ToyotaInfoTech/RAMN/docs/firmware/img/external_clock_settings.png

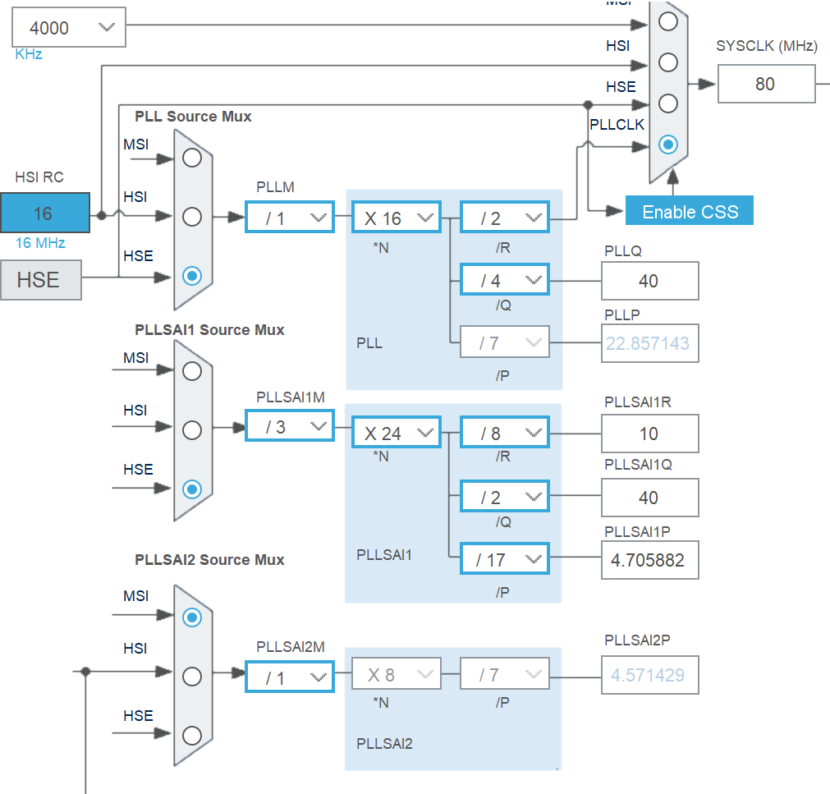
docs/firmware/img/external_clock_settings.png
