ToyotaInfoTech/RAMN/docs/firmware/img/freertos_settings.png

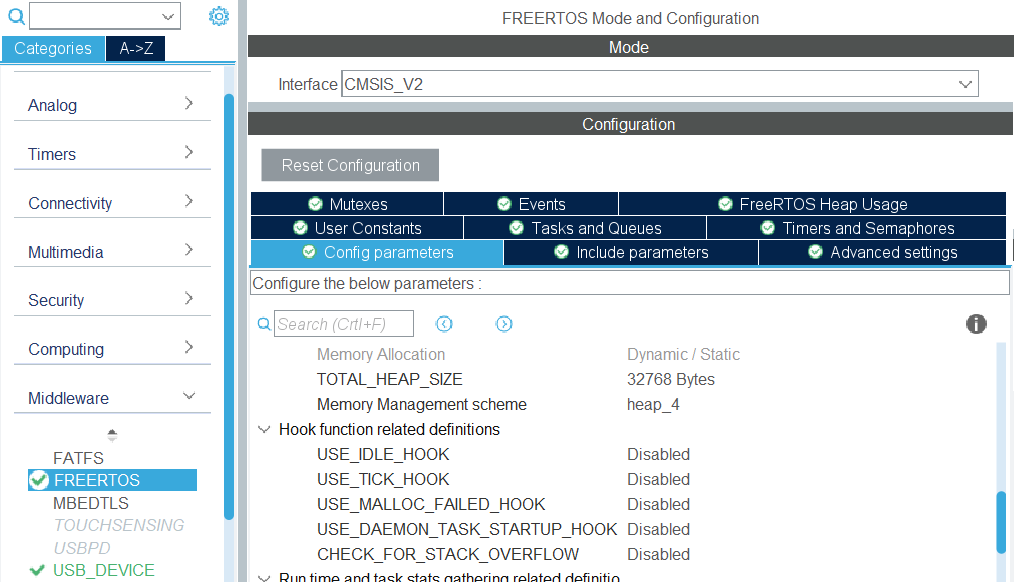
docs/firmware/img/freertos_settings.png
