ToyotaInfoTech/RAMN/docs/firmware/img/internal_clock_settings.png

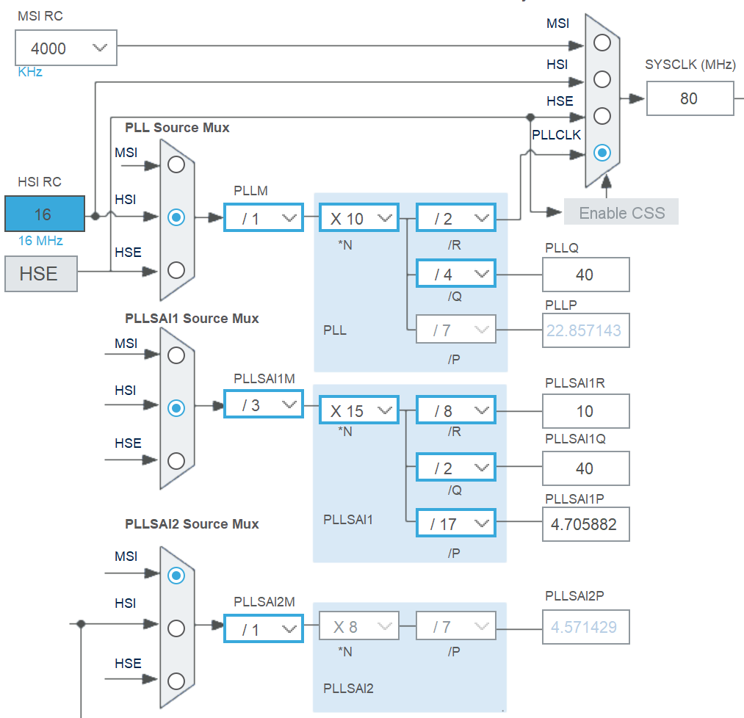
docs/firmware/img/internal_clock_settings.png
