ToyotaInfoTech/RAMN/docs/firmware/img/optionbytes_bootmode.png

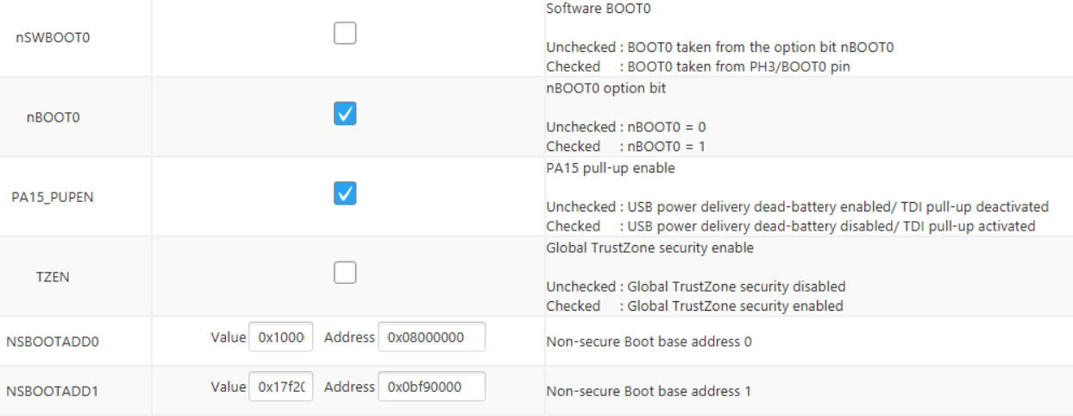
docs/firmware/img/optionbytes_bootmode.png
