ToyotaInfoTech/RAMN/docs/img/writeups/chv_ecub_4.png

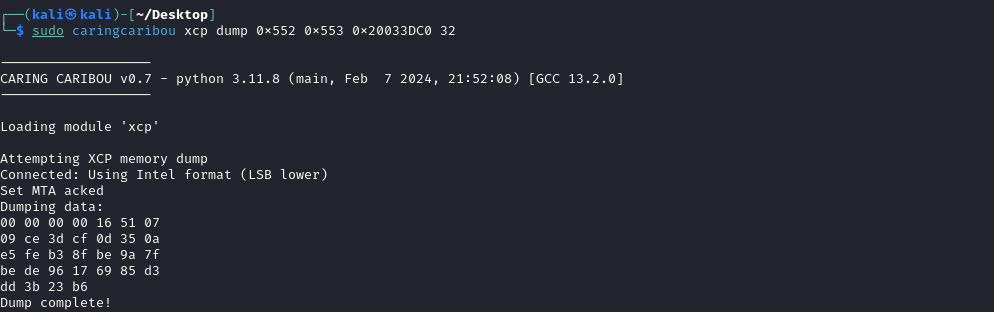
docs/img/writeups/chv_ecub_4.png
