ToyotaInfoTech/RAMN/hardware/V1_revB/0_ramn/CAD/ramn.png

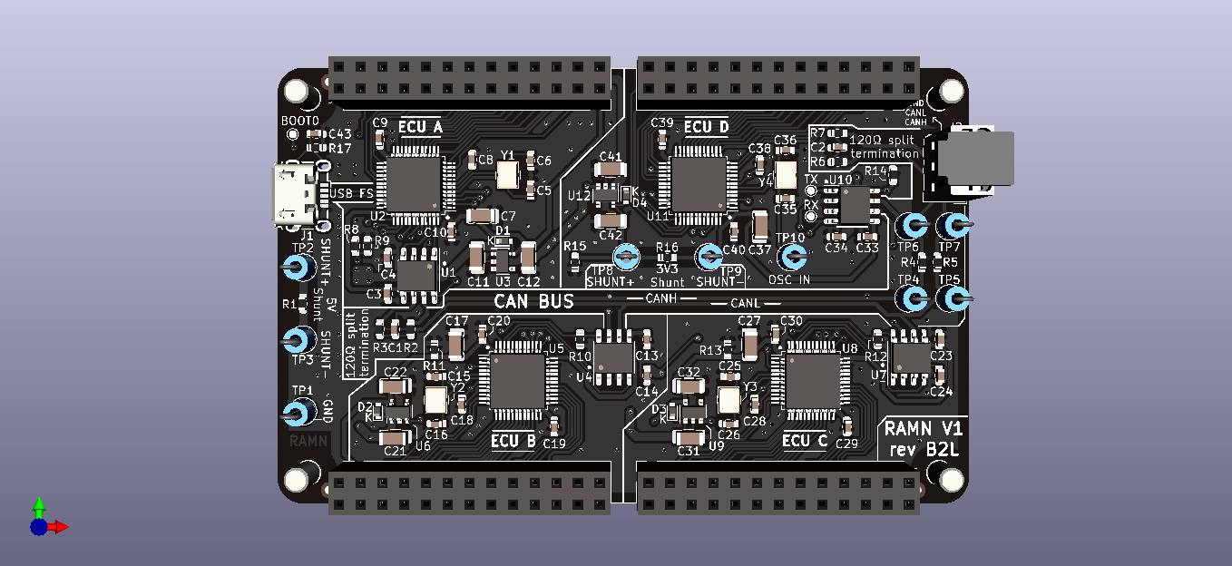
hardware/V1_revB/0_ramn/CAD/ramn.png
