ToyotaInfoTech/RAMN/hardware/V1_revB/0_ramn/CAD/ramn_back.png

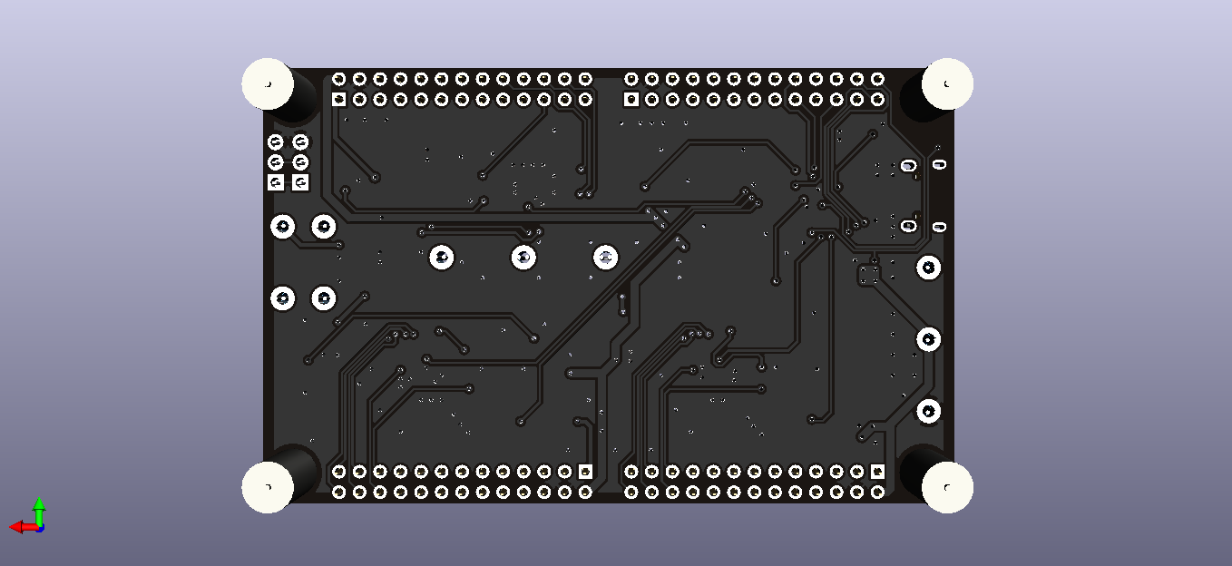
hardware/V1_revB/0_ramn/CAD/ramn_back.png
