ToyotaInfoTech/RAMN/hardware/V1_revB/0_ramn/CAD/ramn_tilt.png

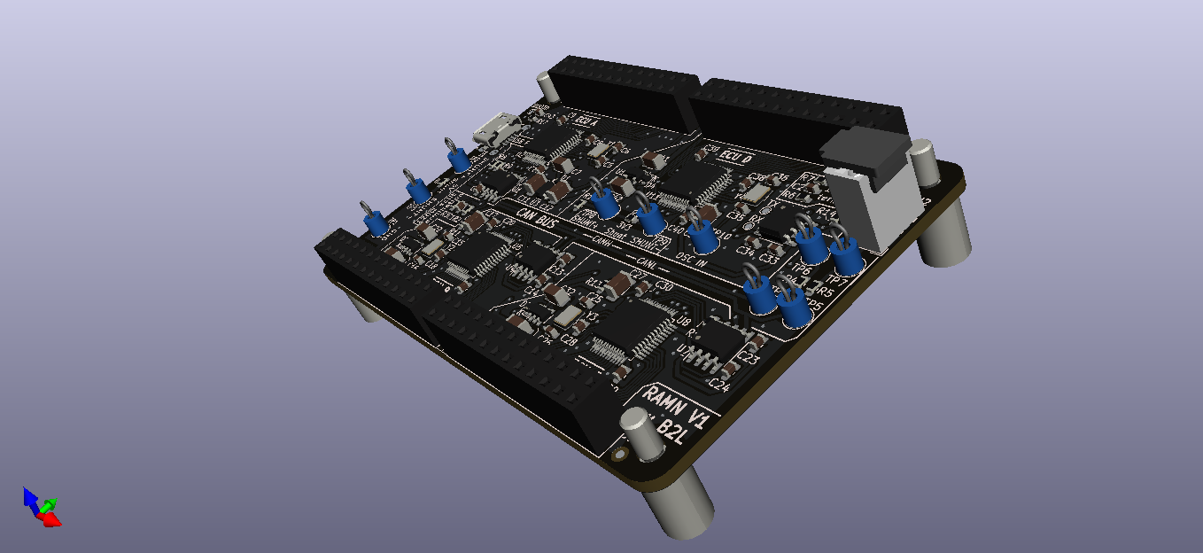
hardware/V1_revB/0_ramn/CAD/ramn_tilt.png
