ToyotaInfoTech/RAMN/scripts/diagnostics/FILES/image.png

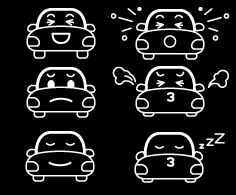
scripts/diagnostics/FILES/image.png
