ToyotaInfoTech/RAMN/docs/userguide.rst

.. _userguide:

User Guide
==========

This section contains the user guide for RAMN, explaining how to use its USB, CAN, and UDS features.
If your goal is to customize RAMN, check the :ref:`customizing_guide`.

.. toctree::
   :maxdepth: 3

   userguide/ramn_introduction
   userguide/can_tutorial
   userguide/isotp_tutorial
   userguide/diag_tutorial
   userguide/usb_tutorial
   userguide/protocol_tutorial
   userguide/going_further
