ToyotaInfoTech/RAMN/docs/hardware/fabrication.rst

.. toctree::
   :maxdepth: 2

   Fabrication/ordering.rst
   Fabrication/flashing.rst
   Fabrication/qualitycheck.rst
