ToyotaInfoTech/RAMN/hardware/V1_revB/0_ramn/ramn.pdf

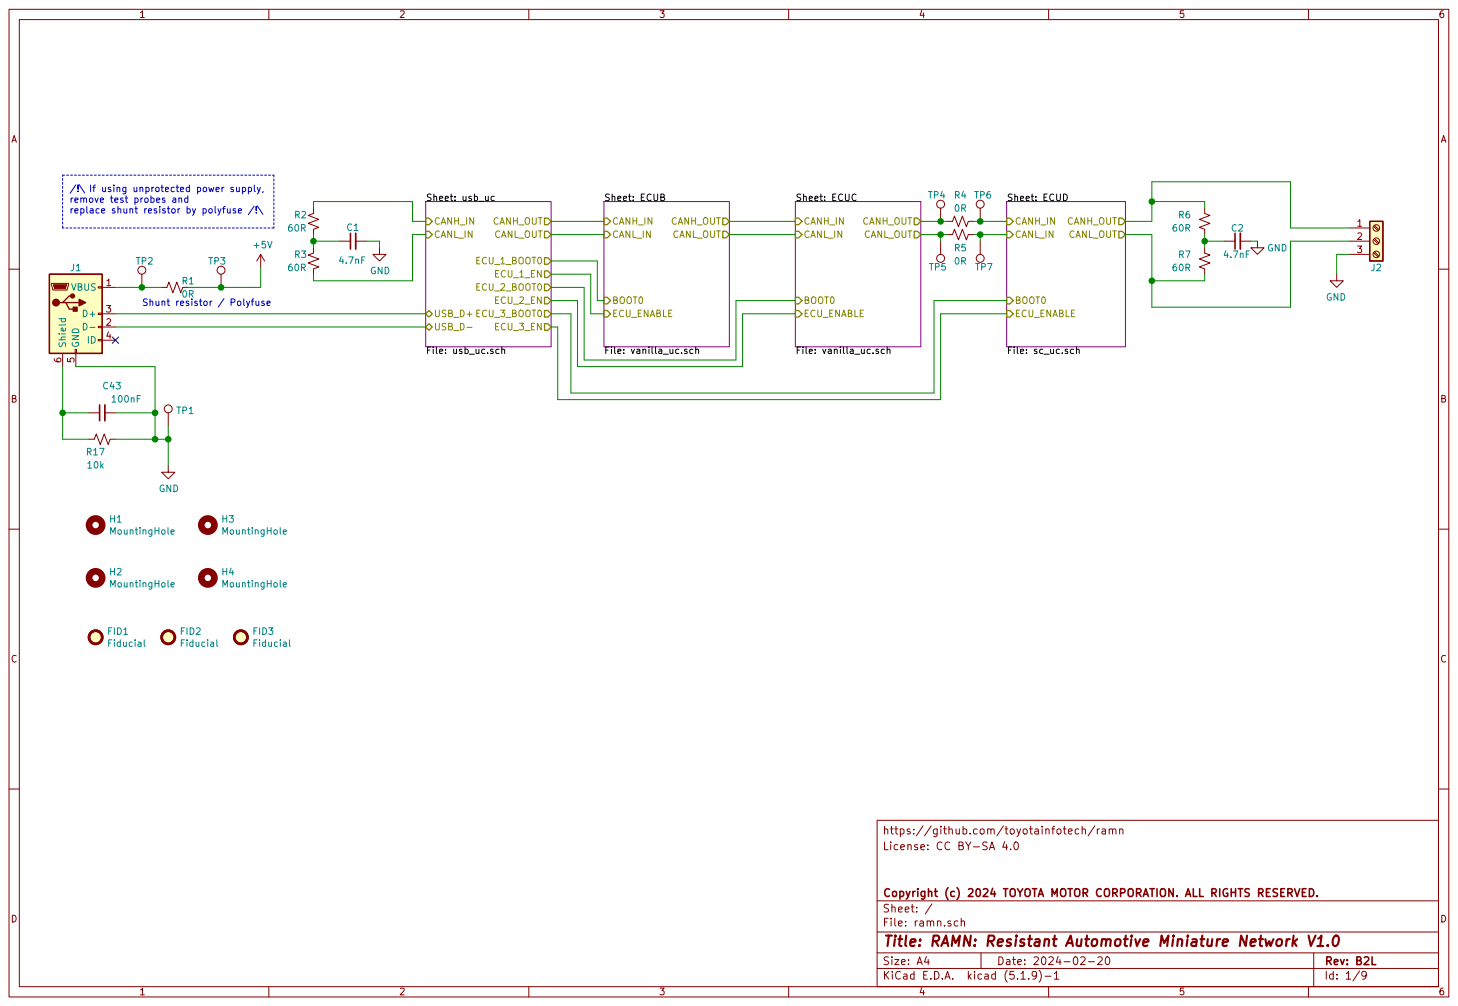
[picture p171: page 1]

/!\ If using unprotected power supply,
remove test probes and
replace shunt resistor by polyfuse /!\

https://github.com/toyotainfotech/ramn
File: ramn.sch Sheet: / Copyright (c) 2024 TOYOTA MOTOR CORPORATION. ALL RIGHTS RESERVED. License: CC BY-SA 4.0

Id: 1/9 Title: RAMN: Resistant Automotive Miniature Network V1.0

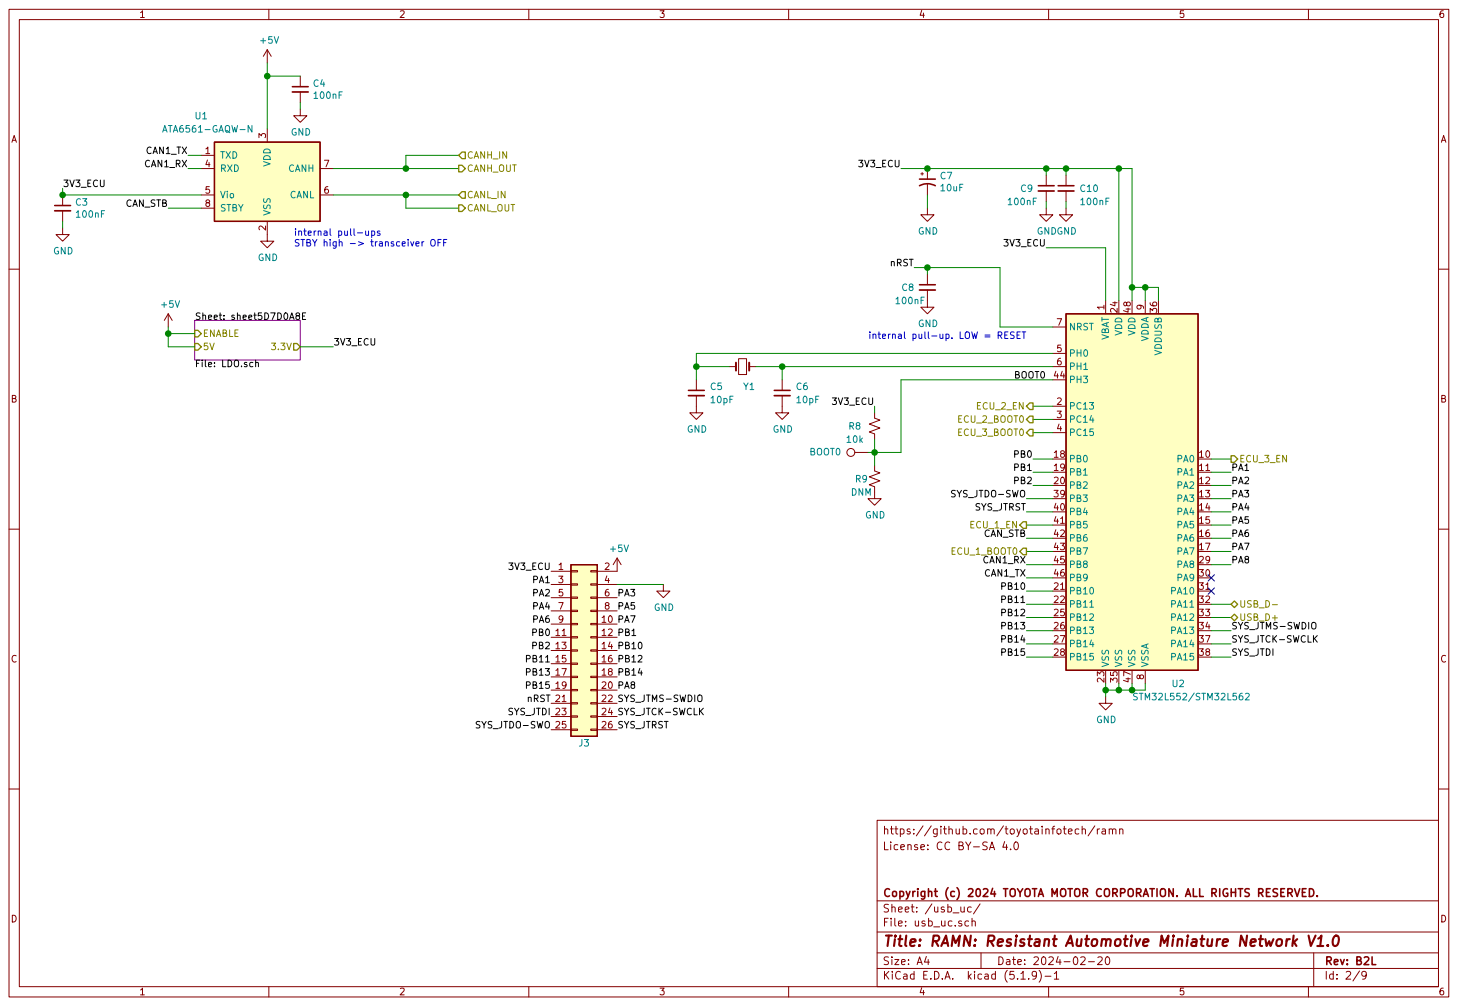
[picture p172: page 2]

3 RXD 4 Vio 5 CANL 6 CANH 7 STBY 8 U1 ATA6561-GAQW-N GND

internal pull-ups
STBY high -> transceiver OFF

9 VDDUSB 36 VSS 23 VSS 35 VSS 47 VSSA

internal pull-up. LOW = RESET

https://github.com/toyotainfotech/ramn
Copyright (c) 2024 TOYOTA MOTOR CORPORATION. ALL RIGHTS RESERVED. License: CC BY-SA 4.0

Sheet: /usb_uc/
File: usb_uc.sch
Id: 2/9 Title: RAMN: Resistant Automotive Miniature Network V1.0

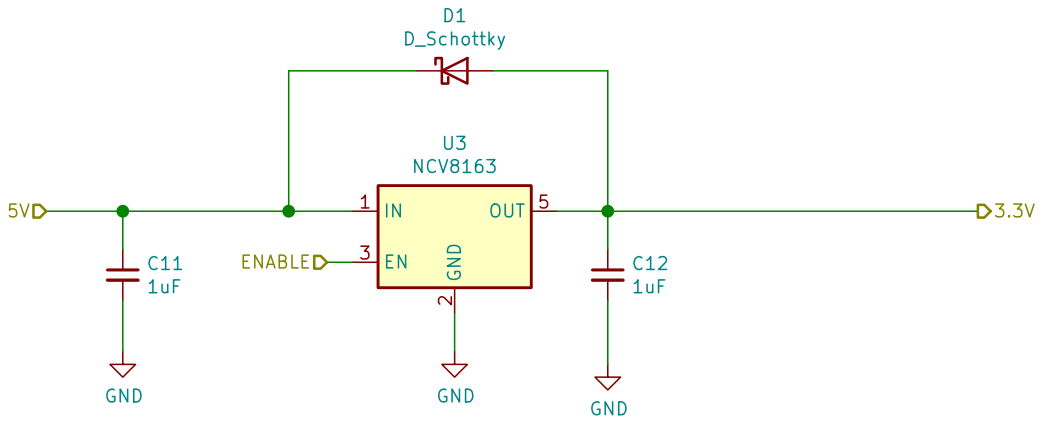
[picture p173: page 3]
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

File: LDO.sch Sheet: /usb_uc/sheet5D7D0A8E/
Id: 3/9 Title: RAMN: Resistant Automotive Miniature Network V1.0

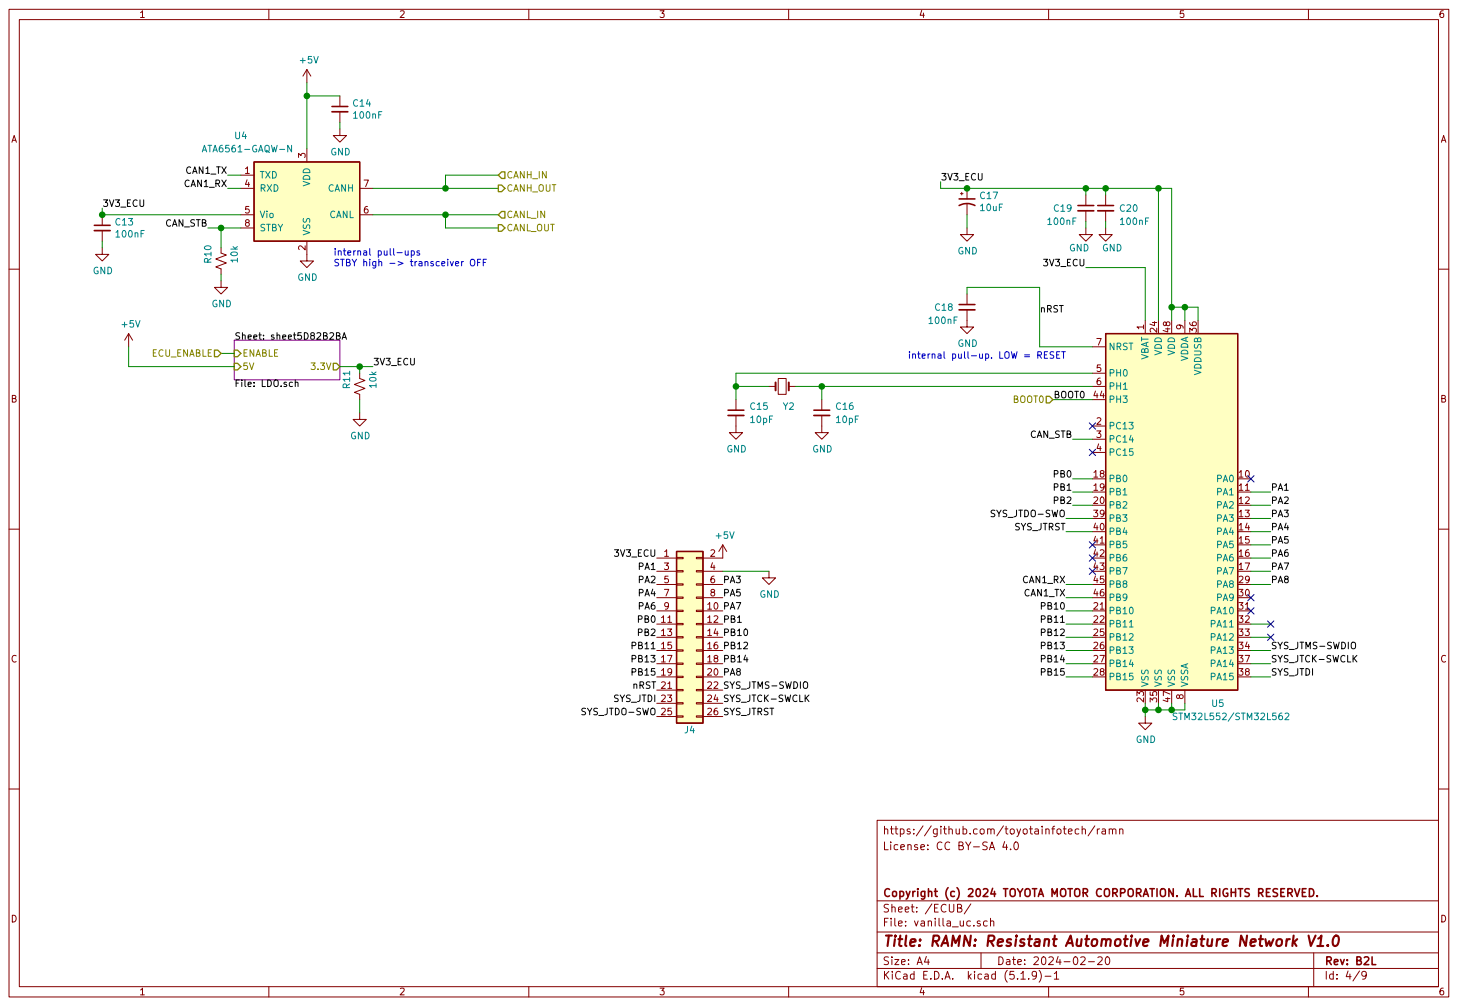
[picture p174: page 4]

3 RXD 4 Vio 5 CANL 6 CANH 7 STBY 8 U4 ATA6561-GAQW-N GND GND GND GND

internal pull-ups
STBY high -> transceiver OFF

9 VDDUSB 36 VSS 23 VSS 35 VSS 47 VSSA

internal pull-up. LOW = RESET

https://github.com/toyotainfotech/ramn
File: vanilla_uc.sch Sheet: /ECUB/ Copyright (c) 2024 TOYOTA MOTOR CORPORATION. ALL RIGHTS RESERVED. License: CC BY-SA 4.0

Id: 4/9 Title: RAMN: Resistant Automotive Miniature Network V1.0

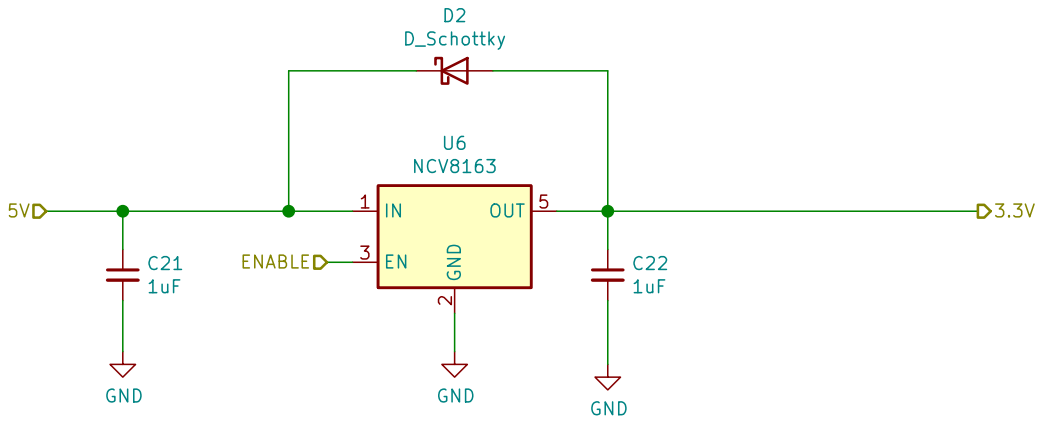
[picture p175: page 5]

https://github.com/toyotainfotech/ramn
File: LDO.sch Sheet: /ECUB/sheet5D82B2BA/ Copyright (c) 2024 TOYOTA MOTOR CORPORATION. ALL RIGHTS RESERVED. License: CC BY-SA 4.0

Id: 5/9 Title: RAMN: Resistant Automotive Miniature Network V1.0

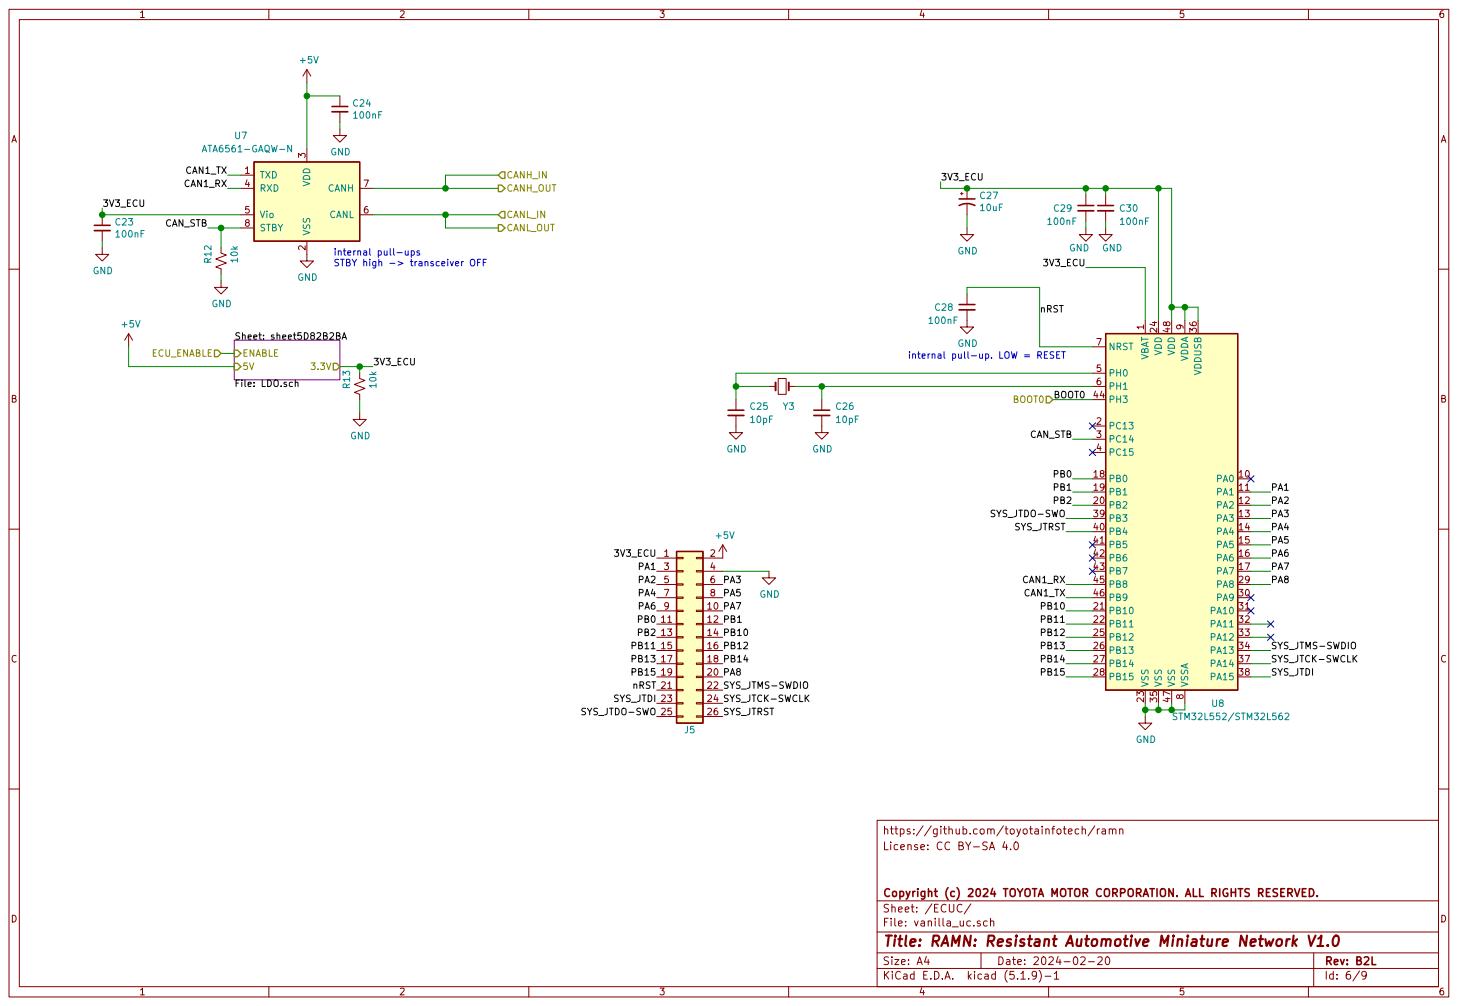
[picture p176: page 6]

3 RXD 4 Vio 5 CANL 6 CANH 7 STBY 8 U7 ATA6561-GAQW-N GND GND GND GND

internal pull-ups
STBY high -> transceiver OFF

9 VDDUSB 36 VSS 23 VSS 35 VSS 47 VSSA

internal pull-up. LOW = RESET

https://github.com/toyotainfotech/ramn
File: vanilla_uc.sch Sheet: /ECUC/ Copyright (c) 2024 TOYOTA MOTOR CORPORATION. ALL RIGHTS RESERVED. License: CC BY-SA 4.0

Id: 6/9 Title: RAMN: Resistant Automotive Miniature Network V1.0

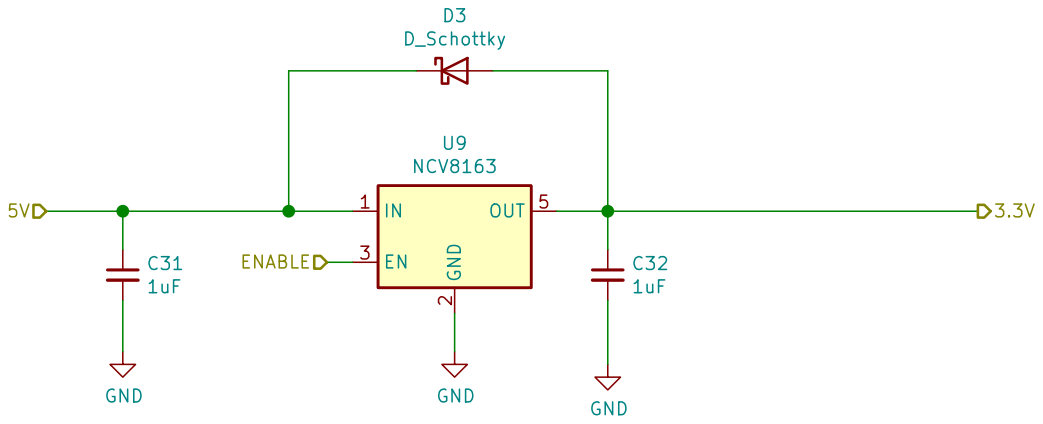
[picture p177: page 7]

https://github.com/toyotainfotech/ramn
File: LDO.sch Sheet: /ECUC/sheet5D82B2BA/ Copyright (c) 2024 TOYOTA MOTOR CORPORATION. ALL RIGHTS RESERVED. License: CC BY-SA 4.0

Id: 7/9 Title: RAMN: Resistant Automotive Miniature Network V1.0

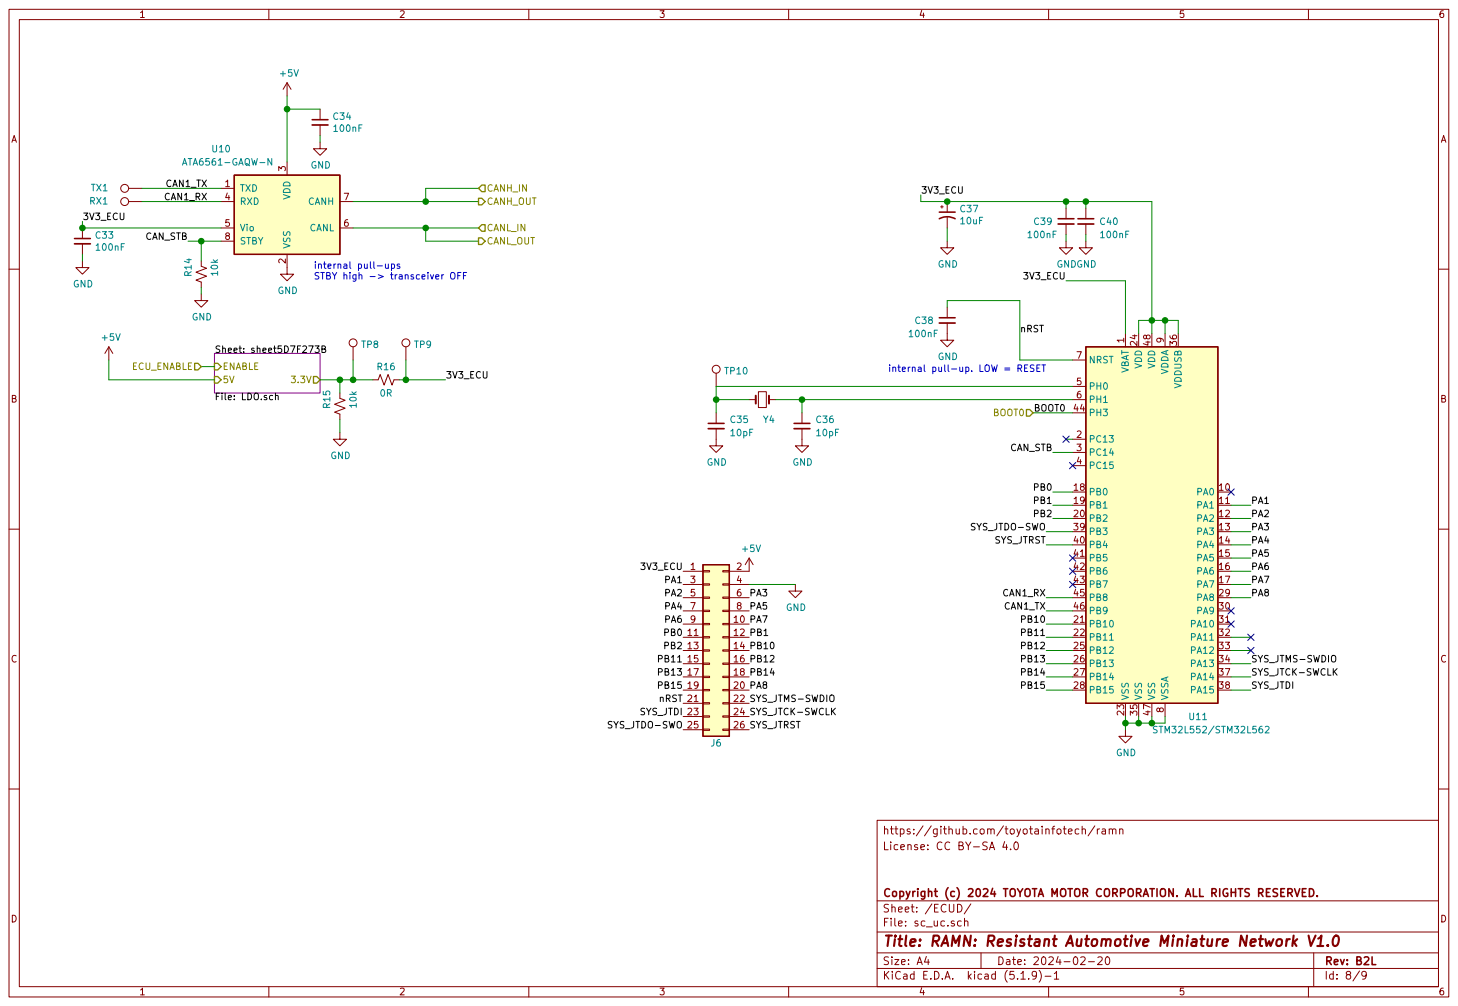
[picture p178: page 8]

3 RXD 4 Vio 5 CANL 6 CANH 7 STBY 8 U10 ATA6561-GAQW-N GND GND

internal pull-ups
STBY high -> transceiver OFF

9 VDDUSB 36 VSS 23 VSS 35 VSS 47 VSSA

internal pull-up. LOW = RESET

https://github.com/toyotainfotech/ramn
File: sc_uc.sch Sheet: /ECUD/ Copyright (c) 2024 TOYOTA MOTOR CORPORATION. ALL RIGHTS RESERVED. License: CC BY-SA 4.0

Id: 8/9 Title: RAMN: Resistant Automotive Miniature Network V1.0

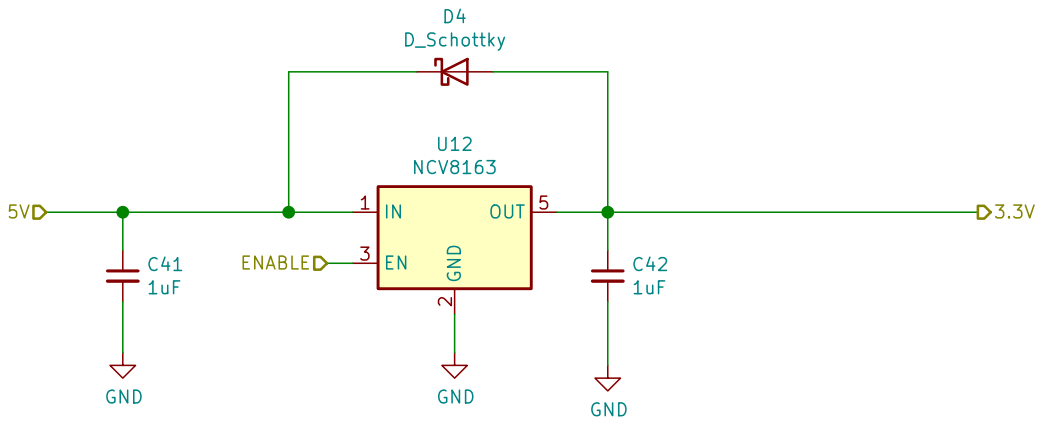
[picture p179: page 9]

https://github.com/toyotainfotech/ramn
File: LDO.sch Sheet: /ECUD/sheet5D7F273B/ Copyright (c) 2024 TOYOTA MOTOR CORPORATION. ALL RIGHTS RESERVED. License: CC BY-SA 4.0

Id: 9/9 Title: RAMN: Resistant Automotive Miniature Network V1.0
