ToyotaInfoTech/RAMN/hardware/V1_revB/1_screens/screens.pdf

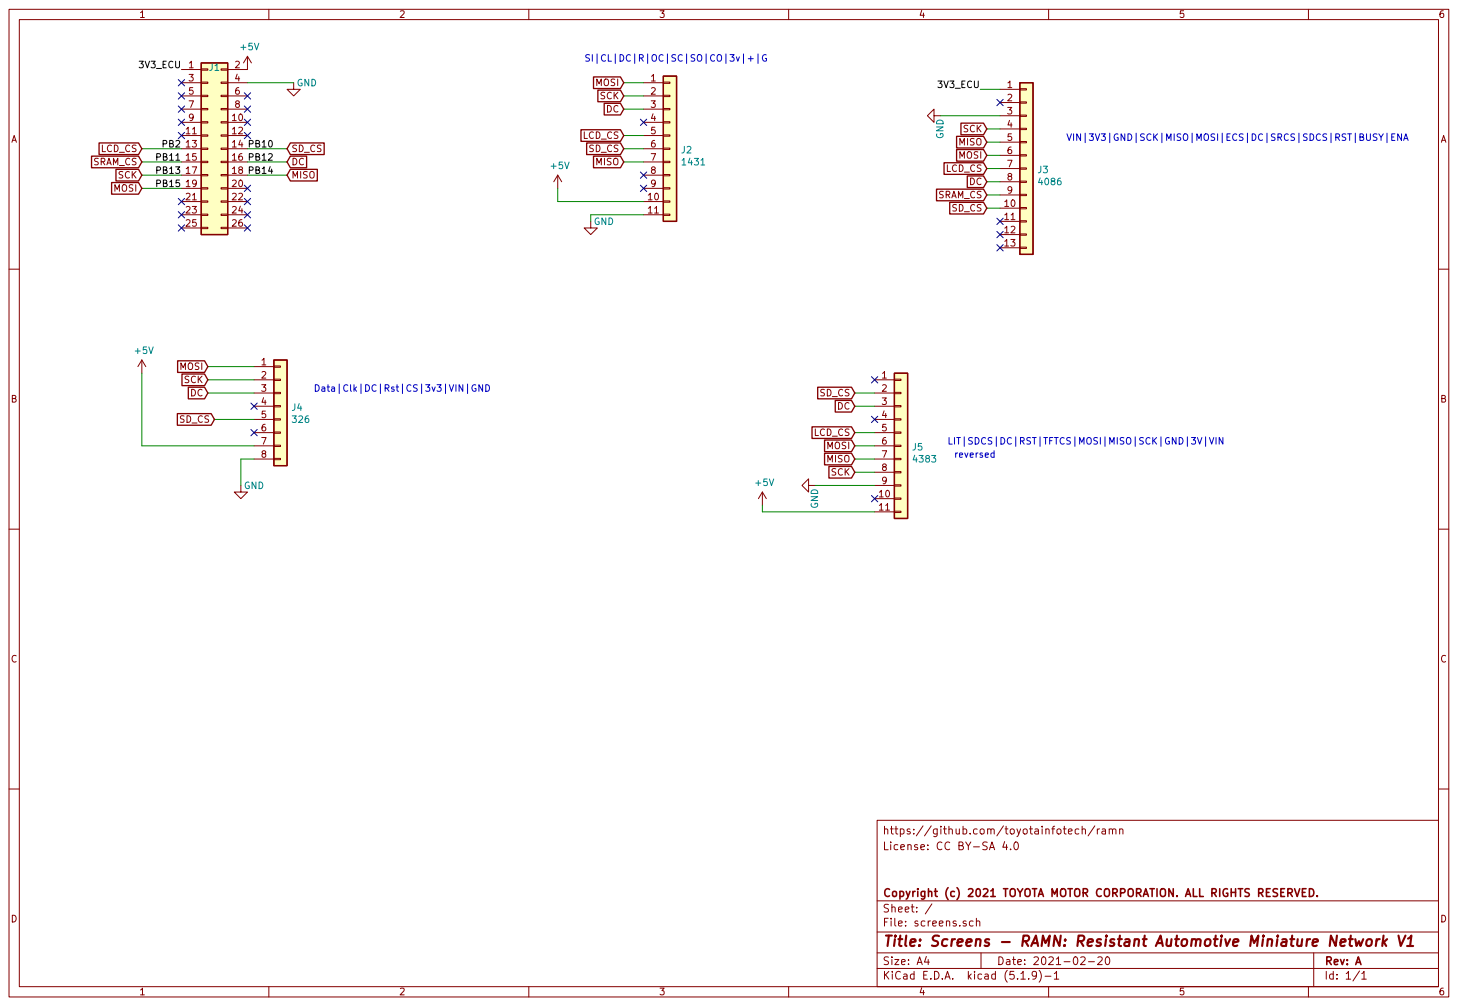
[picture p180: page 1]

reversed SI|CL|DC|R|OC|SC|SO|CO|3v|+|G

VIN|3V3|GND|SCK|MISO|MOSI|ECS|DC|SRCS|SDCS|RST|BUSY|ENA

Data|Clk|DC|Rst|CS|3v3|VIN|GND

LIT|SDCS|DC|RST|TFTCS|MOSI|MISO|SCK|GND|3V|VIN

https://github.com/toyotainfotech/ramn
File: screens.sch Sheet: / Copyright (c) 2021 TOYOTA MOTOR CORPORATION. ALL RIGHTS RESERVED. License: CC BY-SA 4.0

Id: 1/1 Title: Screens - RAMN: Resistant Automotive Miniature Network V1
