ToyotaInfoTech/RAMN/hardware/V1_revB/2_chassis/chassis.pdf

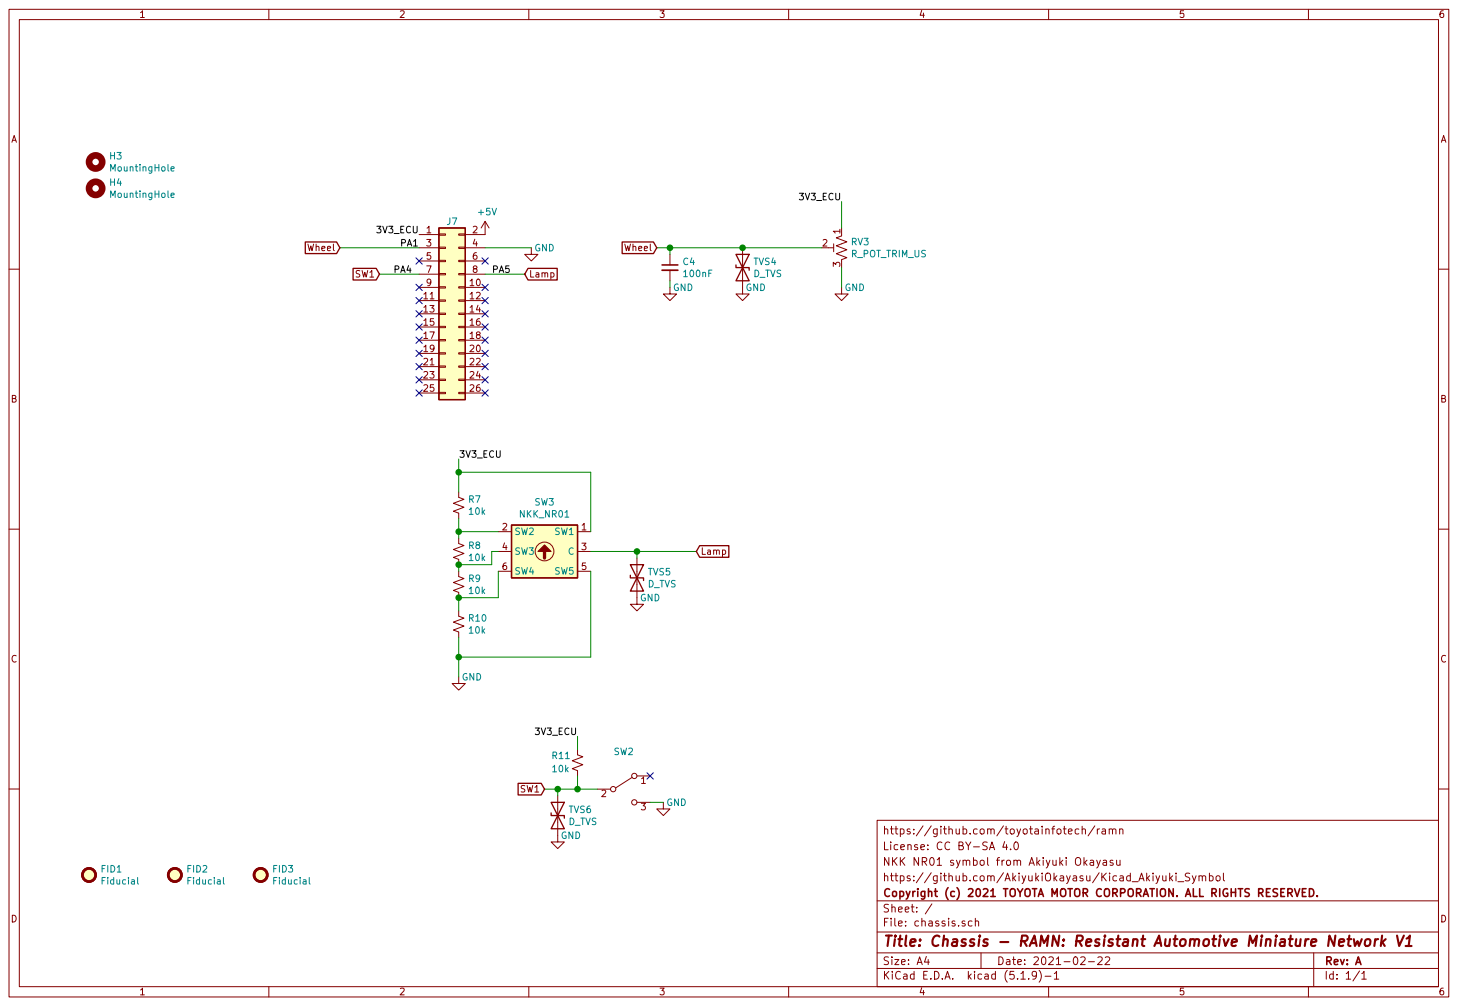
[picture p181: page 1]

https://github.com/toyotainfotech/ramn
License: CC BY-SA 4.0
NKK NR01 symbol from Akiyuki Okayasu
https://github.com/AkiyukiOkayasu/Kicad_Akiyuki_Symbol
File: chassis.sch Sheet: / Copyright (c) 2021 TOYOTA MOTOR CORPORATION. ALL RIGHTS RESERVED.

Id: 1/1 Title: Chassis - RAMN: Resistant Automotive Miniature Network V1
