ToyotaInfoTech/RAMN/hardware/V1_revB/3_powertrain/powertrain.pdf

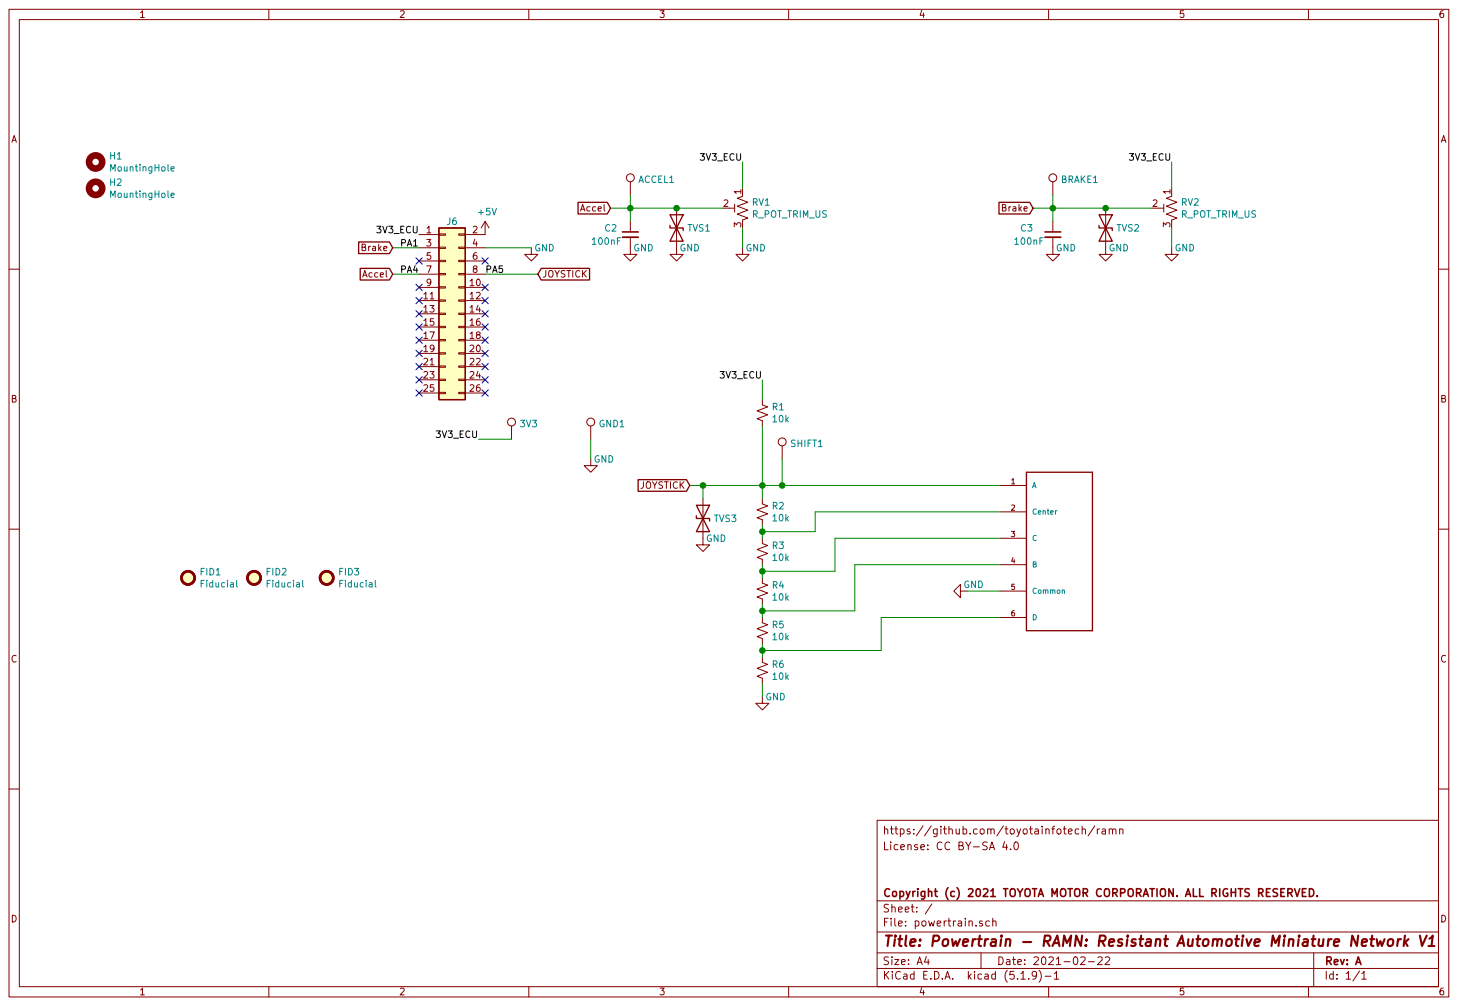
[picture p182: page 1]

3 RV1 R_POT_TRIM_US H2MountingHole H1MountingHole TVS2 FID2 Fiducial +5V GND GND GND

https://github.com/toyotainfotech/ramn
File: powertrain.sch Sheet: / Copyright (c) 2021 TOYOTA MOTOR CORPORATION. ALL RIGHTS RESERVED. License: CC BY-SA 4.0

Id: 1/1 Title: Powertrain - RAMN: Resistant Automotive Miniature Network V1
