ToyotaInfoTech/RAMN/hardware/V1_revB/4_body/body.pdf

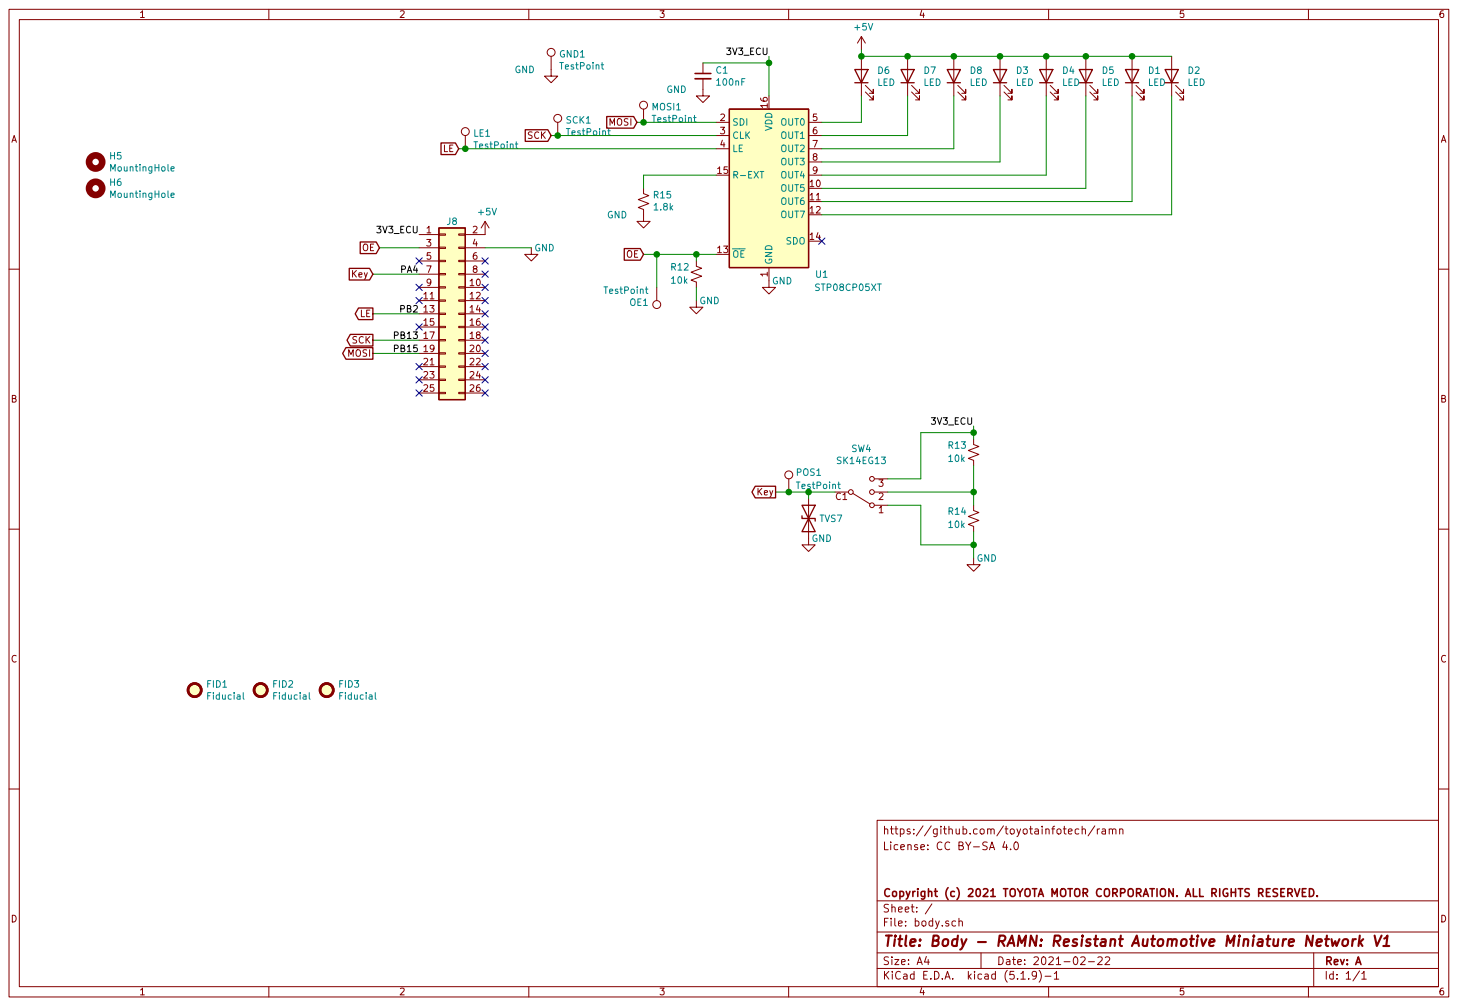
[picture p183: page 1]

1 OUT5 10 OUT6 11 OUT7 12 OE 13 SDO 14 R-EXT 15 VDD 16 SDI 2 CLK 3

https://github.com/toyotainfotech/ramn
File: body.sch Sheet: / Copyright (c) 2021 TOYOTA MOTOR CORPORATION. ALL RIGHTS RESERVED. License: CC BY-SA 4.0

Id: 1/1 Title: Body - RAMN: Resistant Automotive Miniature Network V1
