ToyotaInfoTech/RAMN/hardware/V1_revB/1_screens/CAD/screens-F_SilkS.pdf

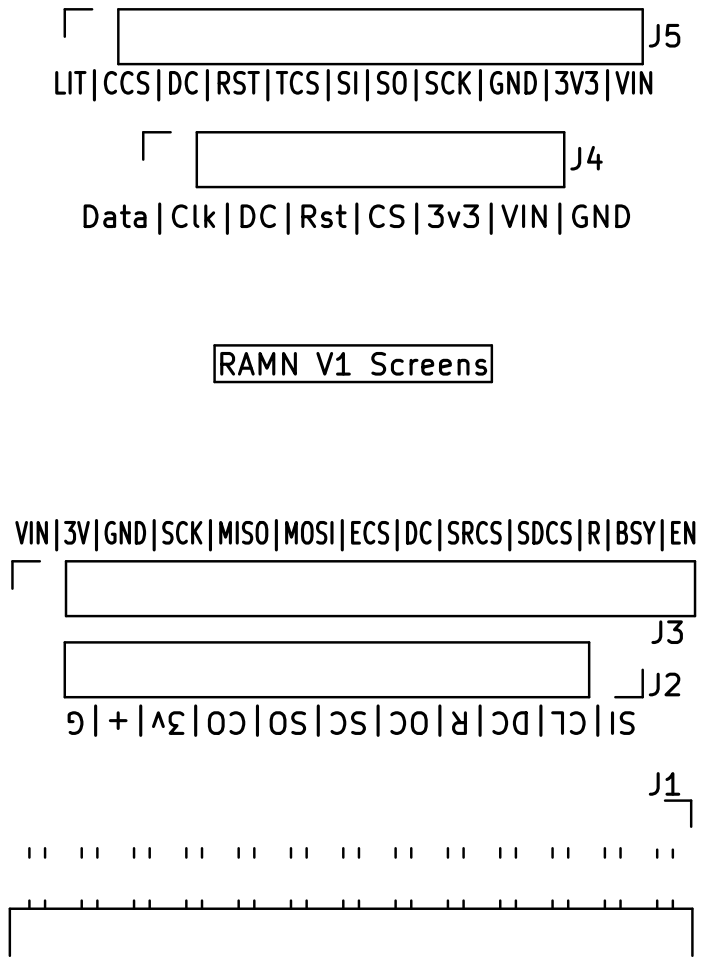
[picture p184: page 1]

LIT|CCS|DC|RST|TCS|SI|SO|SCK|GND|3V3|VIN

Data|Clk|DC|Rst|CS|3v3|VIN|GND

RAMN V1 Screens VIN|3V|GND|SCK|MISO|MOSI|ECS|DC|SRCS|SDCS|R|BSY|EN
