ToyotaInfoTech/RAMN/hardware/V1_revB/4_body/CAD/body-F_SilkS.pdf

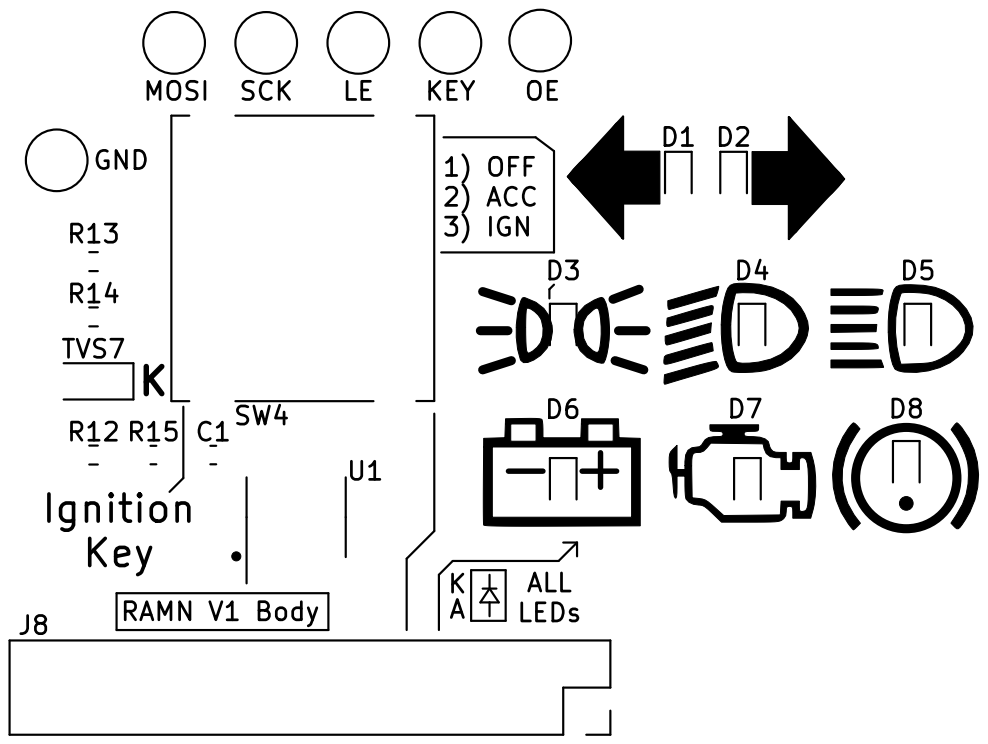
[picture p185: page 1]

RAMN V1 Body LE GND
