ToyotaInfoTech/RAMN/hardware/V1_revB/3_powertrain/CAD/powertrain-B_Cu.pdf

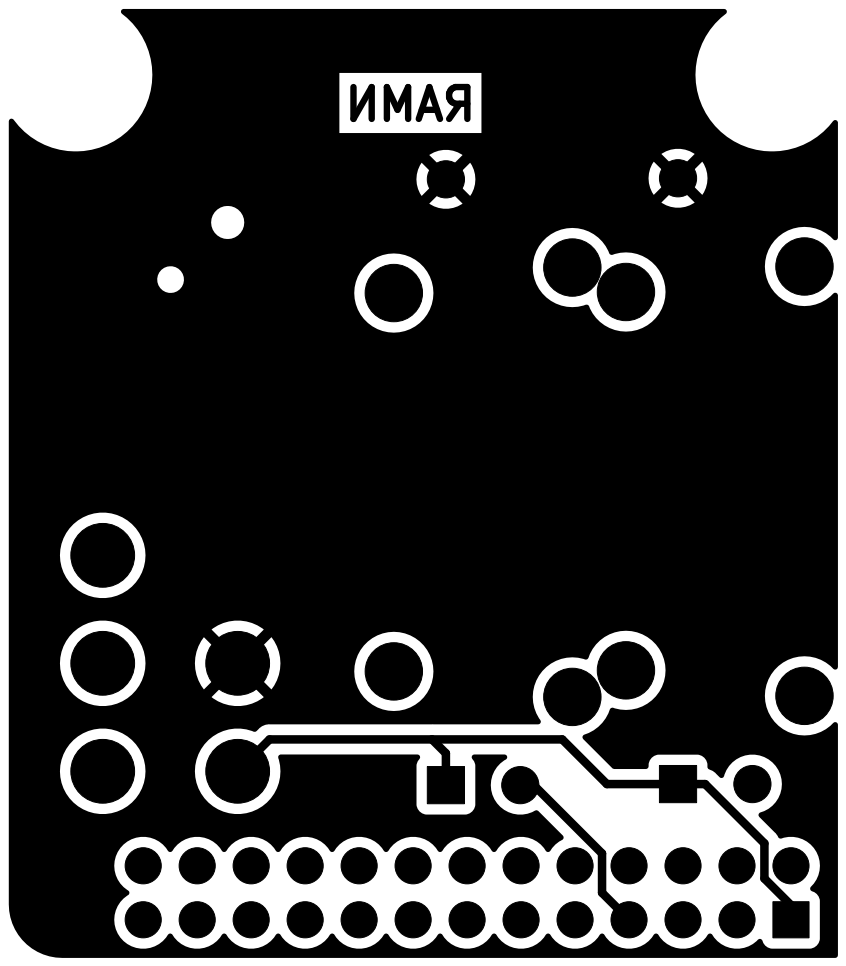
[picture p190: page 1]
