ToyotaInfoTech/RAMN/hardware/V1_revB/3_powertrain/CAD/powertrain-B_Mask.pdf

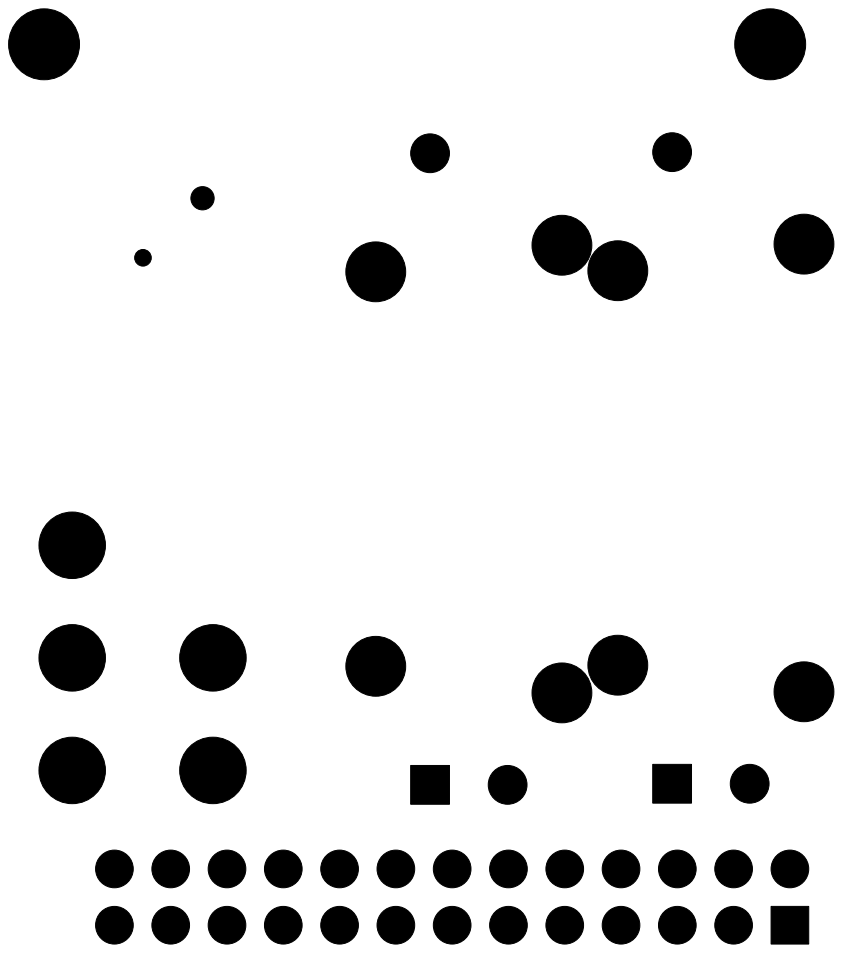
[picture p191: page 1]
