ToyotaInfoTech/RAMN/hardware/V1_revB/3_powertrain/CAD/powertrain-Edge_Cuts.pdf

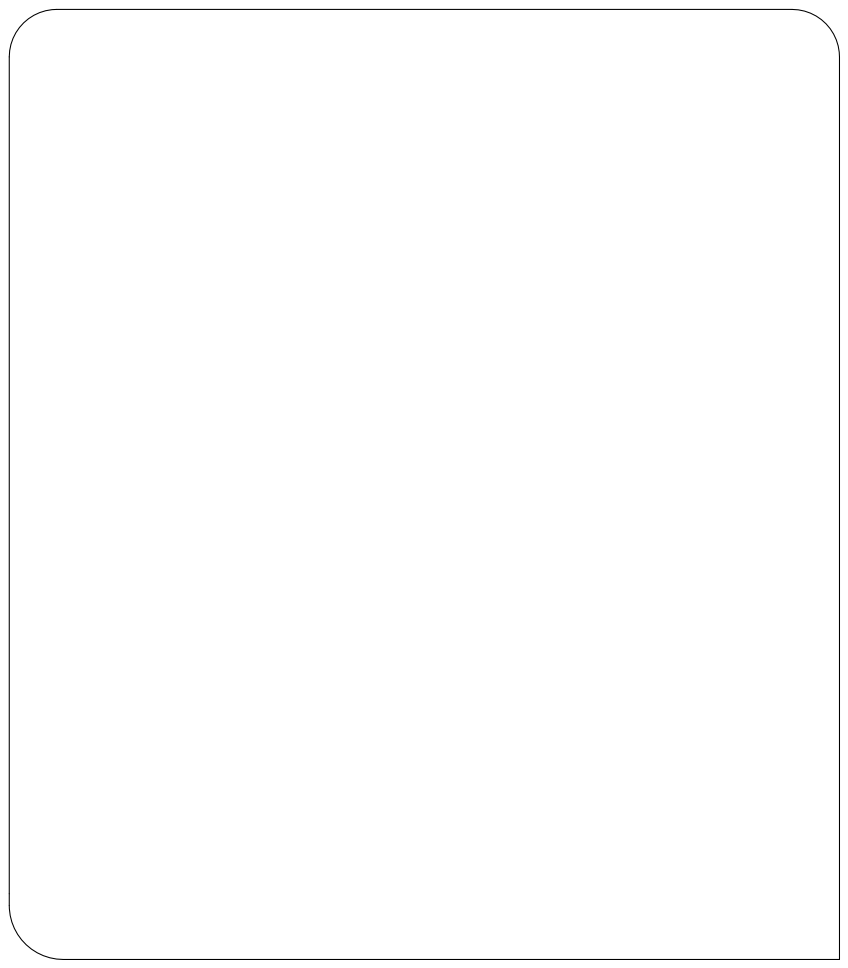
[picture p192: page 1]
