ToyotaInfoTech/RAMN/hardware/V1_revB/3_powertrain/CAD/powertrain-F_Cu.pdf

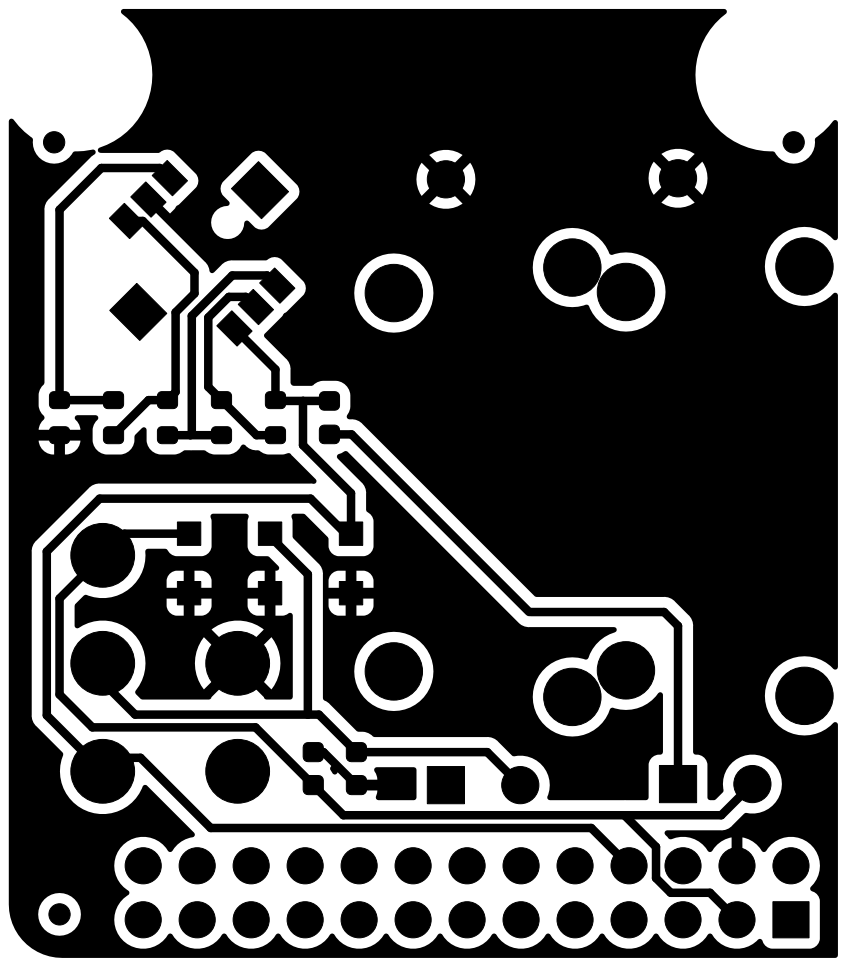
[picture p193: page 1]
