ToyotaInfoTech/RAMN/hardware/V1_revB/3_powertrain/CAD/powertrain-F_Mask.pdf

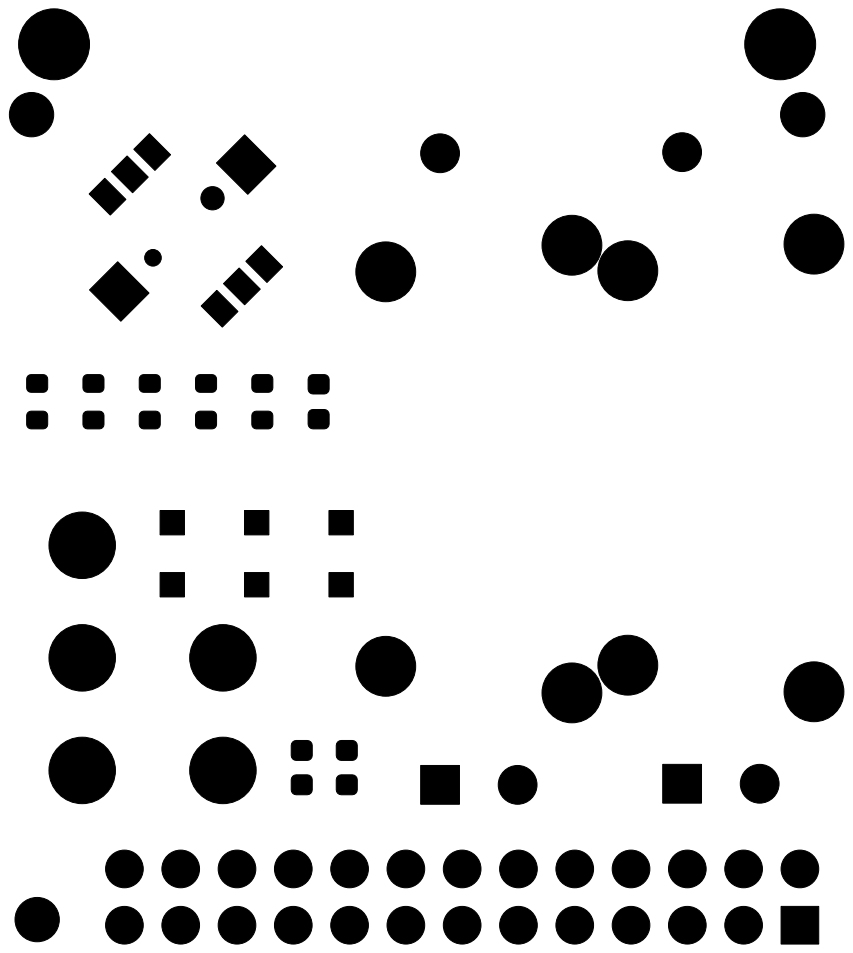
[picture p194: page 1]
