ToyotaInfoTech/RAMN/hardware/V1_revB/3_powertrain/CAD/powertrain-F_Paste.pdf

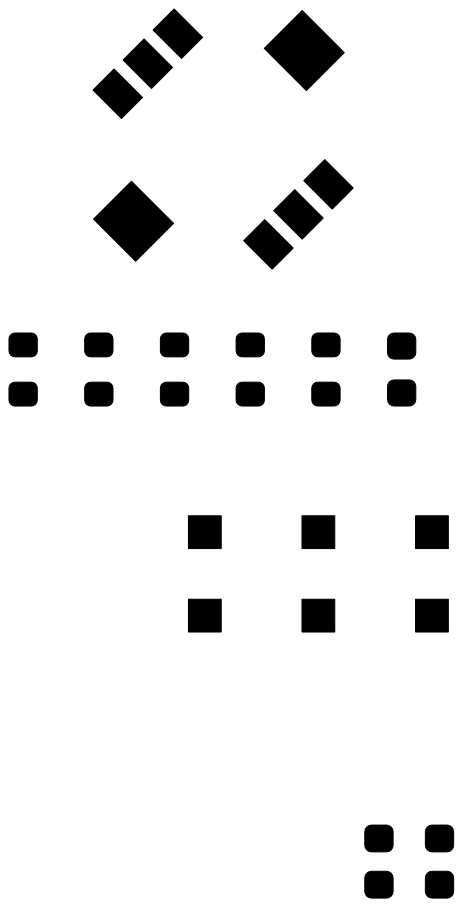
[picture p195: page 1]
