ToyotaInfoTech/RAMN/hardware/V1_revB/3_powertrain/CAD/powertrain-F_SilkS.pdf

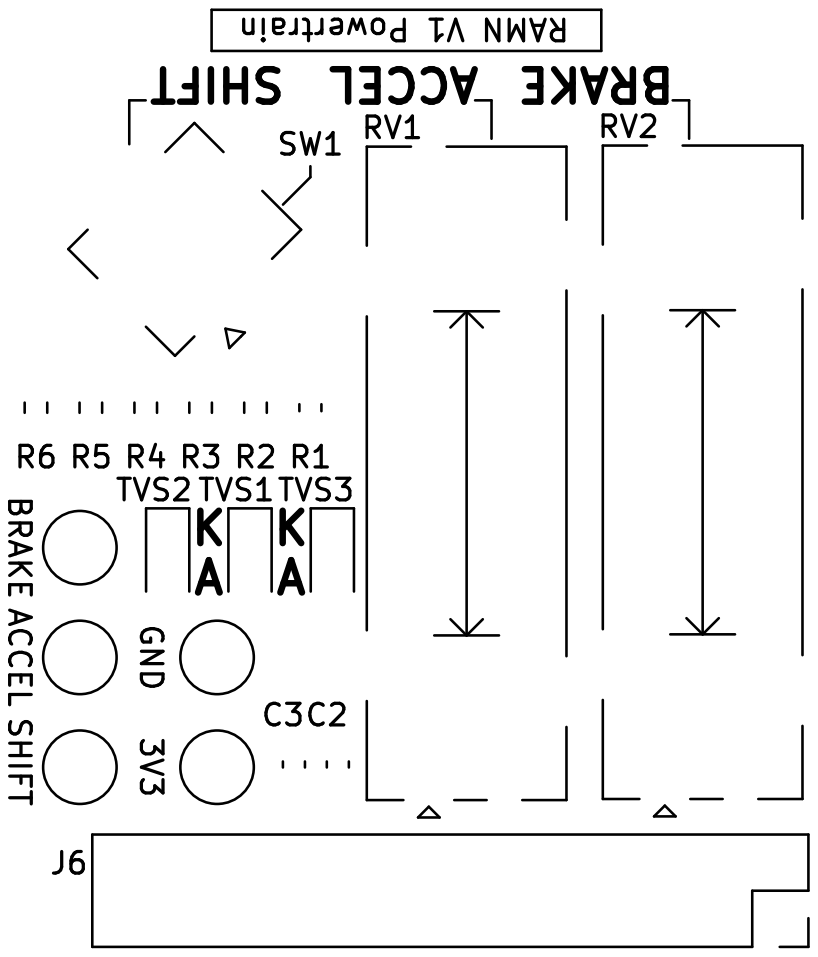
[picture p196: page 1]
