ToyotaInfoTech/RAMN/hardware/V1_revB/0_ramn/CAD/ramn-B_Cu.pdf

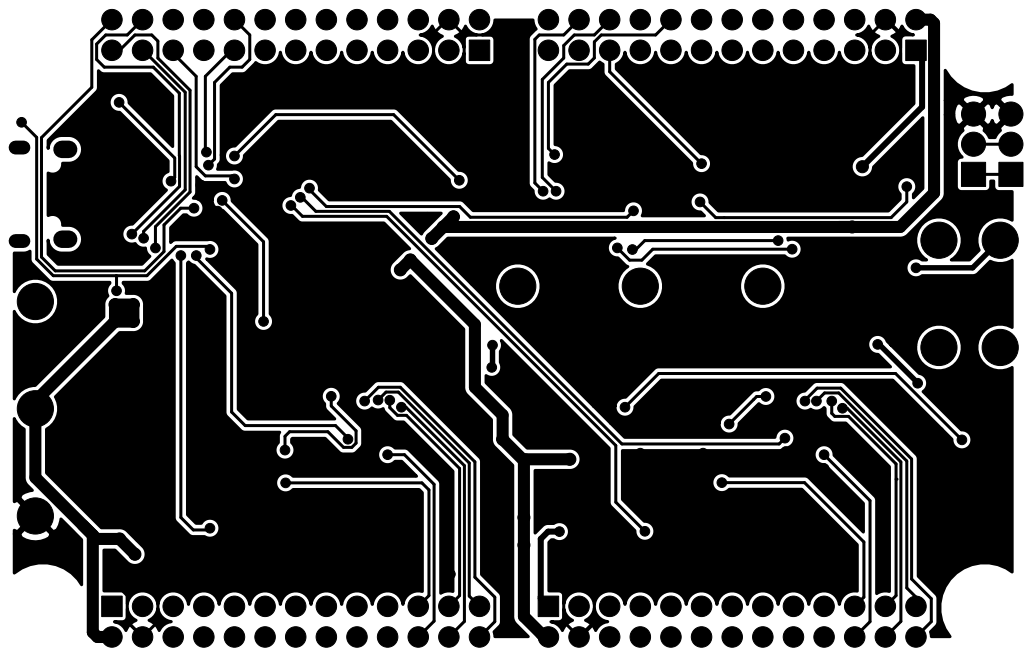
[picture p197: page 1]
