ToyotaInfoTech/RAMN/hardware/V1_revB/0_ramn/CAD/ramn-B_Mask.pdf

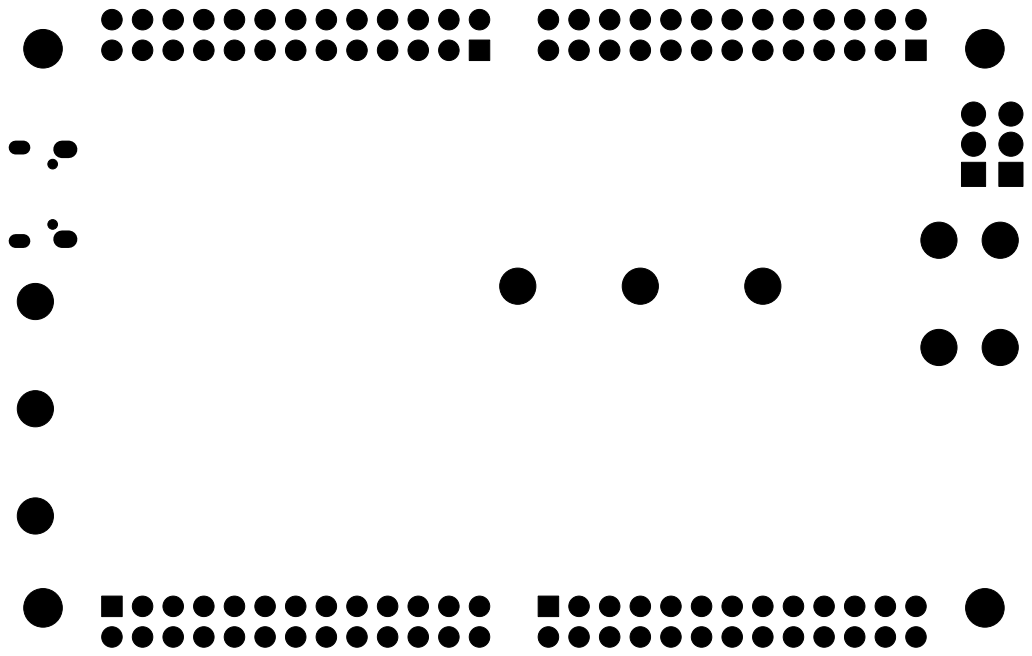
[picture p198: page 1]
