ToyotaInfoTech/RAMN/hardware/V1_revB/0_ramn/CAD/ramn-Edge_Cuts.pdf

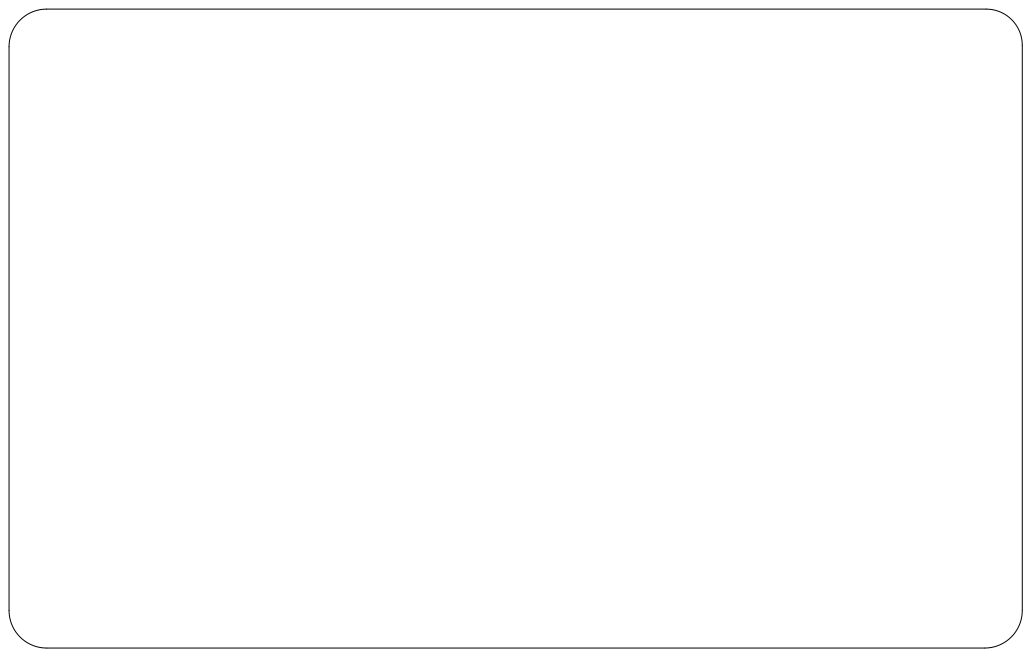
[picture p199: page 1]
