ToyotaInfoTech/RAMN/hardware/V1_revB/0_ramn/CAD/ramn-F_Cu.pdf

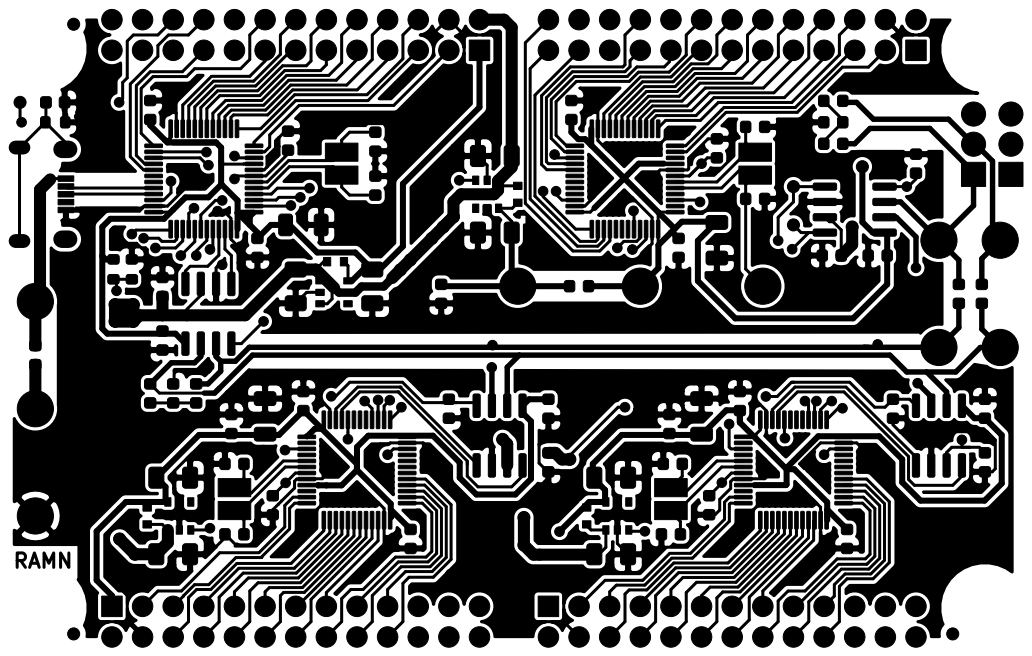
[picture p200: page 1]
