ToyotaInfoTech/RAMN/hardware/V1_revB/0_ramn/CAD/ramn-F_Mask.pdf

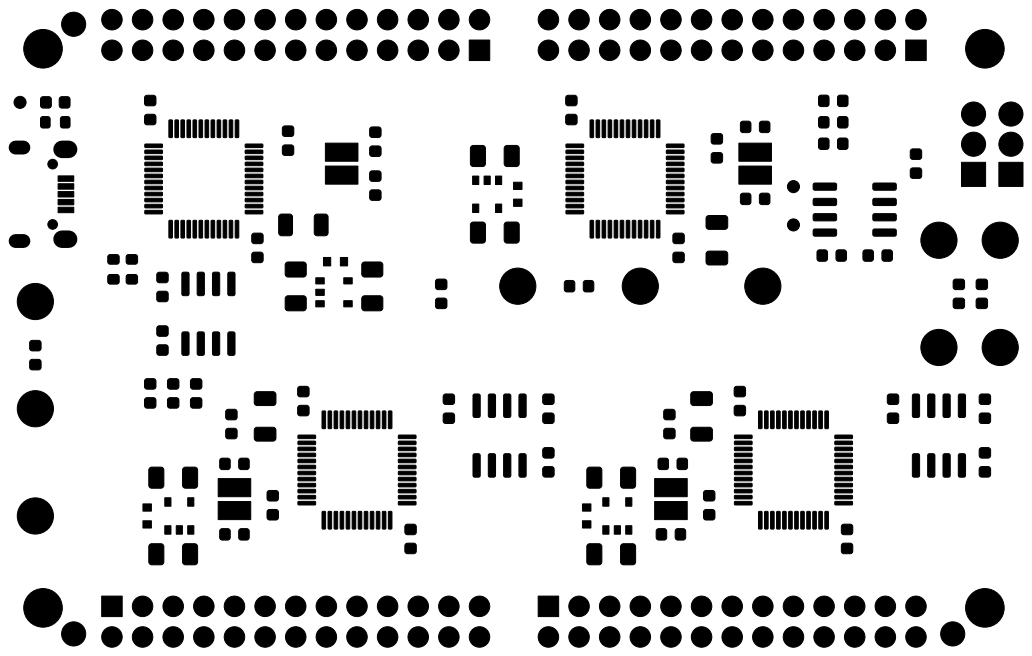
[picture p201: page 1]
