ToyotaInfoTech/RAMN/hardware/V1_revB/0_ramn/CAD/ramn-F_Paste.pdf

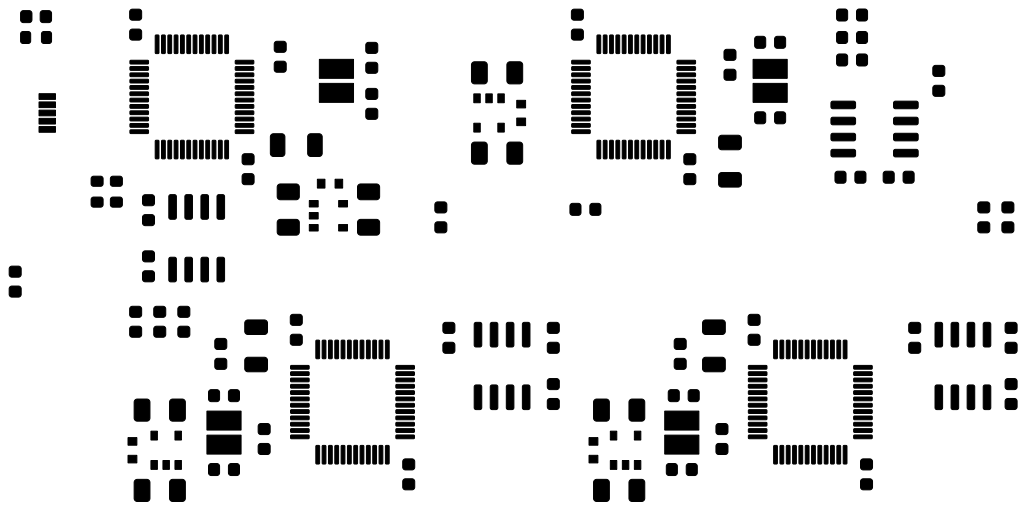
[picture p202: page 1]
