ToyotaInfoTech/RAMN/hardware/V1_revB/0_ramn/CAD/ramn-F_SilkS.pdf

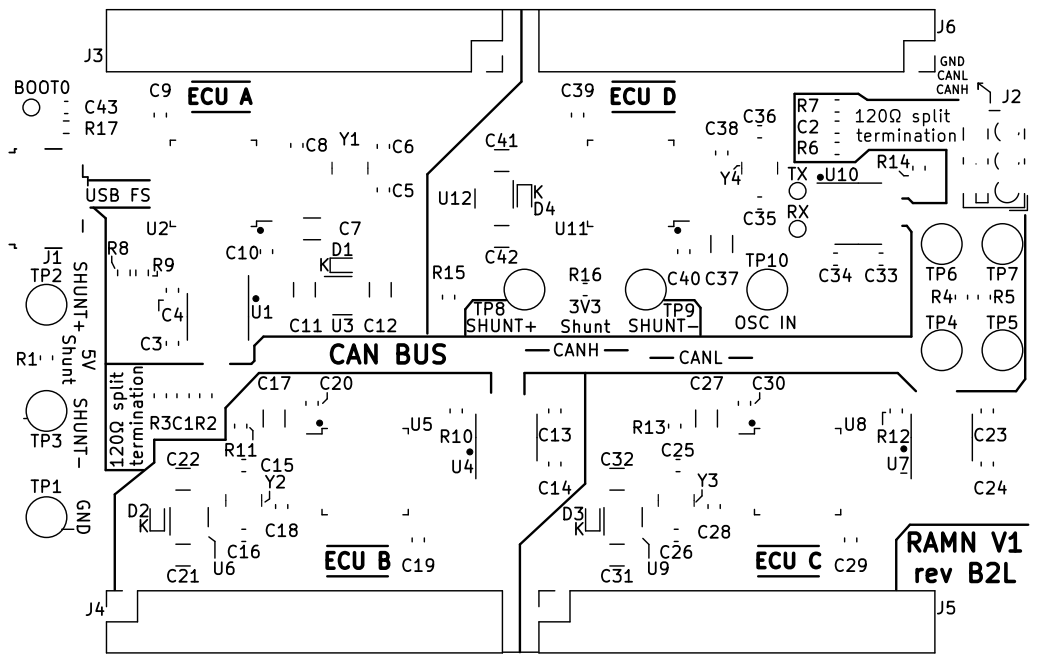
[picture p203: page 1]
