ToyotaInfoTech/RAMN/hardware/V1_revB/2_chassis/CAD/chassis-B_Cu.pdf

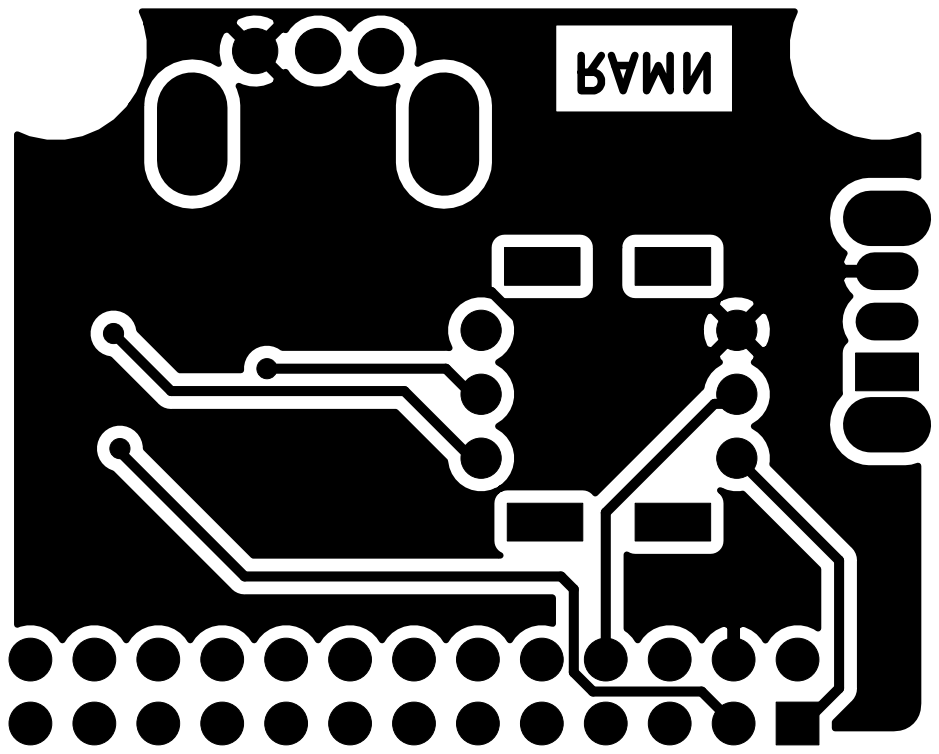
[picture p204: page 1]
