ToyotaInfoTech/RAMN/hardware/V1_revB/2_chassis/CAD/chassis-B_Mask.pdf

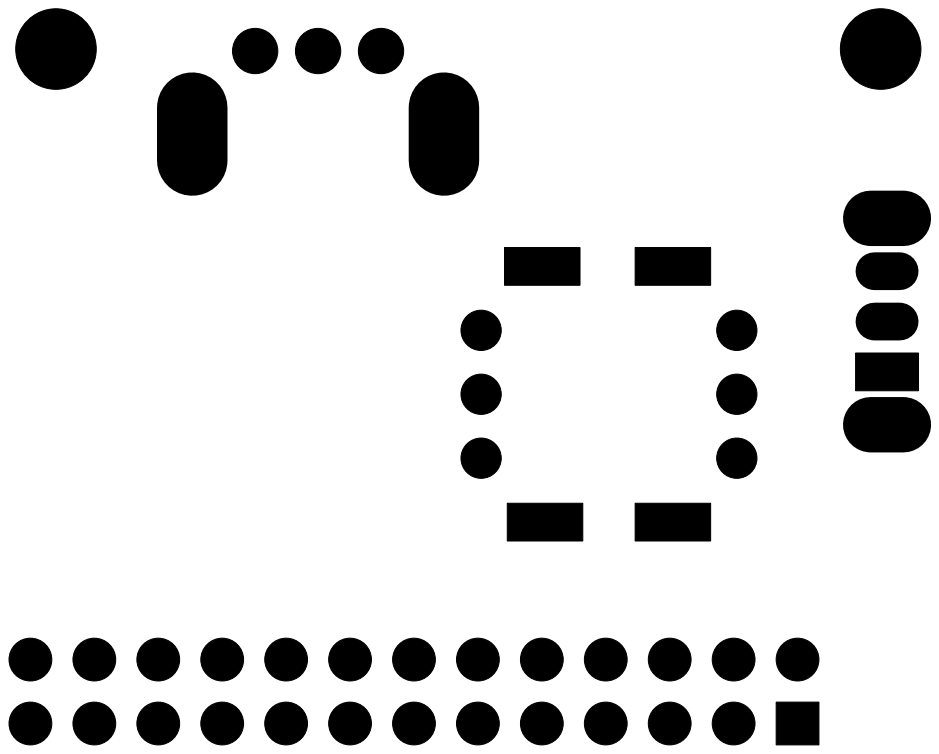
[picture p205: page 1]
