ToyotaInfoTech/RAMN/hardware/V1_revB/2_chassis/CAD/chassis-Edge_Cuts.pdf

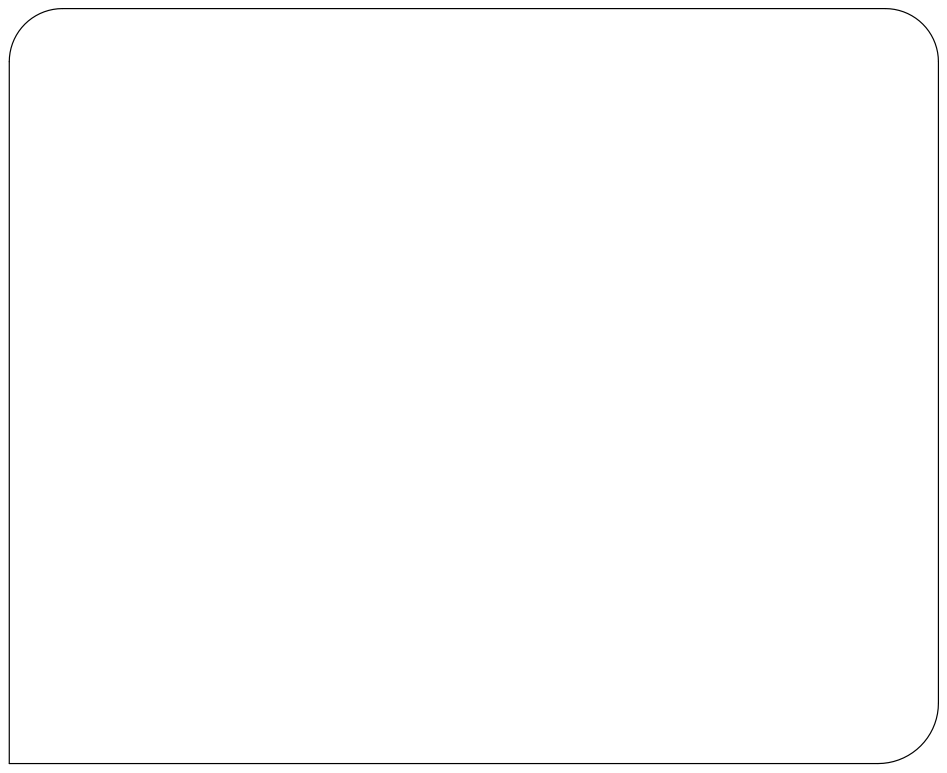
[picture p206: page 1]
