ToyotaInfoTech/RAMN/hardware/V1_revB/2_chassis/CAD/chassis-F_Cu.pdf

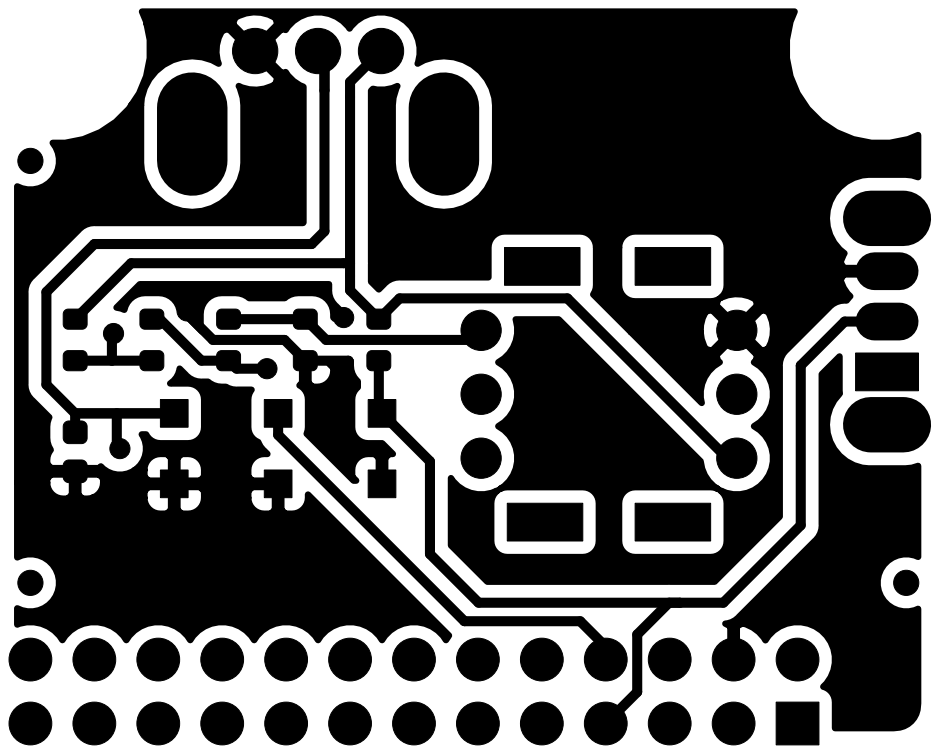
[picture p207: page 1]
