ToyotaInfoTech/RAMN/hardware/V1_revB/2_chassis/CAD/chassis-F_Mask.pdf

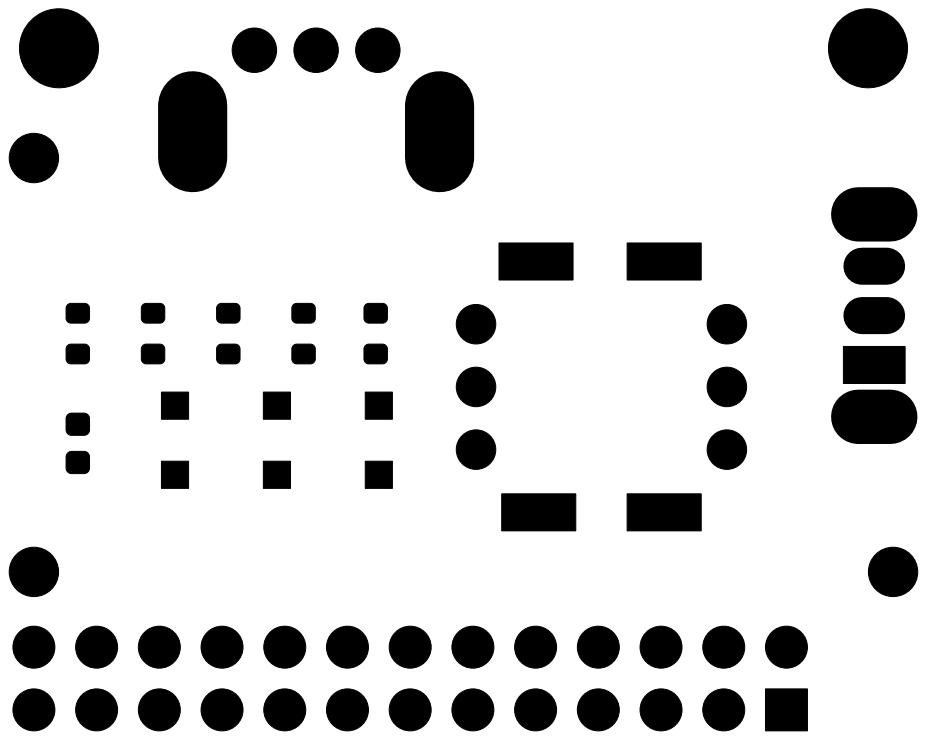
[picture p208: page 1]
