ToyotaInfoTech/RAMN/hardware/V1_revB/2_chassis/CAD/chassis-F_Paste.pdf

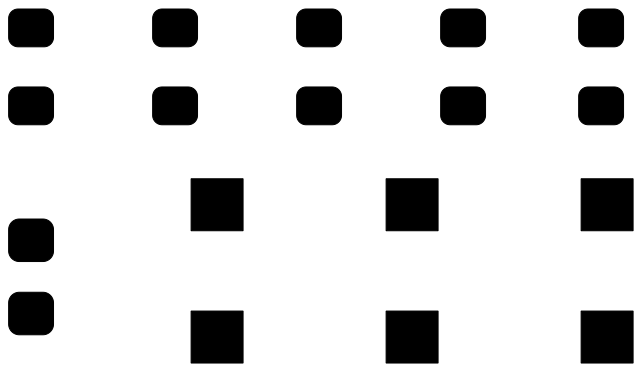
[picture p209: page 1]
