ToyotaInfoTech/RAMN/hardware/V1_revB/2_chassis/CAD/chassis-F_SilkS.pdf

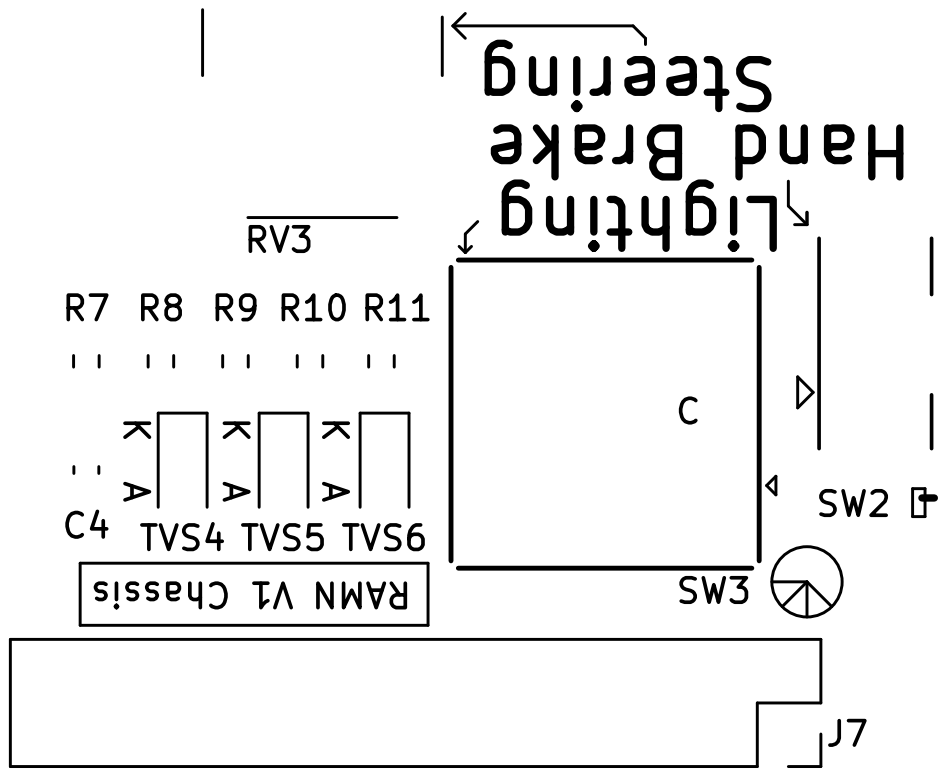
[picture p210: page 1]
