ToyotaInfoTech/RAMN/hardware/V1_revB/1_screens/CAD/screens-B_Cu.pdf

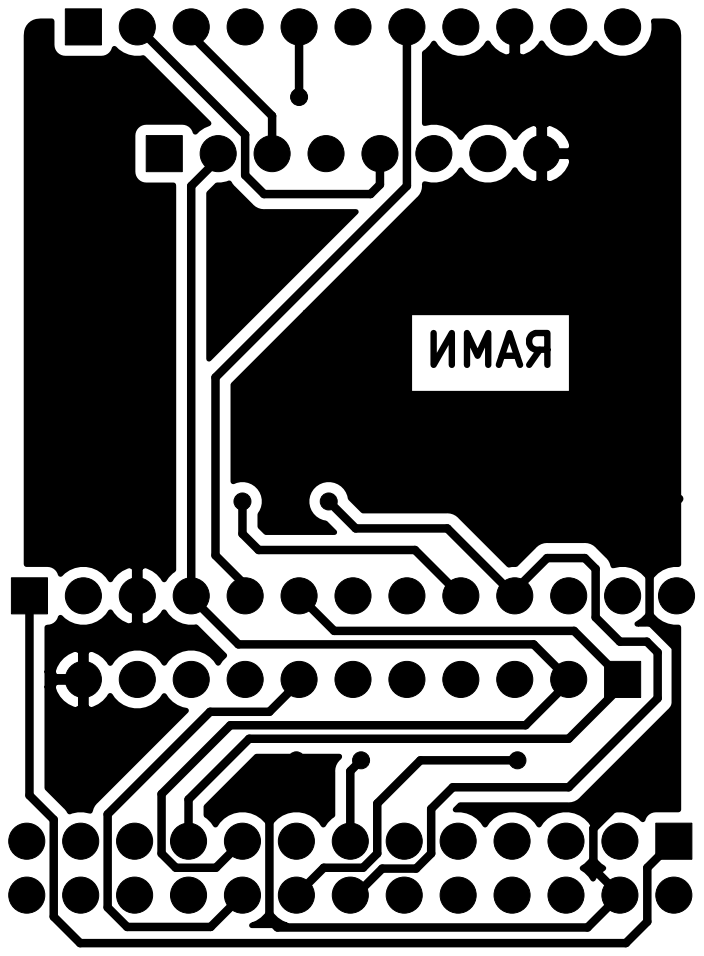
[picture p211: page 1]
