ToyotaInfoTech/RAMN/hardware/V1_revB/1_screens/CAD/screens-B_Mask.pdf

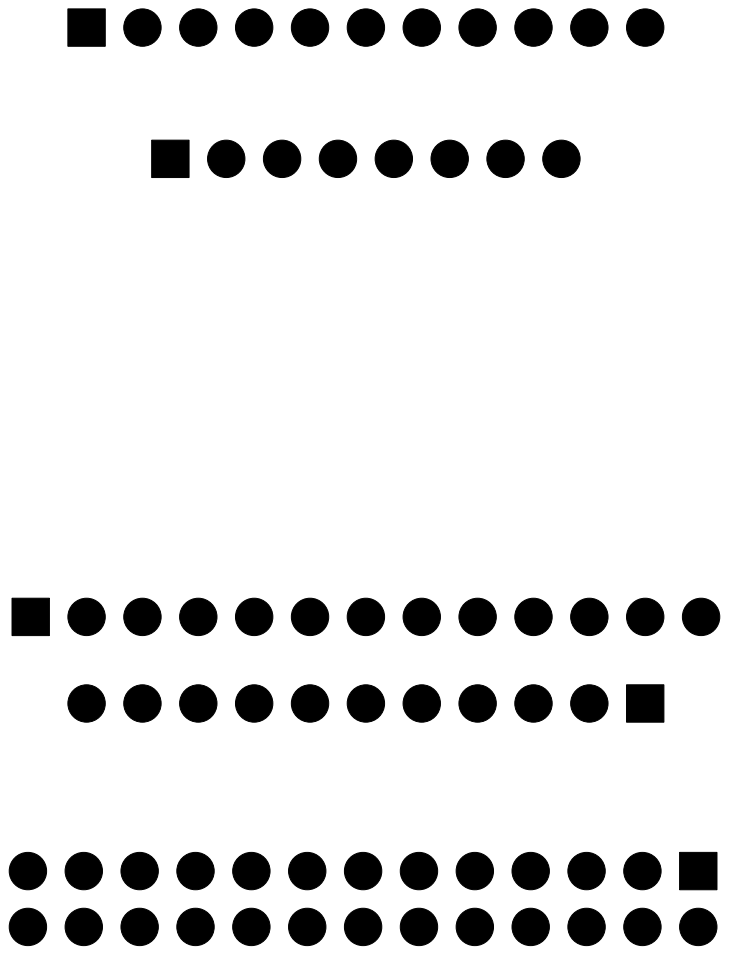
[picture p212: page 1]
