ToyotaInfoTech/RAMN/hardware/V1_revB/1_screens/CAD/screens-Edge_Cuts.pdf

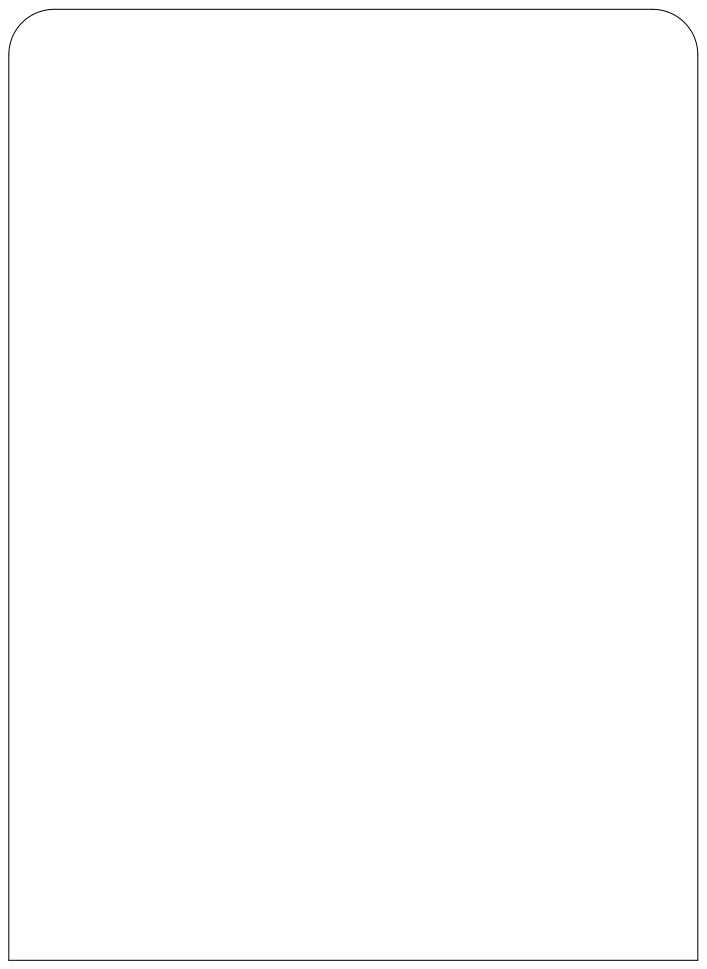
[picture p213: page 1]
