ToyotaInfoTech/RAMN/hardware/V1_revB/1_screens/CAD/screens-F_Cu.pdf

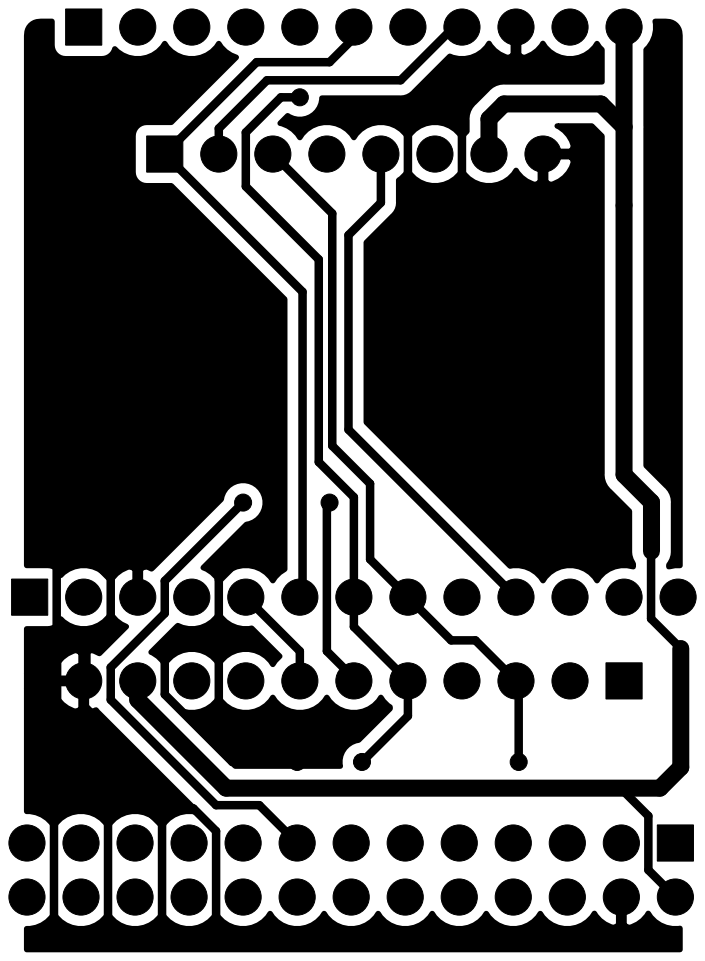
[picture p214: page 1]
