ToyotaInfoTech/RAMN/hardware/V1_revB/4_body/CAD/body-B_Cu.pdf

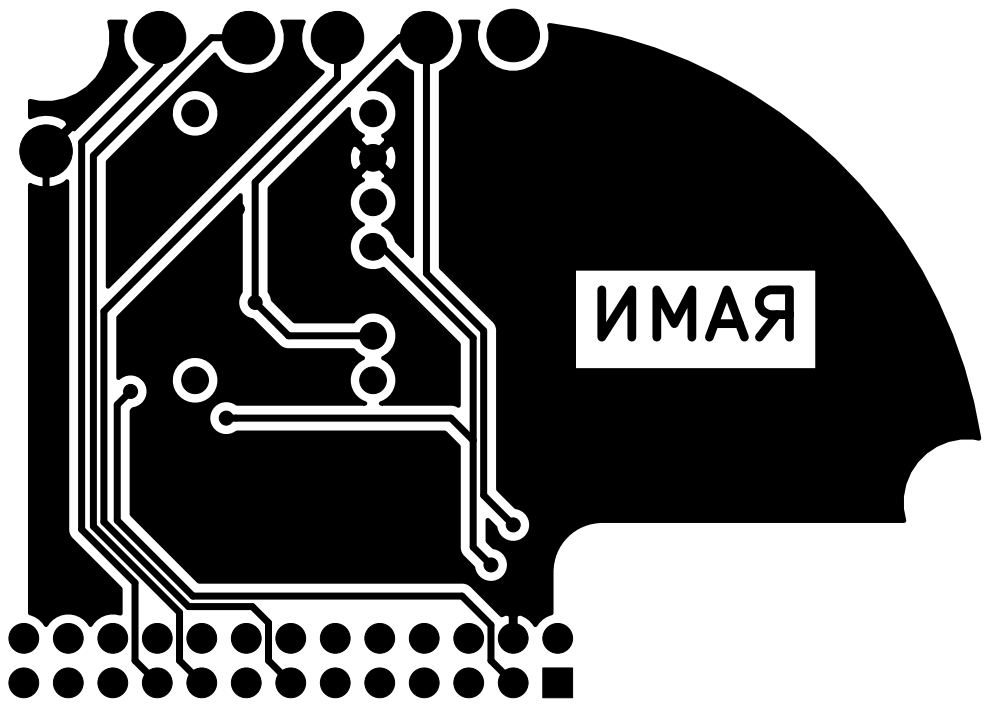
[picture p215: page 1]
