ToyotaInfoTech/RAMN/hardware/V1_revB/4_body/CAD/body-B_Mask.pdf

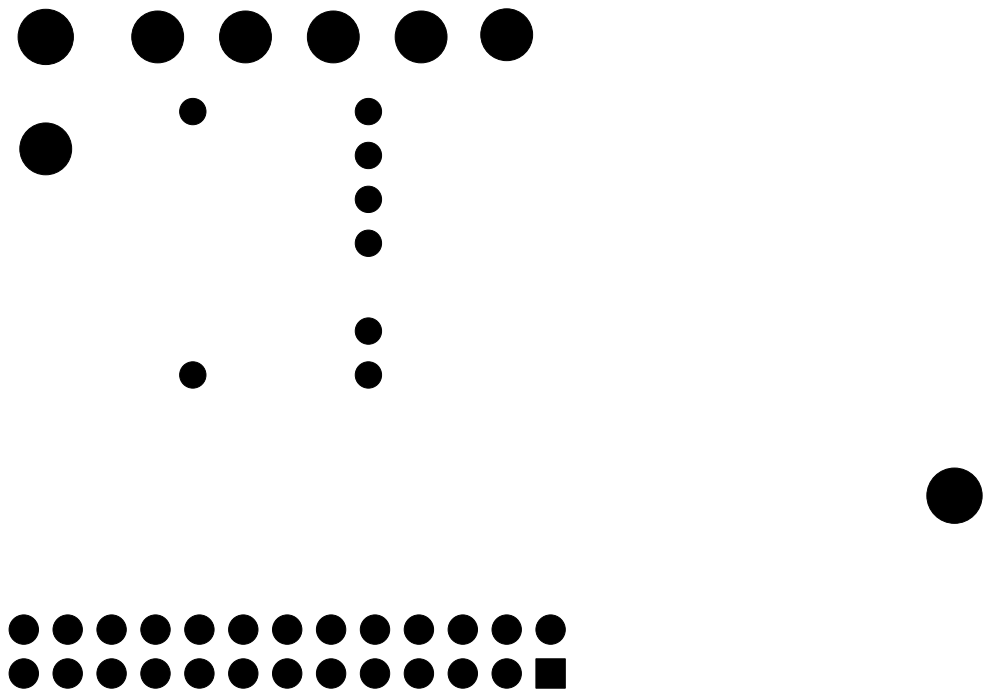
[picture p216: page 1]
