ToyotaInfoTech/RAMN/hardware/V1_revB/4_body/CAD/body-Edge_Cuts.pdf

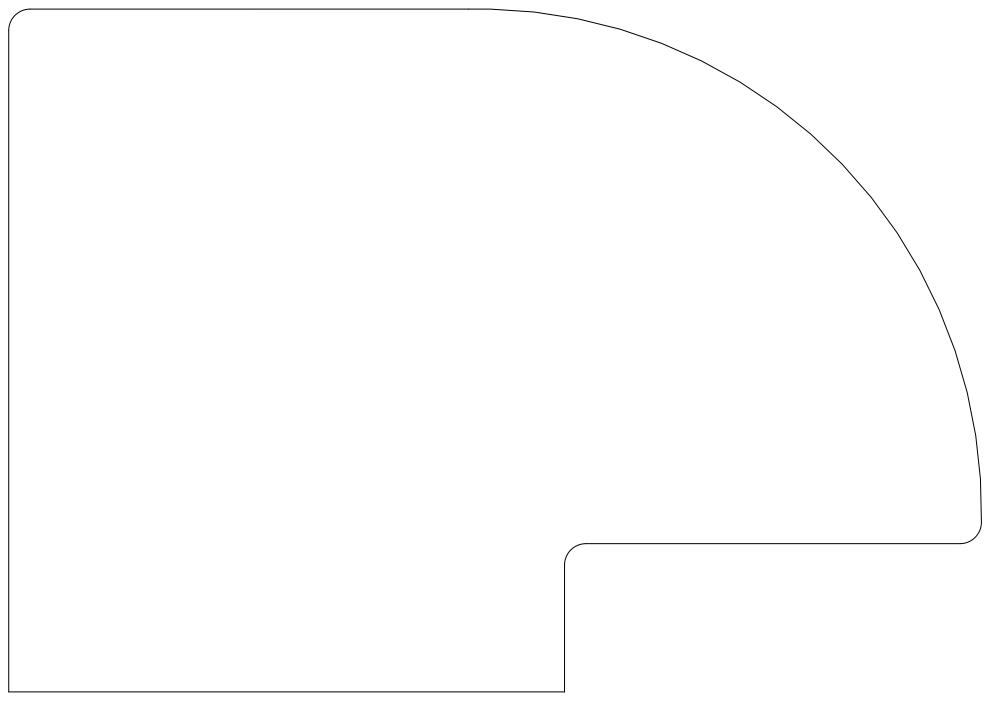
[picture p217: page 1]
