ToyotaInfoTech/RAMN/hardware/V1_revB/4_body/CAD/body-F_Cu.pdf

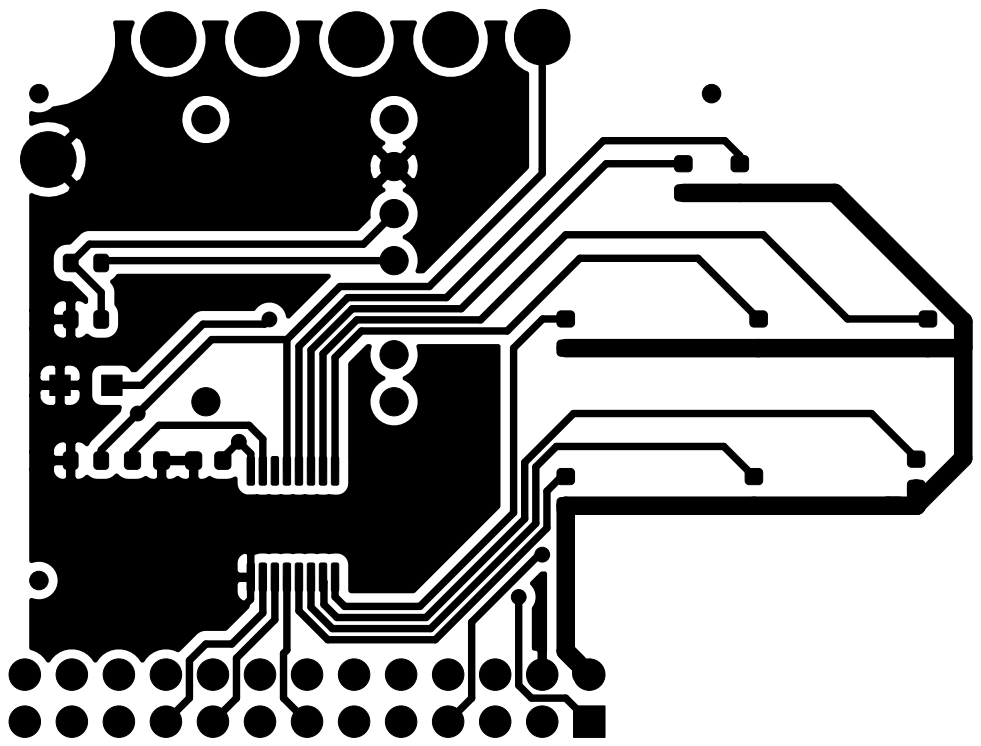
[picture p218: page 1]
