ToyotaInfoTech/RAMN/hardware/V1_revB/4_body/CAD/body-F_Mask.pdf

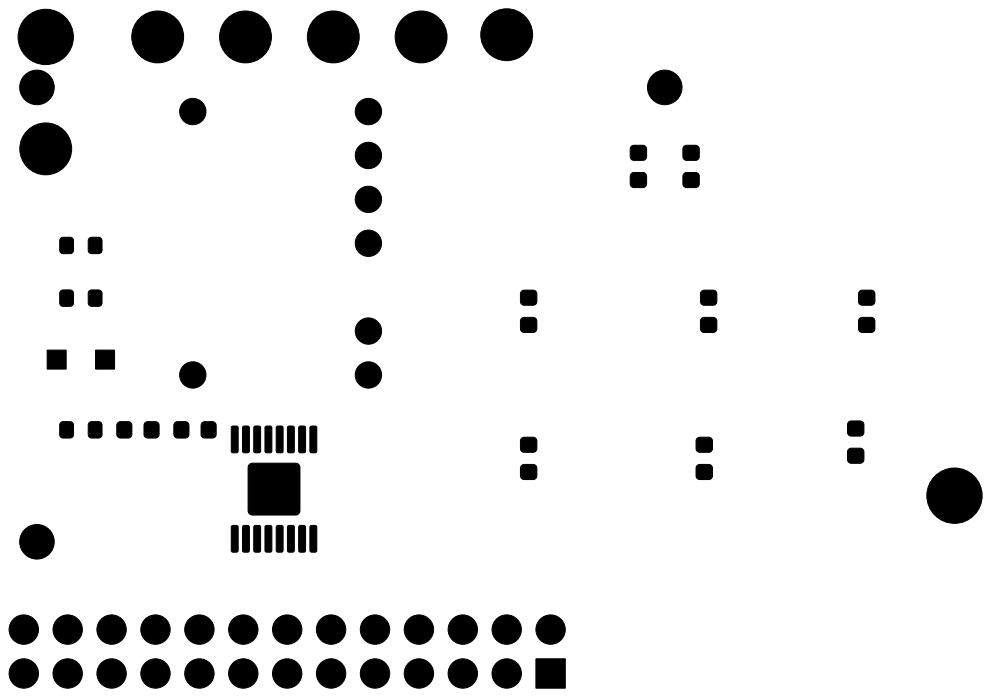
[picture p219: page 1]
