ToyotaInfoTech/RAMN/hardware/V1_revB/4_body/CAD/body-F_Paste.pdf

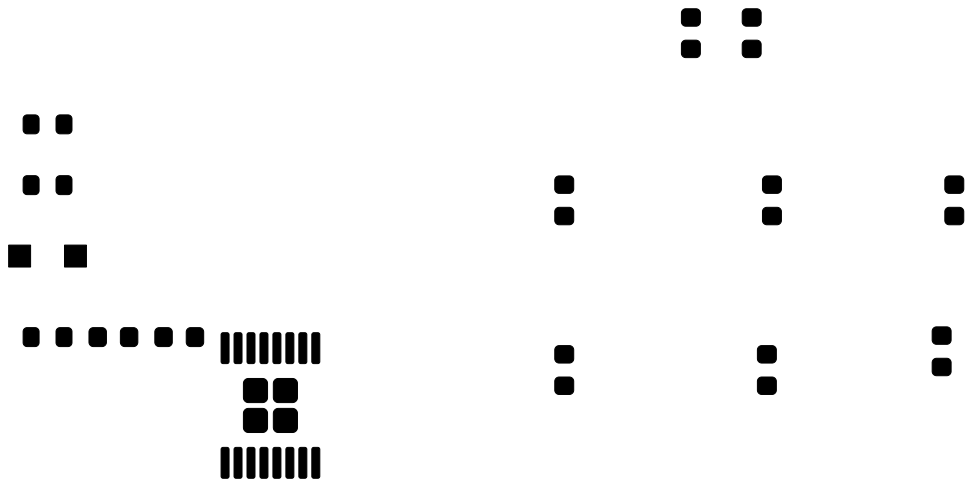
[picture p220: page 1]
