ToyotaInfoTech/RAMN/firmware/RAMNV1/Core/Src/ramn_sensors.c

/*
 * ramn_sensors.c
 ******************************************************************************
 * @attention
 *
 * <h2><center>&copy; Copyright (c) 2025 TOYOTA MOTOR CORPORATION.
 * ALL RIGHTS RESERVED.</center></h2>
 *
 * This software component is licensed by TOYOTA MOTOR CORPORATION under BSD 3-Clause license,
 * the "License"; You may not use this file except in compliance with the
 * License. You may obtain a copy of the License at:
 *                        opensource.org/licenses/BSD-3-Clause
 *
 ******************************************************************************
 */

#include "ramn_sensors.h"

// Public --------------------------------------------

// Array directly accessed by DMA
#ifdef ENABLE_ADC
uint16_t RAMN_SENSORS_ADCValues[NUMBER_OF_ADC] = {0,0,0};
#endif

// Private --------------------------------------------

// Variable to keep the tick of the last update.
static uint32_t lastUpdateTick; //TODO: remove and replace by better debounce

#if defined(EXPANSION_CHASSIS)

// Look up table to convert logarithmic potentiometer to linear potentiometer
// By default not applied to BRAKE and ACCEL, to mimic real pedals.
#if defined(CHASSIS_LOGARITHMIC_POTENTIOMETER)
static const uint16_t loglookupt[] = {
		0xfff, 0xfff, 0xfff, 0xfff, 0xfff, 0xfff, 0xfff, 0xfff, 0xfff, 0xfff, 0xfff, 0xfff, 0xfff, 0xfff, 0xfff, 0xfff, 0xfff, 0xfff, 0xfff, 0xfff, 0xfff, 0xfff, 0xfff, 0xfff, 0xfff, 0xfff, 0xfff, 0xfff, 0xfff, 0xfff, 0xfff, 0xfff, 0xfff, 0xfff, 0xfff, 0xfff, 0xfff, 0xfff, 0xfff, 0xfff, 0xfff, 0xfff, 0xfff, 0xfff, 0xfff, 0xfff, 0xfff, 0xfff, 0xfff, 0xfff, 0xfff, 0xfff, 0xfff, 0xfff, 0xfff, 0xfff, 0xfff, 0xfff, 0xfff, 0xfff, 0xfff, 0xffe, 0xffe, 0xffe, 0xffd, 0xffd, 0xffd, 0xffc, 0xffc, 0xffc, 0xffb, 0xffb, 0xffb, 0xffa, 0xffa, 0xff9, 0xff9, 0xff9, 0xff8, 0xff8, 0xff8, 0xff7, 0xff7, 0xff7, 0xff6, 0xff6, 0xff6, 0xff5, 0xff5, 0xff5, 0xff4, 0xff4, 0xff4, 0xff3, 0xff3, 0xff3, 0xff2, 0xff2, 0xff2, 0xff1, 0xff1, 0xff1, 0xff0, 0xff0, 0xff0, 0xfef, 0xfef, 0xfee, 0xfee, 0xfee, 0xfed, 0xfed, 0xfed, 0xfec, 0xfec, 0xfec, 0xfeb, 0xfeb, 0xfeb, 0xfea, 0xfea, 0xfea, 0xfe9, 0xfe9, 0xfe9, 0xfe8, 0xfe8, 0xfe8, 0xfe7, 0xfe7, 0xfe7, 0xfe6, 0xfe6, 0xfe6, 0xfe5, 0xfe5, 0xfe4, 0xfe4, 0xfe4, 0xfe3, 0xfe3, 0xfe3, 0xfe2, 0xfe2, 0xfe2, 0xfe1, 0xfe1, 0xfe1, 0xfe0, 0xfe0, 0xfe0, 0xfdf, 0xfdf, 0xfdf, 0xfde, 0xfde, 0xfde, 0xfdd, 0xfdd, 0xfdc, 0xfdc, 0xfdc, 0xfdb, 0xfdb, 0xfdb, 0xfda, 0xfda, 0xfda, 0xfd9, 0xfd9, 0xfd9, 0xfd8, 0xfd8, 0xfd8, 0xfd7, 0xfd7, 0xfd7, 0xfd6, 0xfd6, 0xfd5, 0xfd5, 0xfd5, 0xfd4, 0xfd4, 0xfd4, 0xfd3, 0xfd3, 0xfd3, 0xfd2, 0xfd2, 0xfd2, 0xfd1, 0xfd1, 0xfd1, 0xfd0, 0xfd0, 0xfcf, 0xfcf, 0xfcf, 0xfce, 0xfce, 0xfce, 0xfcd, 0xfcd, 0xfcd, 0xfcc, 0xfcc, 0xfcc, 0xfcb, 0xfcb, 0xfcb, 0xfca, 0xfca, 0xfc9, 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

static uint16_t SENSORS_ScaleADC(uint16_t raw, uint16_t min, uint16_t max)
{
	if (raw <= min) return 0x000;
	if (raw >= max) return 0xFFF;
	return (uint16_t)(((uint32_t)(raw - min) * 0xFFF) / (max - min));
}

#if defined(EXPANSION_POWERTRAIN)

static RAMN_LeverState_t SENSORS_ConvertLeverADC(uint16_t adcval)
{
	RAMN_LeverState_t         result = RAMN_SHIFT_UNKNOWNSTATE;
	if      (adcval >= 0x0D00)  result = RAMN_SHIFT_RELEASED;
	else if (adcval >= 0x0C00)  result = RAMN_SHIFT_DOWN;
	else if (adcval >= 0x0B00)  result = RAMN_SHIFT_RIGHT;
	else if (adcval >= 0x0A00)  result = RAMN_SHIFT_LEFT;
	else if (adcval >= 0x0700)  result = RAMN_SHIFT_PUSH;
	else if (adcval <= 0x0100)  result = RAMN_SHIFT_UP;
	return result;
}

static void SENSORS_UpdatePowertrain(uint32_t tick)
{
	RAMN_SENSORS_POWERTRAIN.brakePotentiometer = SENSORS_ScaleADC(RAMN_SENSORS_ADCValues[0], SENSORS_BRAKE_MIN, SENSORS_BRAKE_MAX);
	RAMN_SENSORS_POWERTRAIN.accelPotentiometer = SENSORS_ScaleADC(RAMN_SENSORS_ADCValues[1], SENSORS_ACCEL_MIN, SENSORS_ACCEL_MAX);
	RAMN_SENSORS_POWERTRAIN.shiftJoystick = SENSORS_ConvertLeverADC(RAMN_SENSORS_ADCValues[2]);

	if (tick - lastUpdateTick > 100U) //TODO: replace this by better debounce
	{
		lastUpdateTick = tick;
		if((RAMN_SENSORS_POWERTRAIN.shiftJoystick != RAMN_SHIFT_RELEASED) && (RAMN_SENSORS_POWERTRAIN_PREVIOUS.shiftJoystick == RAMN_SHIFT_RELEASED))
		{
			if (RAMN_SENSORS_POWERTRAIN.shiftJoystick == RAMN_SHIFT_UP)
			{
				RAMN_SENSORS_POWERTRAIN.gear = ((RAMN_SENSORS_POWERTRAIN.gear < MAX_GEAR_VALUE) || (RAMN_SENSORS_POWERTRAIN.gear == 0xFF)) ? (((uint8_t)RAMN_SENSORS_POWERTRAIN.gear)+1)&0xFF : RAMN_SENSORS_POWERTRAIN.gear;
			}
			if (RAMN_SENSORS_POWERTRAIN.shiftJoystick == RAMN_SHIFT_DOWN)
			{
				RAMN_SENSORS_POWERTRAIN.gear = (RAMN_SENSORS_POWERTRAIN.gear <= MAX_GEAR_VALUE) ? (((uint8_t)RAMN_SENSORS_POWERTRAIN.gear)-1)&0xFF : RAMN_SENSORS_POWERTRAIN.gear;
			}
			if (RAMN_SENSORS_POWERTRAIN.shiftJoystick == RAMN_SHIFT_RIGHT)  RAMN_SENSORS_POWERTRAIN.turnIndicatorRequest = (RAMN_SENSORS_POWERTRAIN.turnIndicatorRequest ^ 0x1)&0xFF;
			if (RAMN_SENSORS_POWERTRAIN.shiftJoystick == RAMN_SHIFT_LEFT)   RAMN_SENSORS_POWERTRAIN.turnIndicatorRequest = (RAMN_SENSORS_POWERTRAIN.turnIndicatorRequest ^ 0x100)&0xFF00;
		}
		RAMN_SENSORS_POWERTRAIN_PREVIOUS = RAMN_SENSORS_POWERTRAIN;
	}

	if (RAMN_SENSORS_POWERTRAIN.shiftJoystick == RAMN_SHIFT_PUSH) RAMN_SENSORS_POWERTRAIN.hornRequest = True;
	else RAMN_SENSORS_POWERTRAIN.hornRequest = False;
}

#endif

#if defined(EXPANSION_CHASSIS)

static RAMN_LightSwitchState_t SENSORS_ConvertLightSwitchADC(uint16_t adcval)
{
	RAMN_LeverState_t         result = RAMN_LIGHTSWITCH_UNKNOWNSTATE;
	if      (adcval >= 0x0B00)  result = RAMN_LIGHTSWITCH_POS1;
	else if (adcval >= 0x0700)  result = RAMN_LIGHTSWITCH_POS2;
	else if (adcval >= 0x0300)  result = RAMN_LIGHTSWITCH_POS3;
	else if (adcval <= 0x0100)  result = RAMN_LIGHTSWITCH_POS4;
	return result;
}

static RAMN_SideBrakeState_t SENSORS_ConvertSideBrakeADC(uint16_t adcval)
{
	if (adcval < 0x700) return RAMN_SIDEBRAKE_DOWN;
	else return RAMN_SIDEBRAKE_UP;
}

#if defined(CHASSIS_LOGARITHMIC_POTENTIOMETER)
static uint16_t SENSORS_LogToLinear(uint16_t val ) {
	return loglookupt[val];
}
#endif

static void SENSORS_UpdateChassis(uint32_t tick)
{
	RAMN_LightSwitchState_t currentLightSwitch;
#ifdef CHASSIS_LOGARITHMIC_POTENTIOMETER
	RAMN_SENSORS_CHASSIS.steeringPotentiometer = SENSORS_LogToLinear(RAMN_SENSORS_ADCValues[0]);
#else
	RAMN_SENSORS_CHASSIS.steeringPotentiometer = (0xFFF - SENSORS_ScaleADC(RAMN_SENSORS_ADCValues[0], SENSORS_STEER_LINEAR_MIN, SENSORS_STEER_LINEAR_MAX));
#endif
	RAMN_SENSORS_CHASSIS.sidebrakeSwitch = SENSORS_ConvertSideBrakeADC(RAMN_SENSORS_ADCValues[1]);

	currentLightSwitch = SENSORS_ConvertLightSwitchADC(RAMN_SENSORS_ADCValues[2]);

	if (currentLightSwitch != RAMN_SENSORS_CHASSIS.lightsSwitch)
	{
		if (tick - lastUpdateTick > 250U) //TODO: replace this by better switch debounce
		{
			lastUpdateTick = tick;
			RAMN_SENSORS_CHASSIS.lightsSwitch = currentLightSwitch;
		}
	}
	else
	{
		lastUpdateTick = tick;
		RAMN_SENSORS_CHASSIS.lightsSwitch = currentLightSwitch;
	}
}

#endif


#if defined(EXPANSION_BODY)

static RAMN_EngineKeyState_t SENSORS_ConvertEngineKeyADC(uint16_t adcval)
{
	if (adcval <= 0x300) return RAMN_ENGINEKEY_LEFT;
	else if (adcval <= 0xA00) return RAMN_ENGINEKEY_MIDDLE;
	else return RAMN_ENGINEKEY_RIGHT;
}

static void updateBody(uint32_t tick)
{
	RAMN_SENSORS_BODY.engineKey =SENSORS_ConvertEngineKeyADC(RAMN_SENSORS_ADCValues[1]);
}

#endif


//Exported --------------------------------------------

void RAMN_SENSORS_Init(void)
{
	lastUpdateTick = 0U;
}

void RAMN_SENSORS_Update(uint32_t tick)
{

#if defined(EXPANSION_POWERTRAIN)
	SENSORS_UpdatePowertrain(tick);
#endif

#if defined(EXPANSION_CHASSIS)
	SENSORS_UpdateChassis(tick);
#endif

#if defined(EXPANSION_BODY)
	RAMN_SENSORS_BODY_PREVIOUS = RAMN_SENSORS_BODY;
	updateBody(tick);
#endif

}
