ToyotaInfoTech/RAMN/firmware/RAMNV1/Core/Inc/ramn_config.h

/*
 * ramn_config.h
 ******************************************************************************
 * @attention
 *
 * <h2><center>&copy; Copyright (c) 2025 TOYOTA MOTOR CORPORATION.
 * ALL RIGHTS RESERVED.</center></h2>
 *
 * This software component is licensed by TOYOTA MOTOR CORPORATION under BSD 3-Clause license,
 * the "License"; You may not use this file except in compliance with the
 * License. You may obtain a copy of the License at:
 *                        opensource.org/licenses/BSD-3-Clause
 *
 ******************************************************************************
 */

// This module holds the configuration of current build.

#ifndef INC_RAMN_CONFIG_H_
#define INC_RAMN_CONFIG_H_

#if !defined(TARGET_ECUA) && !defined(TARGET_ECUB) && !defined(TARGET_ECUC) && !defined(TARGET_ECUD)
// Define which ECU the source code should be built for.
// You need to specify which ECU you are trying to debug here.
// This define is only used for debugging - the build scripts in scripts/build will override this define.
#define TARGET_ECUA
//#define TARGET_ECUB
//#define TARGET_ECUC
//#define TARGET_ECUD
#endif

// See comments at the end of file if you want to use the internal oscillator instead of the external crystal.

// Enable the flag below if you want to disable features that may impact security (e.g., ReadMemoryByAddress UDS service, etc.).
// This can be used to put RAMN in a state ready to be customized for Capture The Flag applications.
// By default, this will generate compile errors that you will need to address by removing relevant defines or commenting out the #error lines.
// Note that the USB CLI will be active but not accessible unless you make the "#" command available again (by editing ramn_cdc.c).
// UDS over USB (slcan command "%" is accessible by default, but you may want to remove it (also by editing ramn_cdc.c) to further limit attack surfaces.
//#define HARDENING

// CONFIGURATION OF ECU A ------------------------------------------------------

#if defined(TARGET_ECUA)
//#define ENABLE_ADC
#define ENABLE_USB
#define ENABLE_CDC // USB serial (CDC) interface

// Enable this flag to enable the candlelight interface (gs_usb drivers)
// Current implementation is experimental:
// - Error frames are not reported
// - CAN-FD is not supported
// - Due to clock differences, bit timings are not respected (but equivalent baudrates are used)
// Try increasing _Min_Stack_Size if you run into issues
//#define ENABLE_GSUSB

#ifndef ENABLE_GSUSB
#define USBD_VID                        0x483
#define USBD_PID                        0x5740
#else
// IDs below automatically load the drivers on Linux and are required for userspace python-can drivers
#define USBD_VID                        0x1d50
#define USBD_PID                        0x606f
#endif

#define USBD_LANGID_STRING            	1033
#define USBD_MANUFACTURER_STRING      	"Toyota Motor Corporation"
#define USBD_PRODUCT_STRING           	"RAMN Composite Device"
#define USBD_CONFIGURATION_STRING     	"MDC Config"
#define USBD_INTERFACE_STRING         	"MDC Interface"

// Enable SPI (for screen control)
#define ENABLE_SPI

// Enable screen (not restricted to ECU A).
#define ENABLE_SCREEN

// Enable Chip 8 engine.
#define ENABLE_CHIP8

// Enable USB MiniCTF challenges.
#define ENABLE_MINICTF

// Note that UDS programming does not work on microcontrollers with only 256 kb memory (e.g., reference ending with CCT6).
#define ENABLE_UDS_REPROGRAMMING
#define ENABLE_UDS
#define ENABLE_J1979
//#define ENABLE_KWP
//#define ENABLE_XCP
#define RTR_DEMO_ID 0x700

// ECU will monitor joystick CAN messages and generate events such as PRESSED and RELEASED.
// You must independently make sure that the ECU does not filter out the relevant CAN messages (which it shouldn't by default).
#define ENABLE_JOYSTICK_CONTROLS

// Use this to define a "password" for the command to put ECU A back into DFU mode.
// Note that this is not for security (because STM32 can be put back into DFU mode over JTAG, and if JTAG is permanently disabled (level 2) the back-to-DFU command won't work correctly anyway).
// This is only to prevent users from accidentally putting the ECU back into DFU mode (e.g. because of fuzzing).
#define DFU_COMMAND_STRING "zZ"

// Automatically close the serial port if it overflows (consider that the user forgot to close it).
#define CLOSE_DEVICE_ON_USB_TX_OVERFLOW

// Automatically stops transmitting when serial port close is detected.
// May not work well with some OS/Applications
// #define ENABLE_USB_AUTODETECT

// Will start the usb serial interface in CLI mode instead of slcan if enabled.
// If used with HARDENING, make sure you make the "#" slcan command available again.
//#define START_IN_CLI_MODE

// Define this flag to let ECU A process slcan message that it receives as regular RX messages (and update their value on screen, for example).
// This is useful to demonstrate the impact of CAN fuzzing on ECU A's screen when using ECU A's slcan interface, even though ECU A did not actually receive the fuzzed CAN message (since it was the transmitter).
#define PROCESS_SLCAN_BY_DBC

// Define this flag to enable the USB debugging module.
// Note that it also needs to be activated by a slcan command, or by setting RAMN_DEBUG_ENABLE in ramn_debug.c to True.
#define ENABLE_USB_DEBUG

// Number of times to retry entering bootloader mode of another ECU before giving up
#define BOOTLOADER_MAX_ATTEMPTS 20

// Enable this define to prevent ECU A from overwriting its option bytes to force application mode.
// This is in case you want to control the boot mode of ECU A using the BOOT0 pin (in hardware).
// When this flag is enabled, ECU A will boot in DFU mode if BOOT0 is high (default), and in application mode if BOOT0 is low.
//#define HARDWARE_BOOT0_CONTROL


#ifdef ENABLE_GSUSB
#define GSUSB_RECV_QUEUE_SIZE 	512 // Size of the GSUSB receive queue (uint32_t elements)
#define GSUSB_POOL_QUEUE_SIZE 	512 // Size of the GSUSB pool queue (uint32_t elements)
#define GSUSB_SEND_QUEUE_SIZE 	512 // Size of the GSUSB send queue (uint32_t elements)
#define GS_HOST_FRAME_SIZE     	80
#define CAN_QUEUE_SIZE			512
#endif

#define ENABLE_BITBANG

#endif

// CONFIGURATION OF ECU B ------------------------------------------------------

#if defined(TARGET_ECUB)
//#define ENABLE_SCREEN
#define ENABLE_ADC
#define EXPANSION_CHASSIS

// Define flag below to indicate that the steering wheel potentiometer is of the logarithmic type.
//#define CHASSIS_LOGARITHMIC_POTENTIOMETER
#if !defined(CHASSIS_LOGARITHMIC_POTENTIOMETER) && !defined(CHASSIS_LINEAR_POTENTIOMETER)
// If CHASSIS_LINEAR_POTENTIOMETER not defined by build script, consider Log as default
#define CHASSIS_LOGARITHMIC_POTENTIOMETER
#endif

#define ENABLE_UDS_REPROGRAMMING
#define ENABLE_UDS
#define ENABLE_J1979
//#define ENABLE_KWP
#define ENABLE_XCP
#define RTR_DEMO_ID 0x701
#endif

// CONFIGURATION OF ECU C ------------------------------------------------------

#if defined(TARGET_ECUC)
//#define ENABLE_SCREEN
#define ENABLE_ADC
#define EXPANSION_POWERTRAIN
#define ENABLE_UDS_REPROGRAMMING
#define ENABLE_UDS
#define ENABLE_J1979
//#define ENABLE_KWP
#define ENABLE_XCP
#define RTR_DEMO_ID 0x702
#endif


// CONFIGURATION OF ECU D ------------------------------------------------------

#if defined(TARGET_ECUD)
#define ENABLE_MINICTF
#define ENABLE_ADC
#define EXPANSION_BODY

// Enable SPI (for LED control)
#define ENABLE_SPI

#define ENABLE_UDS_REPROGRAMMING
#define ENABLE_UDS
#define ENABLE_J1979
//#define ENABLE_KWP
#define ENABLE_XCP
#define RTR_DEMO_ID 0x703

// How long to light up ECU D's LEDs at startup. Set to 0 to skip test.
#define LED_TEST_DURATION_MS 3000U
#endif

// Common configuration ------------------------------------------------------

// Enable this flag to activate Showcase Mode.
// When enabled, ECU A will periodically randomize command values at 1 Hz
// and other ECUs will follow those commands received via CAN, INSTEAD OF their
// sensor inputs. This relies on the CARLA driving commands but
// without requiring UDS activation or physical sensor inputs.
// #define RAMN_SHOWCASE_MODE

// Loop time for the "simulator" that is executed periodically.
#define SIM_LOOP_CLOCK_MS 10

// Enable watchdogs - Application needs to kick it every 1s.
//#define WATCHDOG_ENABLE

// Will make ECU accept broadcasted UDS commands.
// CAN ID must be defined in ramn_vehicle_specific.h.
#define UDS_ACCEPT_FUNCTIONAL_ADDRESSING

// Enable dynamic computations of tseg1 and tseg2 to get non-standard baudrate.
// If you change the clock of the FDCAN peripheral, you'll need to update this too.
// /!\CURRENTLY UNTESTED
#define ENABLE_DYNAMIC_BITRATE
#define FDCAN_PERIPHERAL_CLOCK 40000000

// Enable this flag to enable FreeRTOS runtime stats.
// This also requires to add "volatile" keyword to static uint32_t ulTotalRunTime = 0UL in tasks.c of FreeRTOS (typically overwritten by STM32CubeIDE code generation).
// Increase the frequency of runtime timer (by default, TIM7) to increase stat accuracy at the cost of performances.
#define GENERATE_RUNTIME_STATS
#define MAX_NUMBER_OF_TASKS 16 // Max number of tasks that can be monitored, if enabled
// If this flag is enabled, ECU A will repeat whatever message it accepts over USB.
// May be useful when multiplexing the serial interface, but should typically not be used.
// CAN_ECHO does not cover ECU A CAN messages not sent from USB (i.e., answer to UDS commands).
//#define CAN_ECHO

// This flag can be used to automatically reset CAN/CAN-FD peripheral if it enters bus-off mode.
// #define AUTO_RECOVER_BUSOFF

// Use big endian for CAN brake/steering/accelerator sensors instead of ARM Little Endian.
#define USE_BIG_ENDIAN_CAN

#ifndef TARGET_ECUA
// Use Hardware CAN filters (Up to 28 standard IDs, 8 extended IDs).
// If this is enabled, you need to update ECU RX filters when you want to add CAN IDs to the network.
#define USE_HARDWARE_CAN_FILTERS
#endif

// Enable these flags to display a warning if the periodic task is taking longer than the defined period.
// #define DISPLAY_SLOW_WARNING

// If the flag above is defined, you can decide to skip the first cycles, which are expected to take longer due to initializations.
#define SLOW_WARNING_MIN_LOOP_COUNT 1U

// Enable the I2C interface
// /!\CURRENTLY UNTESTED
// #define ENABLE_I2C

// Enable the UART interface
// /!\ CURRENTLY UNTESTED
// #define ENABLE_UART

// Enable this flag to force code to while(1) when encountering errors that could typically be ignored.
//#define HANG_ON_ERRORS

// Enable this flag to automatically enable memory protection at startup. Once activated, it can only be removed by bootloader/usb commands.
// Avoid using if you are not sure what you are doing.
// #define MEMORY_AUTOLOCK

// Selects the CAN signal definitions traffic profile active at power-on
// TRAFFIC_MODE_DEFAULT: Default RAMN traffic with freshness counters and CRC32
// TRAFFIC_MODE_J1939  : J1939signals

// Both profiles are always compiled in; this value only selects the boot profile. The active
// profile can also be switched live at runtime (see the "trafficmode" USB CLI command).
#define TRAFFIC_MODE_DEFAULT 0
#define TRAFFIC_MODE_J1939   1

#ifndef DEFAULT_TRAFFIC_MODE
#define DEFAULT_TRAFFIC_MODE TRAFFIC_MODE_DEFAULT
#endif


// Value to set to the RDP option byte if flag above is active.
// It is 0xAA when unlocked (OB_RDP_LEVEL_0), 0xBB if temporarily locked by bootloader (OB_RDP_LEVEL_1, or 0xDC if locked by STM32CubeProgrammer).
// Setting this value to 0xCC (OB_RDP_LEVEL_2) will PERMANENTLY LOCK JTAG (the ECU will not be reprogrammable anymore)
#define RDP_OPTIONBYTE OB_RDP_LEVEL_1

// If this is defined, the TRNG module will fill a stream buffer with random bytes instead of calling the HAL library.
//#define USE_TRNG_BUFFER

// TRNG pool settings (if used)
#define TRNG_POOL_SIZE 	   				256
#define JOYSTICK_POOL_SIZE				10

#ifdef ENABLE_I2C
#define I2C_RX_BUFFER_SIZE				(16)
#define I2C_TX_BUFFER_SIZE				(4)
#endif

#ifdef ENABLE_UART

// UART module works by queuing commands in a stream buffer.
// You should define the size of working buffers (for currently processed command/answers) and of stream buffers (where all commands/queued are queued and waiting for transmission).

// Working buffer
#define UART_RX_COMMAND_BUFFER_SIZE			128 //This is the maximum length of a command to receive, used by both TASK and ISR
#define UART_TX_COMMAND_BUFFER_SIZE			128 //This is the maximum length of a command to send back

// Stream buffer
#define UART_RX_BUFFER_SIZE 				512
#define UART_TX_BUFFER_SIZE 				512

#if (UART_RX_COMMAND_BUFFER_SIZE > UART_RX_BUFFER_SIZE) || (UART_TX_COMMAND_BUFFER_SIZE > UART_TX_BUFFER_SIZE)
#error command size should be smaller than stream buffer size
#endif

#endif


#if defined(ENABLE_UDS) || defined(ENABLE_KWP) || defined(ENABLE_XCP)
#define ENABLE_DIAG
#define ENABLE_EEPROM_EMULATION
#if defined(ENABLE_SCREEN)
// Size of the buffer used to draw on screen using UDS commands
#define UDS_DRAW_BUFFER_SIZE 0x1000
#endif
#endif

#if defined(ENABLE_UDS) || defined(ENABLE_KWP)
#ifndef ENABLE_ISOTP
#define ENABLE_ISOTP
#endif
#endif

#define ISOTP_RXBUFFER_SIZE 			4224
#define ISOTP_TXBUFFER_SIZE 			4224
#define ISOTP_CONSECUTIVE_BLOCK_SIZE 	0
#define ISOTP_CONSECUTIVE_ST 			0

// Maximum CAN frame payload (CAN_DL) used when transmitting ISO-TP frames.
// This is only used when you send an ISO-TP request with CAN-FD - if you use classic CAN, the ECU will answer with classic CAN (max payload 8).
// Note that the CAN-FD version is still experimental
#define ISOTP_TX_DL 					64
#if (ISOTP_TX_DL != 8) && (ISOTP_TX_DL != 12) && (ISOTP_TX_DL != 16) && (ISOTP_TX_DL != 20) && (ISOTP_TX_DL != 24) && (ISOTP_TX_DL != 32) && (ISOTP_TX_DL != 48) && (ISOTP_TX_DL != 64)
#error "ISOTP_TX_DL must be a valid CAN_DL (8, 12, 16, 20, 24, 32, 48 or 64)"
#endif

// ISO-TP Timeout values. Set to a large value intentionally to prevent timeouts during manual experimentation.
// Set both to 1000 to better mimic real ECUs.
#define ISOTP_RX_TIMEOUT_MS 			200000
#define ISOTP_TX_TIMEOUT_MS 			200000

// Timeout for extended diagnostic session.
// By default, other session types do not time out, although they would on real ECUs.
#define UDS_SESSION_TIMEOUT_MS 				5000

// Maximum RPM that will allow a transition to diagnostic sessions.
// Can be used to emulate a "Conditions not correct" error when the vehicle is running in Carla.
#define UDS_MAXIMUM_RPM_ACCEPTABLE 			0xFFF

// Delay before accepting a new security access attempt.
// This delay also applies to minimum time between ECU boot and first attempt.
#define SECURITY_ACCESS_RETRY_TIMEOUT_MS 	10

// Maximum Security access attempts before locking device.
#define SECURITY_ACCESS_MAX_ATTEMPTS 		5

// Enable this flag to ignore ISO TP messages that are not padded (like real ECUs do).
// When this flag is enabled, the ECU only checks that ISO-TP CAN message size is 8, it does not check the value of the padding bytes.
// This only applies to requests - see flag below for answers.
// #define ISOTP_REQUIRE_PADDING

// Define this flag to make the ECU pad its (classic CAN) ISO-TP answers with the defined byte (until ISO-TP CAN messages reach a size of 8).
// This only applies to answers - see flag above for requests.
// #define ISOTP_ANSWER_PADDING_BYTE 0x00

// Define this flag to pad CAN-FD ISO-TP answer frames up to the full configured ISOTP_TX_DL (64 bytes by default) instead of the smallest.
// #define ISOTP_FD_FULL_PADDING

#ifdef ENABLE_CDC
#define APP_RX_DATA_SIZE  2048
#define APP_TX_DATA_SIZE  2048
#define USB_COMMAND_BUFFER_SIZE		(8195)
#endif

#ifdef TARGET_ECUA
#define USB_RX_BUFFER_SIZE 				15000
#define USB_TX_BUFFER_SIZE 				15000
#define CAN_RX_BUFFER_SIZE 				15000
#define CAN_TX_BUFFER_SIZE 				15000
#define UDS_ISOTP_RX_BUFFER_SIZE 		0xFFF+2 //Add +2 for buffer-size
#define UDS_ISOTP_TX_BUFFER_SIZE 		0xFFF+2
#ifdef ENABLE_KWP
#define KWP_ISOTP_RX_BUFFER_SIZE 		0xFFF+2
#define KWP_ISOTP_TX_BUFFER_SIZE 		0xFFF+2
#endif
#ifdef ENABLE_XCP
#define XCP_RX_BUFFER_SIZE 				(4000)
#define XCP_TX_BUFFER_SIZE 				(4000)
#endif

#else
#define CAN_RX_BUFFER_SIZE 				20480
#define CAN_TX_BUFFER_SIZE 				20480
#define UDS_ISOTP_RX_BUFFER_SIZE 		(4097*6)
#define UDS_ISOTP_TX_BUFFER_SIZE 		(4097*6)
#define KWP_ISOTP_RX_BUFFER_SIZE 		(4097*6)
#define KWP_ISOTP_TX_BUFFER_SIZE 		(4097*6)
#define XCP_RX_BUFFER_SIZE 				(4000)
#define XCP_TX_BUFFER_SIZE 				(4000)
#endif

// This Extended ID is set as a hardware filter example event when CTF is disabled.
#define CTF_EXTENDED_ID 0x77cafe
#ifdef ENABLE_MINICTF
#define CTF_STANDARD_ID_1 0x456
#define CTF_STANDARD_ID_2 0x772
#define CTF_STANDARD_ID_3 0x457
#define CTF_STANDARD_ID_4 0x458
#endif



// Check for bad configurations --------------------------------------

#ifdef ENABLE_CDC
#if USB_RX_BUFFER_SIZE < (USB_COMMAND_BUFFER_SIZE+2)
#error define a larger USB_RX_BUFFER_SIZE
#endif
#endif

#if defined(TARGET_ECUA) + defined(TARGET_ECUB) + defined(TARGET_ECUC) + defined(TARGET_ECUD) != 1
    #error "You must define only one of TARGET_ECUA, TARGET_ECUB, TARGET_ECUC, and TARGET_ECUD."
#endif

#if defined(ENABLE_UART) && defined(ENABLE_CDC)
#error Default code does not support UART and CDC (USB Serial) at the same time. See comments for details.
// UART uses CDC task by default, and therefore CDC and UART cannot be used at the same time.
// You can enable both simultaneously by creating new receive/transmit tasks for UART, and move the UART code (between #define ENABLE_UART) in RAMN_ReceiveUSBFunc and RAMN_SendUSBFunc there.
// You should then modify HAL_UART_TxCpltCallback and HAL_UART_RxCpltCallback to notify these tasks instead.
#endif

#if defined(ENABLE_CHIP8) && !defined(ENABLE_SCREEN)
#error ENABLE_SCREEN must be defined to define ENABLE_CHIP8
#endif

#if !defined(ENABLE_USB) && defined(ENABLE_CDC)
#error Cannot activate CDC without enabling USB
#endif

#if !defined(ENABLE_USB) && defined(ENABLE_GSUSB)
#error Cannot activate GSUSB without enabling USB
#endif

#if defined(ENABLE_USB) && !defined(ENABLE_CDC) && !defined(ENABLE_GSUSB)
#error At least one USB interface must be active if you enable USB
#endif

#ifdef HARDENING
#ifdef ENABLE_GSUSB
#error "It is preferable to turn off GS_USB to limit attack surfaces. Comment out this line to enable anyway."
#endif
#ifdef ENABLE_KWP
#error "It is preferable to turn off KWP2000 to limit attack surfaces. Comment out this line to enable anyway."
#endif
#ifdef ENABLE_XCP
#error "It is preferable to turn off XCP to limit attack surfaces. Comment out this line to enable anyway (You'll need to update RAMN_MEMORY_CheckAreaReadable and/or XCP_COMMAND_UPLOAD)."
#endif
#ifdef ENABLE_J1979
#error "It is preferable to turn off J1979 to limit attack surfaces. Comment out this line to enable anyway"
#endif
#ifdef ENABLE_USB_DEBUG
#error "It is preferable to turn off USB debug to limit attack surfaces. Comment out this line to enable anyway."
#endif
#ifdef ENABLE_CHIP8
#error "It is preferable to turn off CHIP8 engine to limit attack surfaces. Comment out this line to enable anyway."
#endif
#ifdef ENABLE_MINICTF
#error "You may want to disable the mini-ctf to avoid conflicts. Comment out this line to enable anyway."
#endif
#ifdef ENABLE_UDS_REPROGRAMMING
#error "You may want to disable reprogramming to avoid accidental firmware erasure. Comment out this line to enable anyway."
#endif
#ifdef GENERATE_RUNTIME_STATS
#error "You may want to disable runtime stats to limit accessible information. Comment out this line to enable anyway."
#endif
#ifdef ENABLE_EEPROM_EMULATION
#error "You may want to disable EEPROM to limit potential memory issues. Comment out this line to enable anyway."
#endif
#endif


// To use the internal oscillator (instead of the default external 10MHz crystal), You should modify RAMNV1.ioc so that:
// - PLL Source Mux uses HSI with *N = X 10
// - PLLSAI1 Source Mux uses HSI with *N = X 15
// You should then regenerate the source code (refer to docs/firmware/img/internal_clock_settings.png and external_clock_settings.png to compare clock settings).
// If you do not want to use the code generation feature,you can also modify the source code directly so that the following values are used instead of default values:
//
// In stm32l5xx_hal_msp.c:
// PeriphClkInit.PLLSAI1.PLLSAI1Source = RCC_PLLSAI1SOURCE_HSI;
// PeriphClkInit.PLLSAI1.PLLSAI1N = 15;
//
// In main.c:
//
// RCC_OscInitStruct.OscillatorType = RCC_OSCILLATORTYPE_HSI48|RCC_OSCILLATORTYPE_HSI|RCC_OSCILLATORTYPE_LSI;
// RCC_OscInitStruct.HSIState = RCC_HSI_ON;
// RCC_OscInitStruct.HSICalibrationValue = RCC_HSICALIBRATION_DEFAULT;
// RCC_OscInitStruct.PLL.PLLSource = RCC_PLLSOURCE_HSI;
// RCC_OscInitStruct.PLL.PLLN = 10;

#endif /* INC_RAMN_CONFIG_H_ */
