ToyotaInfoTech/RAMN/firmware/RAMNV1/Core/Inc/ramn_signal_defs.h

/*
 * ramn_signal_defs.h
 ******************************************************************************
 * @attention
 *
 * <h2><center>&copy; Copyright (c) 2025 TOYOTA MOTOR CORPORATION.
 * ALL RIGHTS RESERVED.</center></h2>
 *
 * This software component is licensed by TOYOTA MOTOR CORPORATION under BSD 3-Clause license,
 * the "License"; You may not use this file except in compliance with the
 * License. You may obtain a copy of the License at:
 *                        opensource.org/licenses/BSD-3-Clause
 *
 ******************************************************************************
 */

#ifndef INC_RAMN_SIGNAL_DEFS_H_
#define INC_RAMN_SIGNAL_DEFS_H_

#include "main.h"

// Macros for signal packing/unpacking
// Note: These macros assume the payload container is large enough.
// mask: The mask of the signal value (e.g. 0xFF for 8-bit signal)
// offset: The bit shift count to place/retrieve the signal
#define PACK_SIGNAL(val, mask, offset)       (((val) & (mask)) << (offset))
#define UNPACK_SIGNAL(payload, mask, offset) (((payload) >> (offset)) & (mask))

#ifdef USE_BIG_ENDIAN_CAN
#undef PACK_SIGNAL
#define PACK_SIGNAL(val, mask, offset) \
    ((mask) == 0xFFFF ? \
    ((((((val) & (mask)) << (offset)) & 0xFF) << 8) | (((((val) & (mask)) << (offset)) >> 8) & 0xFF)) : \
    (((val) & (mask)) << (offset)))

#undef UNPACK_SIGNAL
#define UNPACK_SIGNAL(payload, mask, offset) \
    ((mask) == 0xFFFF ? \
    ((((((payload) >> (offset)) & (mask)) & 0xFF) << 8) | (((((payload) >> (offset)) & (mask)) >> 8) & 0xFF)) : \
    (((payload) >> (offset)) & (mask)))
#endif

// Signal Definitions

// Control Brake
// Default ID: DID_CONTROL_BRAKE (0x24)
#define CONTROL_BRAKE_MASK      0xFFFF
#define CONTROL_BRAKE_OFFSET    0
#define CONTROL_BRAKE_SCALE     1.0f

// Command Brake
// Default ID: DID_COMMAND_BRAKE (0x1A)
#define COMMAND_BRAKE_MASK      0xFFFF
#define COMMAND_BRAKE_OFFSET    0
#define COMMAND_BRAKE_SCALE     1.0f

// Control Accel
// Default ID: DID_CONTROL_ACCEL (0x39)
#define CONTROL_ACCEL_MASK      0xFFFF
#define CONTROL_ACCEL_OFFSET    0
#define CONTROL_ACCEL_SCALE     1.0f

// Command Accel
// Default ID: DID_COMMAND_ACCEL (0x2F)
#define COMMAND_ACCEL_MASK      0xFFFF
#define COMMAND_ACCEL_OFFSET    0
#define COMMAND_ACCEL_SCALE     1.0f

// Status RPM
// Default ID: DID_STATUS_RPM (0x43)
#define STATUS_RPM_MASK         0xFFFF
#define STATUS_RPM_OFFSET       0
#define STATUS_RPM_SCALE        1.0f

// Control Steering
// Default ID: DID_CONTROL_STEERING (0x62)
#define CONTROL_STEERING_MASK   0xFFFF
#define CONTROL_STEERING_OFFSET 0
#define CONTROL_STEERING_SCALE  1.0f

// Command Steering
// Default ID: DID_COMMAND_STEERING (0x58)
#define COMMAND_STEERING_MASK   0xFFFF
#define COMMAND_STEERING_OFFSET 0
#define COMMAND_STEERING_SCALE  1.0f

// Control Shift
// Default ID: DID_CONTROL_SHIFT (0x77)
#define CONTROL_SHIFT_MASK      0xFF
#define CONTROL_SHIFT_OFFSET    0
#define CONTROL_SHIFT_SCALE     1.0f

// Joystick (Packed with Control Shift)
// Default ID: DID_CONTROL_SHIFT (0x77)
#define JOYSTICK_MASK           0xFF
#define JOYSTICK_OFFSET         8
#define JOYSTICK_SCALE          1.0f

// Command Shift
// Default ID: DID_COMMAND_SHIFT (0x6D)
#define COMMAND_SHIFT_MASK      0xFF
#define COMMAND_SHIFT_OFFSET    0
#define COMMAND_SHIFT_SCALE     1.0f

// Command Horn
// Default ID: DID_COMMAND_HORN (0x98)
#define COMMAND_HORN_MASK       0xFF
#define COMMAND_HORN_OFFSET     0
#define COMMAND_HORN_SCALE      1.0f

// Control Horn
// Default ID: DID_CONTROL_HORN (0xA2)
#define CONTROL_HORN_MASK       0xFF
#define CONTROL_HORN_OFFSET     0
#define CONTROL_HORN_SCALE      1.0f

// Control Sidebrake
// Default ID: DID_CONTROL_SIDEBRAKE (0x1D3)
#define CONTROL_SIDEBRAKE_MASK   0xFF
#define CONTROL_SIDEBRAKE_OFFSET 0
#define CONTROL_SIDEBRAKE_SCALE  1.0f

// Command Sidebrake
// Default ID: DID_COMMAND_SIDEBRAKE (0x1C9)
#define COMMAND_SIDEBRAKE_MASK   0xFFFF
#define COMMAND_SIDEBRAKE_OFFSET 0
#define COMMAND_SIDEBRAKE_SCALE  1.0f

// Command Turn Indicator
// Default ID: DID_COMMAND_TURNINDICATOR (0x1A7)
#define COMMAND_TURNINDICATOR_MASK   0xFFFF
#define COMMAND_TURNINDICATOR_OFFSET 0
#define COMMAND_TURNINDICATOR_SCALE  1.0f

// Control Engine Key
// Default ID: DID_CONTROL_ENGINEKEY (0x1B8)
#define CONTROL_ENGINEKEY_MASK   0xFF
#define CONTROL_ENGINEKEY_OFFSET 0
#define CONTROL_ENGINEKEY_SCALE  1.0f

// Command Lights
// Default ID: DID_COMMAND_LIGHTS (0x150)
// High byte (0xFF00): engine warning flags. Low byte (0x00FF): light switch position (RAMN_LIGHTSWITCH_POSx).
#define COMMAND_LIGHTS_MASK      0xFFFF
#define COMMAND_LIGHTS_OFFSET    0
#define COMMAND_LIGHTS_SCALE     1.0f

// Control Lights
// Default ID: DID_CONTROL_LIGHTS (0x1BB)
#define CONTROL_LIGHTS_MASK      0xFF
#define CONTROL_LIGHTS_OFFSET    0
#define CONTROL_LIGHTS_SCALE     1.0f

#endif /* INC_RAMN_SIGNAL_DEFS_H_ */
