ToyotaInfoTech/RAMN/firmware/RAMNV1/Core/Src/ramn_chip8.c

/*
 * ramn_chip8.c
 ******************************************************************************
 * @attention
 *
 * <h2><center>&copy; Copyright (c) 2025 TOYOTA MOTOR CORPORATION.
 * ALL RIGHTS RESERVED.</center></h2>
 *
 * This software component is licensed by TOYOTA MOTOR CORPORATION under BSD 3-Clause license,
 * the "License"; You may not use this file except in compliance with the
 * License. You may obtain a copy of the License at:
 *                        opensource.org/licenses/BSD-3-Clause
 *
 ******************************************************************************
 */

#include "ramn_chip8.h"

#ifdef ENABLE_CHIP8

// Used to read joystick input
#include "ramn_sensors.h"
#include "ramn_dbc.h"

/*=====================================================================*
 *                            Private global                             *
 *======================================================================*/

/*
0x000-0x1FF - Reserved area (contains fonts, etc.)
0x200-0xFFF - Actual game memory
 */

// Interpreter memory
// TODO: put these in heap?
__attribute__ ((section (".buffers"))) static uint8_t memory[CHIP8_MEMORY_SIZE];
// Current opcode
static uint16_t opcode;
// Working registers
static uint8_t V[16];
// RPL registers (for super chip)
static uint8_t RPL[8];
// Memory pointer
static uint16_t I;
// Program Counter
static uint16_t PC;

// Stack of interpreter
static uint16_t stack[32];
// Stack Pointer
static uint16_t SP;
// Status of each Key. Note that some keys are ignored or redundant since RAMN does not feature 16 keys.
static uint16_t keys = 0x0000;
static uint8_t delayTimer;
static uint8_t soundTimer;

// Keeps track of which keys are being pressed, only used by FX0A opcode
static uint16_t keysWaitingRelease = 0x0000;

#define DEFAULT_SCREEN_X 24U
#define DEFAULT_SCREEN_Y 46U
#define DEFAULT_SCREEN_WIDTH 64U
#define DEFAULT_SCREEN_HEIGHT 32U
#define SCREEN_BUFFER_SIZE ((MAX_SCREEN_WIDTH * MAX_SCREEN_HEIGHT) / 8)

// Values below may be impacted by super chip mode
static uint16_t screenStartX = DEFAULT_SCREEN_X;
static uint16_t screenStartY = DEFAULT_SCREEN_Y;
static uint8_t pixelSize = DEFAULT_PIXEL_SIZE;
static uint8_t screenWidth = DEFAULT_SCREEN_WIDTH;
static uint8_t screenHeight = DEFAULT_SCREEN_HEIGHT;
static RAMN_Bool_t extended = False;

// screenBuffer is used for CHIP8 pixel status.
// spriteBuffer is used to actually draw on the screen (SPI buffer).
// TODO: put these in heap?
__attribute__ ((section (".buffers"))) static uint8_t screenBuffer[SCREEN_BUFFER_SIZE];
__attribute__ ((section (".buffers"))) static uint16_t spriteBuffer[SPRITE_BUFFER_HEIGHT*SPRITE_BUFFER_WIDTH*DEFAULT_PIXEL_SIZE*DEFAULT_PIXEL_SIZE] __attribute__ ((section (".buffers")));

static uint16_t backColor = COLOR_BLACK;
static uint16_t frontColor = COLOR_WHITE;

static RAMN_Bool_t screenInitialized = False;
static RAMN_Bool_t gameStarted = False;
static uint32_t lastTimerUpdate = 0;

static unsigned const char CHIP8_FONT[240U] =
{
		// Low Resolution
		0xF0, 0x90, 0x90, 0x90, 0xF0, // 0
		0x20, 0x60, 0x20, 0x20, 0x70, // 1
		0xF0, 0x10, 0xF0, 0x80, 0xF0, // 2
		0xF0, 0x10, 0xF0, 0x10, 0xF0, // 3
		0x90, 0x90, 0xF0, 0x10, 0x10, // 4
		0xF0, 0x80, 0xF0, 0x10, 0xF0, // 5
		0xF0, 0x80, 0xF0, 0x90, 0xF0, // 6
		0xF0, 0x10, 0x20, 0x40, 0x40, // 7
		0xF0, 0x90, 0xF0, 0x90, 0xF0, // 8
		0xF0, 0x90, 0xF0, 0x10, 0xF0, // 9
		0xF0, 0x90, 0xF0, 0x90, 0x90, // A
		0xE0, 0x90, 0xE0, 0x90, 0xE0, // B
		0xF0, 0x80, 0x80, 0x80, 0xF0, // C
		0xE0, 0x90, 0x90, 0x90, 0xE0, // D
		0xF0, 0x80, 0xF0, 0x80, 0xF0, // E
		0xF0, 0x80, 0xF0, 0x80, 0x80,  // F

		// High Resolution
		0x3C, 0x7E, 0xE7, 0xC3, 0xC3, 0xC3, 0xC3, 0xE7, 0x7E, 0x3C,
		0x18, 0x38, 0x58, 0x18, 0x18, 0x18, 0x18, 0x18, 0x18, 0x3C,
		0x3E, 0x7F, 0xC3, 0x06, 0x0C, 0x18, 0x30, 0x60, 0xFF, 0xFF,
		0x3C, 0x7E, 0xC3, 0x03, 0x0E, 0x0E, 0x03, 0xC3, 0x7E, 0x3C,
		0x06, 0x0E, 0x1E, 0x36, 0x66, 0xC6, 0xFF, 0xFF, 0x06, 0x06,
		0xFF, 0xFF, 0xC0, 0xC0, 0xFC, 0xFE, 0x03, 0xC3, 0x7E, 0x3C,
		0x3E, 0x7C, 0xC0, 0xC0, 0xFC, 0xFE, 0xC3, 0xC3, 0x7E, 0x3C,
		0xFF, 0xFF, 0x03, 0x06, 0x0C, 0x18, 0x30, 0x60, 0x60, 0x60,
		0x3C, 0x7E, 0xC3, 0xC3, 0x7E, 0x7E, 0xC3, 0xC3, 0x7E, 0x3C,
		0x3C, 0x7E, 0xC3, 0xC3, 0x7F, 0x3F, 0x03, 0x03, 0x3E, 0x7C
};

/*=====================================================================*
 *                            Public global                             *
 *======================================================================*/

//Example games from https://github.com/JohnEarnest/chip8Archive

//Cave Explorer
const uint8_t CAVE_EXPLORER[] = {0x1e,0xa5,0x20,0x20,0x20,0x00,0x20,0xf0,0x10,0x70,0x00,0x40,0xe0,0x90,0xe0,0x90,0x90,0x90,0xe0,0x90,0xe0,0x90,0xe0,0x80,0x80,0xd0,0xb0,0xb0,0x90,0x90,0x90,0x90,0x60,0x60,0x90,0x90,0x90,0x60,0x90,0xd0,0xb0,0x90,0x90,0x90,0x50,0x20,0x40,0x00,0x00,0x00,0x00,0x00,0x60,0x90,0xf0,0x90,0x90,0xf0,0x90,0x90,0xf0,0x80,0xe0,0x80,0x80,0x80,0x80,0xf0,0x80,0xe0,0x80,0xf0,0x40,0x40,0x40,0xf0,0x20,0x40,0x80,0xf0,0x20,0x20,0x20,0xc0,0x60,0x90,0x80,0x90,0x60,0x90,0x90,0xb0,0x70,0x80,0xb0,0x90,0x70,0x80,0x60,0x10,0xe0,0x90,0xa0,0xc0,0xa0,0x90,0x90,0xb0,0xb0,0xd0,0xf0,0x40,0x40,0x40,0x40,0x90,0x90,0x70,0x10,0xe0,0x00,0x00,0x00,0x00,0x00,0x00,0x00,0x00,0x00,0x00,0x00,0x00,0x00,0x00,0x00,0x00,0x00,0x00,0x00,0x00,0x00,0x00,0x00,0x00,0x00,0x00,0x00,0x00,0x00,0x00,0x00,0x00,0x00,0x00,0x00,0x00,0x00,0x00,0x00,0x00,0x00,0x00,0x00,0x00,0x00,0x00,0x00,0x00,0x00,0x00,0x00,0x00,0x00,0x00,0x00,0x00,0x00,0x00,0x00,0x00,0x00,0x00,0x00,0x00,0x00,0x00,0x00,0x00,0x00,0x00,0x00,0x00,0x00,0x00,0x00,0x00,0x00,0x00,0x00,0x00,0x00,0x00,0x00,0x00,0x00,0x00,0x00,0x00,0x00,0x00,0x00,0x00,0x00,0x00,0x00,0x00,0x00,0x00,0x00,0x00,0x00,0x00,0x00,0x00,0x07,0xe0,0x00,0x00,0x00,0x00,0x00,0x00,0x08,0x18,0x00,0x00,0x00,0x00,0x00,0x00,0x10,0x04,0x00,0x00,0x00,0x00,0x00,0x00,0x20,0x02,0x00,0x00,0x00,0x00,0x00,0x00,0x20,0x02,0x00,0x00,0x00,0x00,0x00,0x00,0x28,0x21,0x00,0x00,0x00,0x00,0x00,0x00,0x40,0x01,0x00,0x00,0x00,0x00,0x00,0x00,0x40,0x01,0x00,0x00,0x00,0x00,0x00,0x00,0x40,0x01,0x00,0x00,0x00,0x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
const uint16_t CAVE_EXPLORER_SIZE = sizeof(CAVE_EXPLORER);

//Danm8ku
const uint8_t DANMAKU[] = {0x14,0xe2,0xe0,0x00,0x80,0x79,0x00,0x60,0x0c,0x0c,0x3e,0x0c,0x9b,0xfd,0x20,0x63,0x1c,0x0c,0x3e,0x0c,0xfb,0xcd,0x70,0xe7,0x1c,0x1e,0x23,0x0c,0xf3,0xfd,0xf8,0xcf,0x1e,0x1f,0x21,0x0c,0xc3,0xfd,0xd8,0xcd,0x1e,0x9b,0x21,0x1c,0xe3,0xcd,0xdd,0xdd,0x9e,0xbf,0x21,0x98,0xf3,0x8d,0xcd,0xd9,0x9f,0x3f,0x23,0xf8,0xf9,0x9d,0xcd,0xd9,0xdb,0x71,0x3f,0xf0,0x98,0xf9,0xcd,0xd9,0xd9,0x60,0x3c,0x00,0x00,0xf8,0x00,0x00,0x00,0x00,0x00,0x1e,0x10,0x10,0x10,0x1e,0x10,0x10,0x10,0xea,0xaa,0xaa,0xaa,0xee,0xea,0x8a,0x8e,0x8a,0xea,0xae,0xa8,0x4c,0x48,0x4e,0xe4,0x84,0xe4,0x20,0xe4,0xff,0x00,0x00,0x00,0x00,0x00,0x00,0x00,0xa0,0xa0,0x00,0x00,0x50,0x50,0x00,0x00,0x60,0x60,0x00,0x60,0x00,0x60,0x00,0xc0,0xa0,0x60,0x00,0x30,0x50,0x60,0x00,0x00,0x05,0x0f,0x00,0x00,0x60,0x00,0x60,0x00,0x60,0xa0,0xc0,0x00,0x60,0x50,0x30,0x00,0x60,0x60,0x00,0x00,0xc0,0xc0,0x00,0x00,0x30,0x30,0x00,0xc0,0x60,0xc0,0x00,0x60,0x60,0x00,0x00,0xc0,0xc0,0x00,0x00,0x30,0x30,0x00,0x00,0xa0,0x40,0xa0,0x00,0x00,0x00,0x60,0x60,0x00,0x00,0xc0,0xc0,0x00,0x00,0x30,0x30,0x00,0xe0,0x6a,0x38,0x6b,0x0b,0xa2,0x03,0xda,0xb1,0xf0,0x65,0x7a,0xf8,0x4a,0xf8,0x7b,0x01,0x4a,0xf8,0x6a,0x38,0x3b,0x15,0x12,0xd2,0x64,0x05,0xe4,0xa1,0x00,0xee,0x64,0x07,0xe4,0xa1,0x00,0xee,0x64,0x08,0xe4,0xa1,0x00,0xee,0x64,0x09,0xe4,0xa1,0x00,0xee,0xa2,0x02,0x60,0x00,0xc1,0x1f,0x71,0xf6,0x6f,0x0b,0x8f,0x17,0x4f,0x00,0x12,0xe4,0x71,0x0a,0x62,0x3c,0x40,0x20,0x12,0xe4,0xd0,0x12,0xd2,0x12,0x3f,0x01,0x12,0xe4,0x70,0x04,0x72,0xfc,0x13,0x10,0x00,0xe0,0x63,0x1f,0x6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
2,0x40,0x00,0x16,0xb5,0x65,0x1c,0x61,0xa0,0x16,0xb9,0x65,0x00,0x61,0x1e,0xc4,0x1f,0x74,0x1f,0x60,0xbe,0x24,0x5e,0x25,0x76,0x15,0x74,0x60,0x07,0x80,0xd2,0x30,0x07,0x16,0xe7,0x60,0x10,0x80,0xd2,0x65,0x1c,0x61,0xa0,0x30,0x00,0x16,0xdd,0x65,0x00,0x61,0x1e,0x60,0x00,0x62,0x00,0xc4,0x1f,0x24,0x5e,0x25,0x76,0x15,0x74,0x60,0x0f,0x80,0xd2,0x30,0x0f,0x17,0x0f,0x85,0xd6,0x85,0x56,0x85,0x56,0x64,0x32,0x60,0x5f,0x61,0x00,0x62,0x05,0x24,0x5e,0x25,0x76,0x61,0x14,0x24,0x5e,0x25,0x76,0x61,0x94,0x24,0x5e,0x25,0x76,0x15,0x74,0x23,0x22,0x14,0xe2,0x15,0x7e,0x15,0x98,0x16,0x03,0x16,0x27,0x16,0x73,0x16,0x9f,0x16,0xc5,0x16,0xe9,0x17,0x11,};
const uint16_t DANMAKU_SIZE = sizeof(DANMAKU);

//Octopeg
const uint8_t OCTOPEG[] = {0x1c,0x16,0x22,0x0a,0x62,0x80,0x22,0x28,0x00,0xee,0x60,0xad,0x61,0x91,0xa2,0x8c,0xf1,0x55,0xa2,0xb4,0xf1,0x55,0x60,0x12,0x61,0xd0,0xa2,0xc8,0xf1,0x55,0x60,0x12,0x61,0xd2,0xa2,0xcc,0xf1,0x55,0x00,0xee,0x65,0x00,0x64,0x01,0x34,0x01,0x12,0x44,0x22,0xa0,0xf0,0x65,0x30,0xff,0x12,0x42,0x45,0x00,0x00,0xee,0x60,0x00,0x64,0x00,0x12,0x44,0x85,0x04,0x22,0x8c,0xf0,0x65,0x83,0x00,0x22,0xc8,0x80,0x30,0x80,0x54,0x6e,0x09,0x8e,0x05,0x4f,0x01,0x12,0x6a,0x70,0xf6,0x83,0x00,0x65,0x01,0x22,0xb4,0xf0,0x55,0x22,0x90,0x22,0xb8,0x80,0x30,0x12,0x72,0x83,0x00,0x65,0x00,0x22,0xb4,0xf0,0x55,0x22,0xcc,0x34,0x01,0x12,0x82,0x35,0x00,0x12,0x80,0x22,0x90,0x22,0xb8,0x22,0xa4,0x80,0x50,0x80,0x44,0x30,0x00,0x12,0x2c,0x00,0xee,0x00,0x00,0x00,0xee,0xa2,0x8c,0xf1,0x65,0x6f,0x01,0x81,0xf4,0x80,0xf4,0xa2,0x8c,0xf1,0x55,0x00,0xee,0x00,0x00,0x00,0xee,0xa2,0xa0,0xf1,0x65,0x6f,0x01,0x81,0xf4,0x80,0xf4,0xa2,0xa0,0xf1,0x55,0x00,0xee,0x00,0x00,0x00,0xee,0xa2,0xb4,0xf1,0x65,0x6f,0x01,0x81,0xf4,0x80,0xf4,0xa2,0xb4,0xf1,0x55,0x00,0xee,0x00,0x00,0x00,0xee,0x00,0x00,0x00,0xee,0x72,0xfb,0xf0,0x29,0x6f,0x01,0xd2,0xf5,0x00,0xee,0x61,0x00,0x62,0x80,0x6e,0x00,0xad,0x91,0xf1,0x1e,0x71,0x01,0xf0,0x65,0x22,0xd0,0x7e,0x01,0x3e,0x06,0x12,0xe0,0x00,0xee,0xf1,0x1e,0x71,0x01,0xf0,0x65,0x40,0xff,0x60,0x00,0xf0,0x29,0xd3,0x45,0x7e,0x01,0x00,0xee,0x63,0x5d,0x64,0x04,0x6e,0x00,0x61,0x00,0xad,0x88,0x73,0xfb,0x22,0xf2,0x3e,0x06,0x13,0x0c,0x6f,0x00,0x61,0x24,0x62,0x04,0xaf,0x9a,0x2e,0xe9,0x3f,0xff,0x13,0x1c,0x00,0xee,0x6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
const uint16_t OCTOPEG_SIZE = sizeof(OCTOPEG);

/*=====================================================================*
 *                          Private functions                           *
 *======================================================================*/

static inline void CHIP8_SetKeyState(uint8_t keyIndex, RAMN_Bool_t pressed)
{
    if (pressed) keys |= (1 << keyIndex);
    else keys &= ~(1 << keyIndex);
}

static inline RAMN_Bool_t CHIP8_GetKeyState(uint8_t keyIndex)
{
    return (keys & (1 << keyIndex)) ? True : False;
}

//Note that this is used to saved the status of the screen, this does not draw on the screen
static inline void CHIP8_SetPixel(uint32_t x, uint32_t y, uint8_t value)
{
    uint32_t index = (y * screenWidth + x);
    uint32_t byteIndex = index / 8U;
    uint8_t bitIndex = index % 8U;

    if (value) screenBuffer[byteIndex] |= (1U << bitIndex);  // Set bit
    else screenBuffer[byteIndex] &= ~(1U << bitIndex); // Clear bit
}

static inline uint8_t CHIP8_GetPixel(uint32_t x, uint32_t y)
{
    uint32_t index = (y * screenWidth + x);
    uint32_t byteIndex = index / 8U;
    uint8_t bitIndex = index % 8U;

    return (screenBuffer[byteIndex] & (1U << bitIndex)) ? 1U : 0U;
}

static void CHIP8_ScrollUpByNPixels(uint8_t n)
{
	for (int x = 0; x < screenWidth; x++) {

		for (int y = n; y < screenHeight; y++) {
			CHIP8_SetPixel(x, y-n, CHIP8_GetPixel(x,y));
		}

		// Fill the rightmost 4 pixels with 0
		for (int y = screenHeight - n; y < screenWidth; y++) {
			CHIP8_SetPixel(x, y, 0U);
		}
	}
}

static void CHIP8_ScrollDownByNPixels(uint8_t n)
{
	for (int x = 0; x < screenWidth; x++) {

		for (int y = screenHeight-n-1; y >= 0 ; y--) {
			CHIP8_SetPixel(x, y+n, CHIP8_GetPixel(x,y));
		}

		// Fill the rightmost 4 pixels with 0
		for (int y = 0; y < n; y++) {
			CHIP8_SetPixel(x, y, 0U);
		}
	}
}

static void CHIP8_ScrollLeftBy4Pixels() {
	uint8_t n = 4;
	if (extended == False) n = 2;
	for (int y = 0; y < screenHeight; y++) {
		for (int x = 0; x < screenWidth - n; x++) {
			CHIP8_SetPixel(x+n, y, CHIP8_GetPixel(x,y));
		}

		// Fill the rightmost 4 pixels with 0
		for (int x = screenWidth - n; x < screenWidth; x++) {
			CHIP8_SetPixel(x, y, 0U);
		}
	}
}

static void CHIP8_ScrollRightBy4Pixels() {
	uint8_t n = 4;
	if (extended == False) n = 2;

	for (int y = 0; y < screenHeight; y++) {
		for (int x = screenWidth-1; x >= n; x--) {
			CHIP8_SetPixel(x-n, y, CHIP8_GetPixel(x,y));
		}

		// Fill the left 4 pixels with 0
		for (int x = 0; x < n; x++) {
			CHIP8_SetPixel(x, y, 0U);
		}
	}
}

/*=====================================================================*
 *                          Public functions                           *
 *======================================================================*/

void RAMN_CHIP8_SetColor(uint16_t fg, uint16_t bg)
{
	frontColor = fg;
	backColor = bg;
}

void RAMN_CHIP8_Init(const uint8_t* game_to_load, uint16_t game_size)
{
	PC     = 0x200;  // game location
	opcode = 0;
	I      = 0;
	SP     = 0;
	delayTimer = 0;
	soundTimer = 0; // Note that this is not implemented since there is no buzzer

	//Clear registers
	for(uint8_t i = 0; i < 0x10; i++)
		V[i] = 0;

	//Load font
	for(int i = 0; i < sizeof(CHIP8_FONT); ++i)
		memory[FONT_ADDRESS + i] = CHIP8_FONT[i];

	//Load game
	for(uint16_t i = 0; i < game_size; ++i)
		memory[0x200 + i] = game_to_load[i];

	//Clear RPL
	for (uint8_t i = 0; i < 8; i++)
	{
		RPL[i] = 0;
	}

	for(uint16_t i = 0x200 + game_size; i < sizeof(memory); ++i)
		memory[i] = 0;

	//clear screen
	screenInitialized = False;
	for(uint32_t i = 0; i < sizeof(screenBuffer); i++) screenBuffer[i] = 0;

	for(uint32_t i = 0; i < 16U*16U*3U*3U; i++) spriteBuffer[i] = backColor;

	//Verify that we are in chip 8 mode
	pixelSize = DEFAULT_PIXEL_SIZE;
	extended = False;
	screenStartX = 24;
	screenStartY = 46;
	screenWidth = 64;
	screenHeight = 32;
}

RAMN_Bool_t RAMN_CHIP8_IsGameActive()
{
	return gameStarted;
}

void RAMN_CHIP8_StartGame(uint32_t xLastWakeTime)
{
	lastTimerUpdate = xLastWakeTime;
	gameStarted = True;
}

void RAMN_CHIP8_StopGame()
{
	gameStarted = False;
}

void RAMN_CHIP8_Update(uint32_t xLastWakeTime)
{
	uint8_t X;
	uint8_t Y;
	uint8_t CARRY;

	keys = 0x0000;
	switch((RAMN_DBC_Handle.joystick))
	{
	case RAMN_SHIFT_UP:
		CHIP8_SetKeyState(0x5,True);
		break;
	case RAMN_SHIFT_DOWN:
		CHIP8_SetKeyState(0x8,True);
		break;
	case RAMN_SHIFT_RIGHT:
		CHIP8_SetKeyState(0x9,True);
		break;
	case RAMN_SHIFT_LEFT:
		CHIP8_SetKeyState(0x7,True);
		break;
	case RAMN_SHIFT_PUSH:
		CHIP8_SetKeyState(0x6,True); //redundant with UP
		break;
	}

	if (xLastWakeTime - lastTimerUpdate > 16)
	{
		if (soundTimer > 0) soundTimer -= 1;
		if (delayTimer > 0) delayTimer -= 1;
		lastTimerUpdate = xLastWakeTime;
	}

	if (PC >= (sizeof(memory)-1) || (I >= sizeof(memory))) // PC or I overflow
	{
		gameStarted = False;
		return;
	}
	opcode = memory[PC] << 8 | memory[PC + 1];

	switch (opcode & 0xF000)
	{
	case 0x0000:
		switch (opcode & 0x00FF)
		{
		case 0x0001:
			//Consider Noop
			PC += 2;
			break;
		case 0x00E0:
			for(uint32_t i = 0; i < sizeof(screenBuffer); i++) screenBuffer[i] = 0;
			RAMN_SPI_DrawRectangle(screenStartX, screenStartY, screenWidth*pixelSize, screenHeight*pixelSize, backColor);
			PC += 2;
			break;
		case 0x00EE:
			SP -= 1;
			if (SP >= (sizeof(stack)/sizeof(uint16_t))) //if an underflow happened, quit
			{
				gameStarted = False;
			}
			PC = stack[SP];
			PC += 2;
			break;
		case 0x00FB:
			CHIP8_ScrollRightBy4Pixels();
			RAMN_CHIP8_RedrawScreen();
			PC += 2;
			break;
		case 0x00FC:
			CHIP8_ScrollLeftBy4Pixels();
			RAMN_CHIP8_RedrawScreen();
			PC += 2;
			break;
		case 0x00FD:
			gameStarted = False;
			break;
		case 0x00FE:
			pixelSize = DEFAULT_PIXEL_SIZE;
			extended = False;
			screenStartX = 24;
			screenStartY = 46;
			screenWidth = 64;
			screenHeight = 32;
			PC += 2;
			screenInitialized = False; //redraw
			break;
		case 0x00FF:
			pixelSize = 1;
			screenStartX = 56;
			screenStartY = 64;
			screenWidth = 128;
			screenHeight = 64;
			extended = True;
			PC += 2;
			screenInitialized = False; //redraw
			break;
		default:
			switch (opcode & 0x00F0)
			{
			case 0x00D0:
				CHIP8_ScrollUpByNPixels(opcode&0xF);
				RAMN_CHIP8_RedrawScreen();
				PC += 2;
				break;
			case 0x00C0:
				CHIP8_ScrollDownByNPixels(opcode&0xF);
				RAMN_CHIP8_RedrawScreen();
				PC += 2;
				break;
			default:
				gameStarted = False;
			}
		}
		break;

		case 0x1000:
			PC = opcode & 0x0FFF;
			break;
		case 0x2000:
			stack[SP] = PC;
			SP++;  // incrementing the SP
			if (SP >= (sizeof(stack)/sizeof(uint16_t)))
			{
				gameStarted = False;
			}
			PC = opcode & 0x0FFF;
			break;
		case 0x3000:
			//0x3XNN SKIP NEXT IF VX EQUALS NN
			if (V[(opcode & 0x0F00) >> 8] == (opcode & 0x00FF))
				PC += 2;
			PC += 2;
			break;
		case 0x4000:
			//0x4XNN SKIP NEXT IF VX NOT EQUALS NN
			if (V[(opcode & 0x0F00) >> 8] != (opcode & 0x00FF))
				PC += 2;
			PC += 2;
			break;
		case 0x5000:
			//0xXY0 SKIP NEXT IF VX EQUALS VY
			if (V[(opcode & 0x0F00) >> 8] == V[(opcode & 0x00F0) >> 4])
				PC += 2;
			PC += 2;
			break;
		case 0x6000:
			//0x6XNN SET VX TO NN
			V[(opcode & 0x0F00) >> 8] = opcode & 0x00FF;
			PC += 2;
			break;
		case 0x7000:
			//0x7XNN ADD NN TO VX
			V[(opcode & 0x0F00) >> 8] += (opcode & 0x00FF);
			PC += 2;
			break;
		case 0x8000:
			X = (opcode & 0xF00) >> 8;
			Y = (opcode & 0x00F0) >> 4;
			switch (opcode & 0x000F)
			{
			case 0x0000:
				V[(opcode & 0xF00) >> 8] = V[(opcode & 0x00F0) >> 4];
				PC += 2;
				break;
			case 0x0001:
				V[(opcode & 0xF00) >> 8] |= V[(opcode & 0x00F0) >> 4];
				PC += 2;
				break;
			case 0x0002:
				V[(opcode & 0xF00) >> 8] &= V[(opcode & 0x00F0) >> 4];
				PC += 2;
				break;
			case 0x0003:
				V[(opcode & 0x0F00) >> 8] ^= V[(opcode & 0x00F0) >> 4];
				PC += 2;
				break;
			case 0x0004:
				if (V[(opcode & 0x00F0) >> 4] > (0xFF - V[(opcode & 0x0F00) >> 8]))
					CARRY = 1; //carry
				else
					CARRY = 0;
				V[(opcode & 0x0F00) >> 8] += V[(opcode & 0x00F0) >> 4];
				V[0xF] = CARRY;
				PC += 2;
				break;
			case 0x0005:
				if (V[(opcode & 0x00F0) >> 4] > V[(opcode & 0x0F00) >> 8])
					CARRY = 0;
				else
					CARRY = 1;
				V[(opcode & 0x0F00) >> 8] -= V[(opcode & 0x00F0) >> 4];
				V[0xF] = CARRY;
				PC += 2;
				break;
			case 0x0006:
				CARRY = V[Y] & 0x1;
				V[X] = V[Y] >> 1;
				V[0xF] = CARRY;
				PC += 2;
				break;
			case 0x000E:
				CARRY = (V[Y] >> 7)&0x1;
				V[X] = V[Y] << 1;
				V[0xF] = CARRY;
				PC += 2;
				break;
			case 0x0007:
				if (V[(opcode & 0x0F00) >> 8] > V[(opcode & 0x00F0) >> 4])
					CARRY = 0;
				else
					CARRY = 1;
				V[(opcode & 0x0F00) >> 8] = V[(opcode & 0x00F0) >> 4] - V[(opcode & 0x0F00) >> 8];
				V[0xF] = CARRY;
				PC += 2;
				break;
			default:
				gameStarted = False;
			}
			break;
			case 0x9000:
				// 0x9XY0: SKIP IF NOT EQUAL
				if (V[(opcode & 0x0F00) >> 8] != V[(opcode & 0x00F0) >> 4])
					PC += 2;
				PC += 2;
				break;
			case 0xA000:
				// ANNN: SET I TO NNN
				I = opcode & 0x0FFF;
				PC += 2;
				break;
			case 0xB000:
				// BNNN: JUMP
				PC = (opcode & 0x0FFF) + V[0];
				break;
			case 0xC000:
				//GET RNG
				V[(opcode & 0x0F00) >> 8] = (RAMN_RNG_Pop8() & 0xFF) & (opcode & 0x00FF);
				PC += 2;
				break;
			case 0xD000:
			{
				uint16_t x = V[(opcode & 0x0F00) >> 8];
				uint16_t y = V[(opcode & 0x00F0) >> 4];
				uint16_t height = opcode & 0x000F;
				uint16_t pixels;
				uint8_t wrapping = 0;
				uint8_t width = 8;
				V[0xF] = 0;

				if (screenInitialized == False)
				{
					//Note that we use Chip8 and not super chip8 value because chip8 has the bigger canvas.
					RAMN_SPI_DrawRectangle(DEFAULT_SCREEN_X, DEFAULT_SCREEN_Y, DEFAULT_SCREEN_WIDTH*DEFAULT_PIXEL_SIZE, DEFAULT_SCREEN_HEIGHT*DEFAULT_PIXEL_SIZE, backColor);
					screenInitialized = True;
				}

				if (height == 0)
				{
					if  (extended != False)
					{
						height = 16;
						width = 16;
					}
					else
					{
						height = 16;
						width = 16;
					}
				}
				uint16_t shift_mask = 0x80;
				uint8_t redraw_needed = 0U;
				wrapping = x+width > screenWidth || y+height > screenHeight;
				for (uint16_t yline = 0; yline < height; yline++)
				{
					uint16_t color;
					if (height == 16)
					{
						shift_mask = 0x8000;
						pixels = memory[I + yline*2] << 8;
						pixels |= memory[I + yline*2+1];
					}
					else
					{
						shift_mask = 0x80;
						pixels = memory[I + yline];
					}
					for (uint16_t xline = 0; xline < width; xline++)
					{
						uint8_t pixel = (pixels & (shift_mask >> xline)) != 0 ? 1U : 0U;

						if (pixel != 0)
						{
							redraw_needed = 1U;
							if (CHIP8_GetPixel((x + xline)%screenWidth,((y + yline)%screenHeight)) != 0U)
							{
								V[0xF] = 1;
							}
							// swap pixel
							CHIP8_SetPixel((x + xline)%screenWidth,(y + yline)%screenHeight, CHIP8_GetPixel((x + xline)%screenWidth, (y + yline)%screenHeight) ^ pixel);

							//if there is a screen wrap, we draw pixel by pixel
							if (wrapping != 0)
							{
								color = CHIP8_GetPixel((x + xline)%screenWidth, (y + yline)%screenHeight) == 0U ? backColor : frontColor;
								RAMN_SPI_DrawRectangle(screenStartX + ((x + xline)%screenWidth)*pixelSize, screenStartY + ((y + yline)%screenHeight)*pixelSize, pixelSize, pixelSize, color);
							}

						}
						if (wrapping == 0)
						{
							color = CHIP8_GetPixel((x + xline)%screenWidth, (y + yline)%screenHeight) == 0U ? backColor : frontColor;							for(uint8_t px = 0; px < pixelSize; px++)
							{
								for(uint8_t py = 0; py < pixelSize; py++)
								{
									spriteBuffer[(xline*pixelSize+px) + (yline*pixelSize+py)*(width*pixelSize)] = color;
								}
							}
						}
					}
				}
				//redraw if sprite change, and we haven't redrawn previously
				if (redraw_needed && (wrapping == 0U))
				{
					RAMN_SPI_DrawImage(screenStartX + (x%screenWidth)*(uint16_t)pixelSize,screenStartY + ((y)%screenHeight)*(uint16_t)pixelSize, (uint16_t)pixelSize*width, (uint16_t)pixelSize*height, (uint8_t*)spriteBuffer);
				}
				PC += 2;

			}
			break;

			case 0xE000:
				switch (opcode & 0x00FF)
				{
				case 0x009E:
					if (CHIP8_GetKeyState(V[(opcode & 0x0F00) >> 8]) != False)
						PC += 4;
					else
						PC += 2;
					break;
				case 0x00A1:
					if (CHIP8_GetKeyState(V[(opcode & 0x0F00) >> 8]) == False)
						PC += 4;
					else
						PC += 2;
					break;
				default:
					gameStarted = False;
				}
				break;
				case 0xF000:
					switch (opcode & 0x00FF)
					{
					case 0x0007:
						V[(opcode & 0x0F00) >> 8] = delayTimer;
						PC += 2;
						break;
					case 0x000A:
					{
						/* older implementation
						if (keyWaitingRelease == 0xFF)
						{
							for (uint8_t i = 0; i < 16; i++)
							{
								if (key[i] != 0)
								{
									keyWaitingRelease = i;
									break;
								}
							}
						}
						else
						{
							//Wait for key in V
							if (key[keyWaitingRelease] == 0)
							{
								V[(opcode & 0x0F00) >> 8] = keyWaitingRelease;
								PC += 2;
								keyWaitingRelease = 0xFF;
							}
						}*/

						for (uint8_t i = 0U; i < 16U; i++)
						{
							if (CHIP8_GetKeyState(i) != False)
							{
								keysWaitingRelease |= (1 << i);  // Mark key as "waiting for release"
							}
							else
							{
								if (keysWaitingRelease & (1 << i))
								{
									//Key used to be pressed but is now released
									V[(opcode & 0x0F00) >> 8U] = i;  // Store first released key in VX
									keysWaitingRelease = 0x0000;  // Reset tracking
									PC += 2;  // Move to next instruction
									break;
								}
							}
						}
					}
					break;
					case 0x0015:
						delayTimer = V[(opcode & 0x0F00) >> 8];
						PC += 2;
						break;
					case 0x0018:
						soundTimer = V[(opcode & 0x0F00) >> 8];
						PC += 2;
						break;
					case 0x001E:
						I += V[(opcode & 0x0F00) >> 8];
						PC += 2;
						break;
					case 0x0029:
						I = FONT_ADDRESS + V[(opcode & 0x0F00) >> 8] * 0x5;
						PC += 2;
						break;
					case 0x0030:
						I = FONT_ADDRESS + 80 + V[(opcode & 0x0F00) >> 8] * 10;
						PC += 2;
						break;
					case 0x0033:
						// ensure we aren't reading outside of valid memory
						if (I + 2 >= sizeof(memory))
						{
							gameStarted = False;
							break;
						}

						memory[I] = V[(opcode & 0x0F00) >> 8] / 100;
						memory[I + 1] = (V[(opcode & 0x0F00) >> 8] / 10) % 10;
						memory[I + 2] = (V[(opcode & 0x0F00) >> 8] % 100) % 10;
						PC += 2;
						break;
					case 0x0055:
						// ensure we aren't reading outside of valid memory
						if (I + ((opcode & 0x0F00) >> 8) >= sizeof(memory))
						{
							gameStarted = False;
							break;
						}

						for (uint8_t i = 0; i <= ((opcode & 0x0F00) >> 8); i++)
							memory[I + i] = V[i];
						I += (1 + ((opcode & 0x0F00) >> 8));
						PC += 2;
						break;

					case 0x0065:
						// ensure we aren't reading outside of valid memory
						if (I + ((opcode & 0x0F00) >> 8) >= sizeof(memory))
						{
							gameStarted = False;
							break;
						}

						for (uint8_t i = 0; i <= ((opcode & 0x0F00) >> 8); i++)
							V[i] = memory[I + i];
						I += (1 + ((opcode & 0x0F00) >> 8));
						PC += 2;
						break;

					case 0x0075:
						for (uint8_t i = 0; i <= ((opcode & 0x0F00) >> 8); i++)
						{
							RPL[i] = V[i];
						}
						PC += 2;
						break;
					case 0x0085:
						for (uint8_t i = 0; i <= ((opcode & 0x0F00) >> 8); i++)
						{
							V[i] = RPL[i];
						}
						PC += 2;
						break;
					default:
						gameStarted = False;
					}
					break;
					default:
						gameStarted = False;
	}
}

void RAMN_CHIP8_RedrawScreen()
{
	uint16_t color;
	for (uint16_t xline = 0; xline < screenWidth; xline++)
	{
		for(uint16_t yline = 0; yline < screenHeight; yline++)
		{
			color = (CHIP8_GetPixel(xline,yline) == 0U) ? backColor : frontColor;
			for(uint8_t px = 0; px < pixelSize; px++)
			{
				for(uint8_t py = 0; py < pixelSize; py++)
				{
					spriteBuffer[(xline*pixelSize+px) + (yline*pixelSize+py)*(screenWidth*pixelSize)] = color;
				}
			}
		}
	}
	RAMN_SPI_DrawImage(screenStartX, screenStartY, (uint16_t)(pixelSize)*screenWidth, (uint16_t)(pixelSize)*screenHeight, (uint8_t*)spriteBuffer);
}

#endif
