ToyotaInfoTech/RAMN/firmware/RAMNV1/Core/Src/ramn_isotp.c

/*
 * ramn_isotp.c
 ******************************************************************************
 * @attention
 *
 * <h2><center>&copy; Copyright (c) 2021 TOYOTA MOTOR CORPORATION.
 * ALL RIGHTS RESERVED.</center></h2>
 *
 * This software component is licensed by TOYOTA MOTOR CORPORATION under BSD 3-Clause license,
 * the "License"; You may not use this file except in compliance with the
 * License. You may obtain a copy of the License at:
 *                        opensource.org/licenses/BSD-3-Clause
 *
 ******************************************************************************
 */

#include "ramn_isotp.h"

#if defined(ENABLE_ISOTP)

// Private Functions ----------------------------------

#define ISOTP_RX 0x1
#define ISOTP_TX 0x2

// Padding byte used to fill CAN-FD frames up to a valid CAN_DL.
#ifdef ISOTP_ANSWER_PADDING_BYTE
#define ISOTP_FD_PAD_BYTE ISOTP_ANSWER_PADDING_BYTE
#else
#define ISOTP_FD_PAD_BYTE 0x00U
#endif

// Rounds a raw payload length (0..64) up to the next valid CAN_DL and returns the FDCAN DLC enum.
// For len <= 8 the enum equals the byte count, so classic-CAN framing is unaffected.
static uint32_t isotp_len_to_dlc(uint8_t len)
{
	if (len <= 8U)  return (uint32_t)len;
	if (len <= 12U) return 9U;
	if (len <= 16U) return 10U;
	if (len <= 20U) return 11U;
	if (len <= 24U) return 12U;
	if (len <= 32U) return 13U;
	if (len <= 48U) return 14U;
	return 15U; // up to 64 bytes
}
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
